polymathrobotics/protective-stop/docs/Hardware.md

# Hardware

## Materials

- Raspberry Pi Zero 2 W ([Raspberry Pi](https://www.raspberrypi.com/products/raspberry-pi-zero-2-w/))
- UPS Expansion Board for Raspberry Pi Zero 2 W ([Geekworm](https://www.amazon.com/Geekworm-Raspberry-18650-Expansion-Include/dp/B0B74NT38D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,electronics,140&sr=1-3))
- Heatsink for Raspberry Pi Zero 2 W ([Geekworm](https://www.amazon.com/Geekworm-Raspberry-Heatsink-Aluminumn-Compatible/dp/B09QMBCXLB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))
- E-ink display ([Waveshare](https://www.amazon.com/2-13inch-Display-HAT-Two-Color-Raspberry/dp/B07Z1WYRQH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,aps,152&sr=8-5))
- Cell modem SIM7600X 4G HAT
- Push button ([uxcell](https://www.amazon.com/dp/B07Z2TY2SZ))
- ESP32
- Electrical wire ([Fermerry 28 AWG](https://www.fermerry.com/products/fermerry-28-awg-stranded-wire-silicone-cables-hook-up-wire-kit-6-colors-5ft-each-28-gauge-electrical-wire))
- E-Stop Button
- Electric tape
- 40-GPIO header ([Vilros](https://www.amazon.com/Vilros-Solderless-Hammer-Header-Raspberry/dp/B09XVPYYTX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,aps,160&sr=8-2))
- Cell modem SIM7600X 4G HAT
- microUSB to microUSB cable
- microUSB to USB cable

## Assembly Instructions
### Preliminary Steps
1. Tape over Raspberry Pi USB connections
<p align="center">
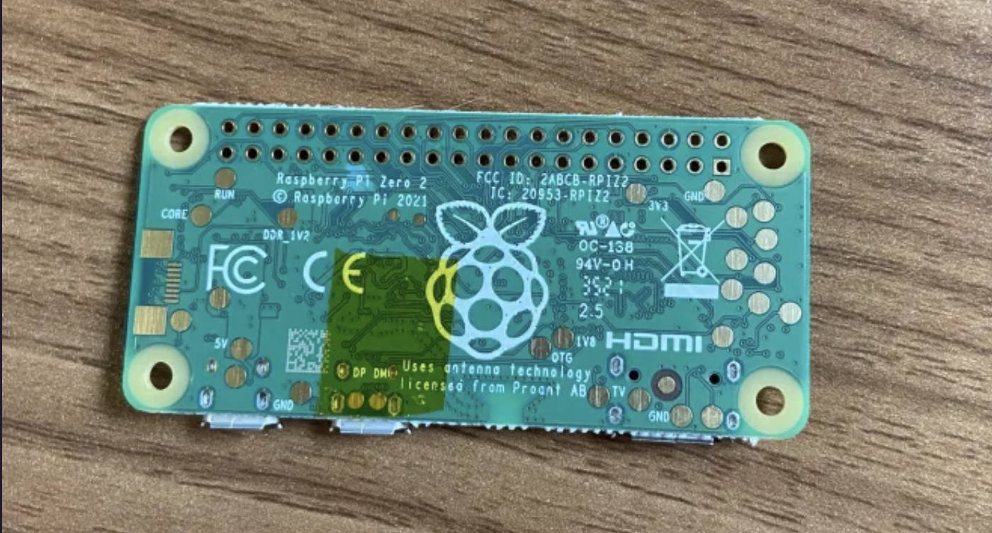
[picture p3: docs/img/rpi-tape.png]
  
</p>

2. Solder Raspberry Pi GPIO pin extender
- Use flux to make soldering easier
- Secure a few pins on each end first for better stability
- May want to clean singe marks from flux after soldering; we used a toothbrush and water for this.
<p align="center">
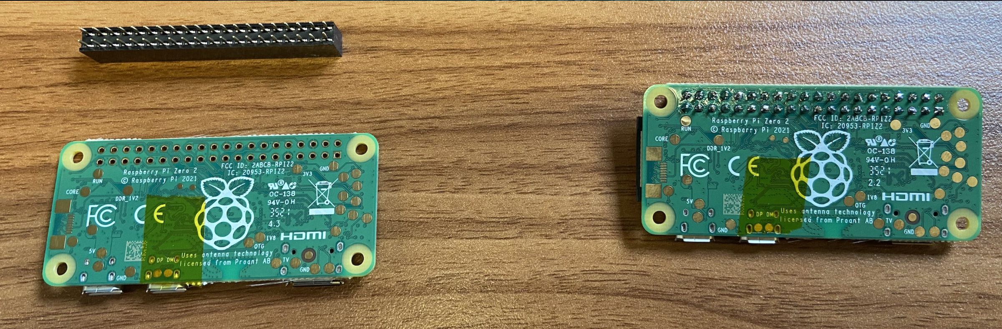
[picture p4: docs/img/soldered-rpi.png]
  <br><i> Left = before, right = after </i>
</p>

3. Apply Raspberry Pi heat sink.
- The Geekworm heatsink we used came with two thermal pads, one is 0.5mm and the other is 1mm. Make sure each pad goes in the right place! It comes with a diagram.
<p align="center">
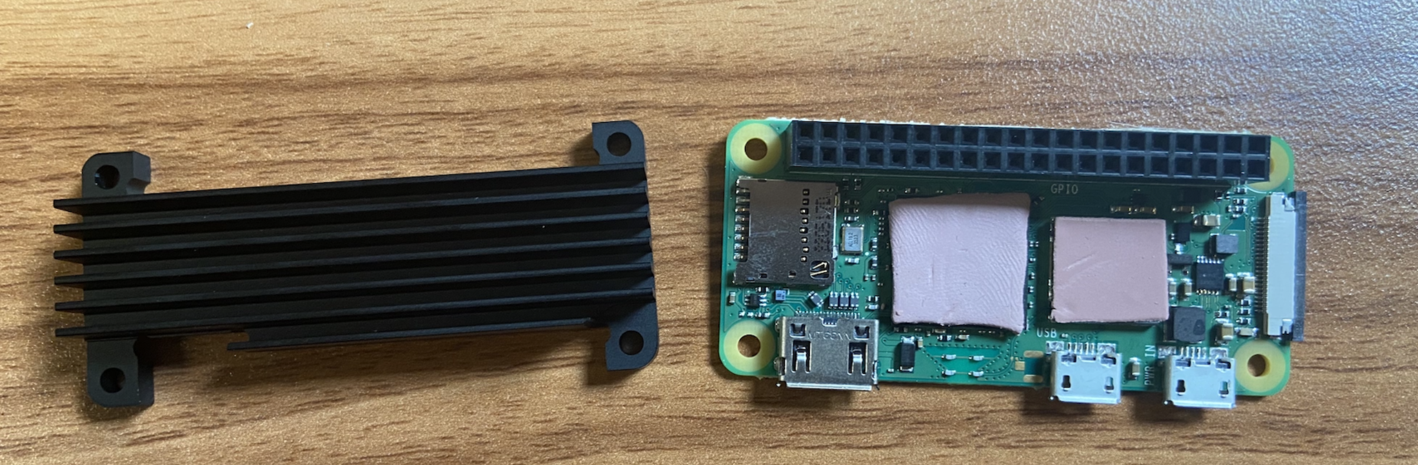
[picture p5: docs/img/heatsink.png]
   <br><i> Before </i>
</p>
<p align="center">
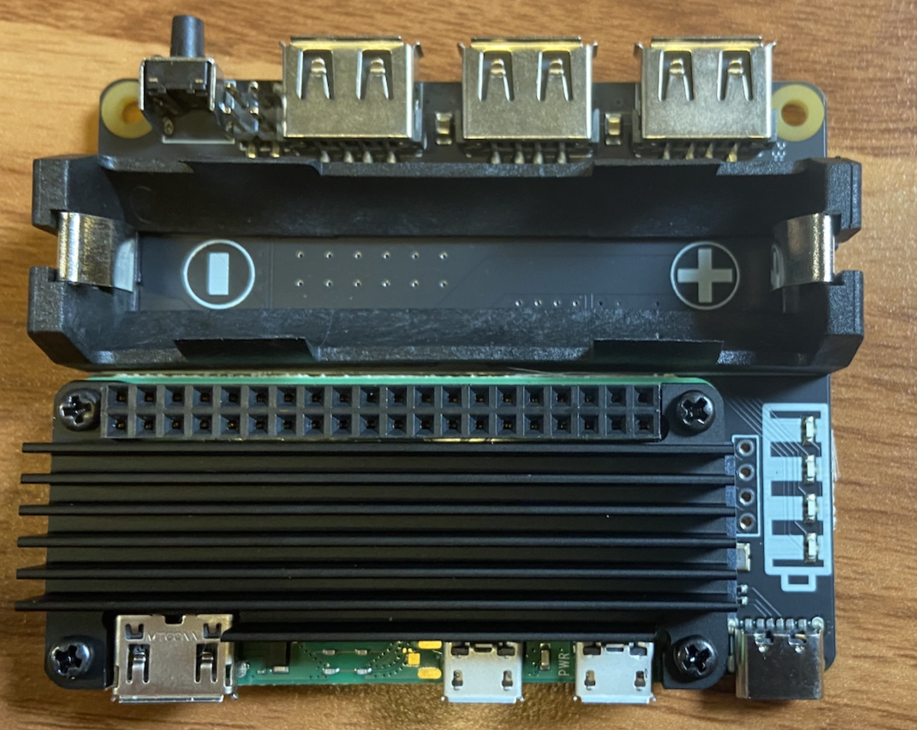
[picture p6: docs/img/applied-heatsink.png]
   <br><i> After </i>
</p>

- Screw on the heatsink to the Raspberry Pi, and through to the UPS.

<p align="center">
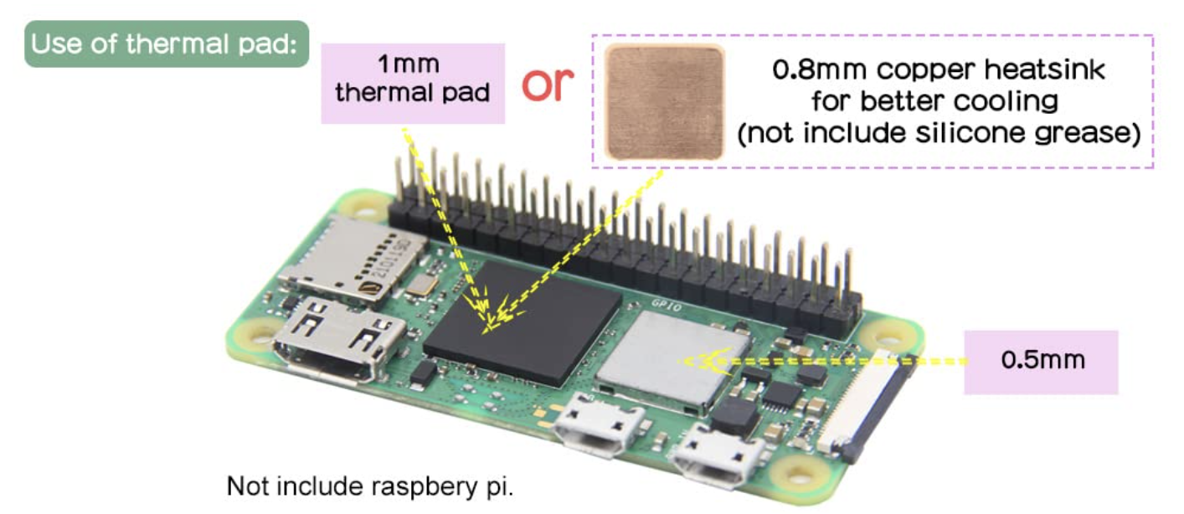
[picture p7: docs/img/thermal-pad-placement.png]
   <br><i> Thermal Pad Placement </i>
</p>

4. Add e-ink display to UPS using GPIO header.
<p align="center">
   <br><i> Top to bottom: UPS, GPIO header, e-ink display </i>
</p>
<p align="center">
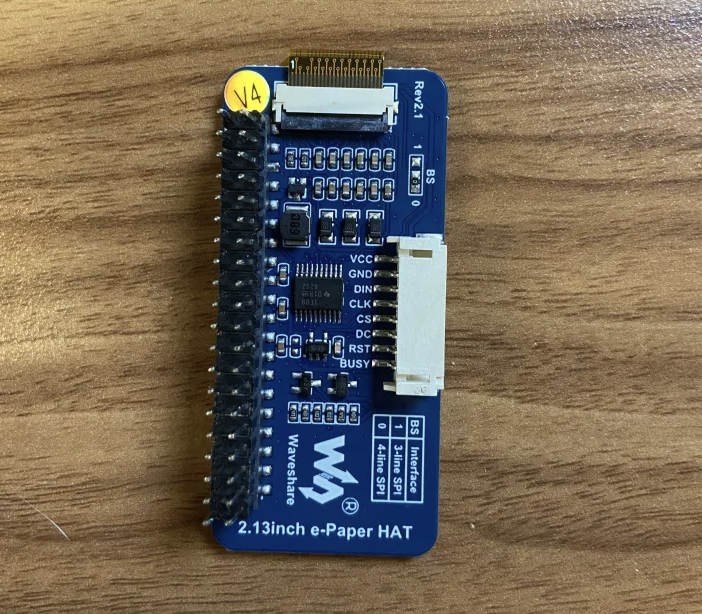
[picture p8: docs/img/gpio-2.png]
   <br><i> Add header to underside of e-ink </i>
</p>
<p align="center">
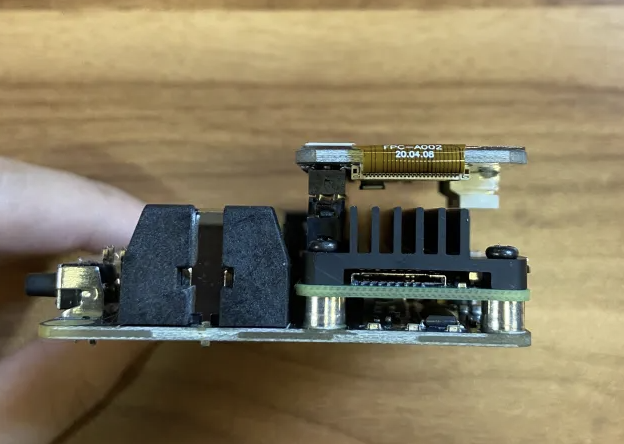
[picture p9: docs/img/gpio-3.png]
   <br><i> Install e-ink to UPS by plugging in GPIO header to pins </i>
</p>

## Wiring
Now it’s time to starting connecting stuff together. The connections at a glance are shown below.
```mermaid
graph TD
    USB-C -->|Power Out| UPS(UPS)
    UPS(UPS) -->|Power Out| R(Raspi)
    R -->|Control| ES(Eink Screen)
    R <-->|USB Power and Data| C(Cell Modem)
		C -->|USB Power and Data| E(ESP32)
    E -->|D2 to DI, + and GND| L(LED Ring)
    E -->|D22 to switch, + and GNDx2| PB(Power Button)
    PB -->|switch to input| UPS
    UPS -->|Lowbat to D34| E
    EB(Estop Button) -->|C to D18| E
    EB -->|NC to D21| E
    EB -->|NO to D19| E

    classDef component fill:#346beb,stroke:#333,stroke-width:2px;
    class USB-C,UPS,R,E,C,ES,L,PB,EB component;
```

### Wire Soldering
We will go through the wire soldering connections in the diagram above one by one. The color of the wires does not actually matter, but they are referred to throughout these instructions to enhance clarity.

1. Stop Button to ESP32
- Stop Button C → ESP32 D18 (Blue wire)
- Stop Button NO → ESP32 D19 (Yellow wire)
- Stop Button NC → ESP32 D21 (White wire)
- Don't forget to put O-ring on E-stop button!

<p align="center">
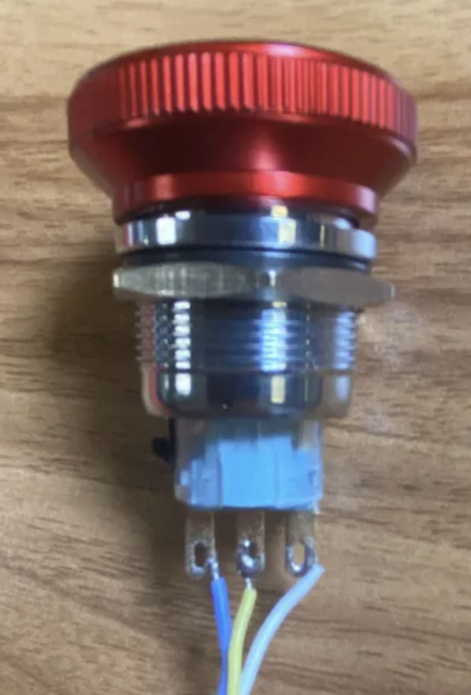
[picture p10: docs/img/stopbutton.png]
   <br><i> Stop button wiring </i>
</p>
<p align="center">
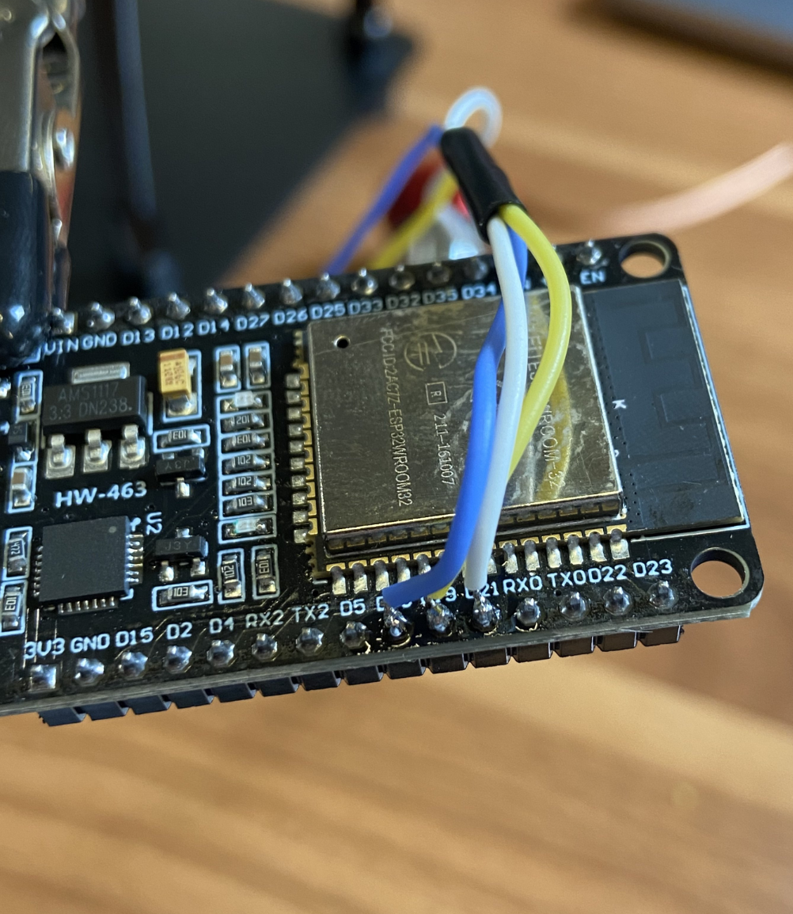
[picture p11: docs/img/stopbutton-esp.png]
   <br><i> Corresponding ESP32 wiring for stop button </i>
</p>

2. LED Ring to ESP32
- LED Ring DI → ESP32 D2 (Green wire)
- LED Ring PWR5V → ESP32 VIN (Red wire)
- LED Ring GND → ESP32 GND (Black wire)

<p align="center">
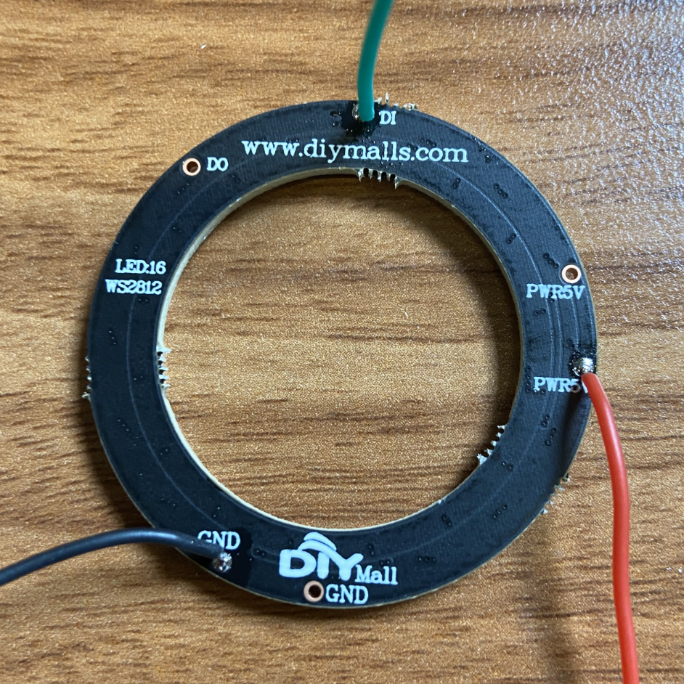
[picture p12: docs/img/ledring.png]
   <br><i> LED ring wiring </i>
</p>
<p align="center">
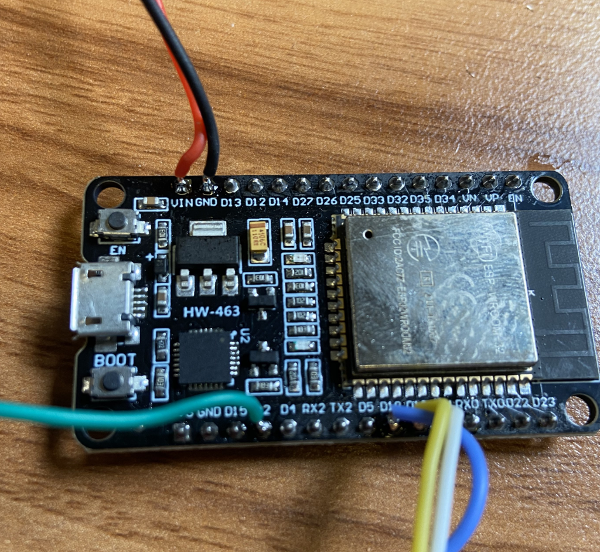
[picture p13: docs/img/ledring-esp32.png]
   <br><i> Corresponding ESP32 wiring for LED ring </i>
</p>

3. Power Button to ESP32 and UPS
- Power Button LED power terminal  → ESP32 D22 and UPS pin 3 (White wires)
- Power Button LED ground and switch contact A → ESP32 GND (Black wire)
- Power Button switch contact B→ ESP32 D23 (Red wire)
- Don’t forget to put O-ring on power button!

<p align="center">
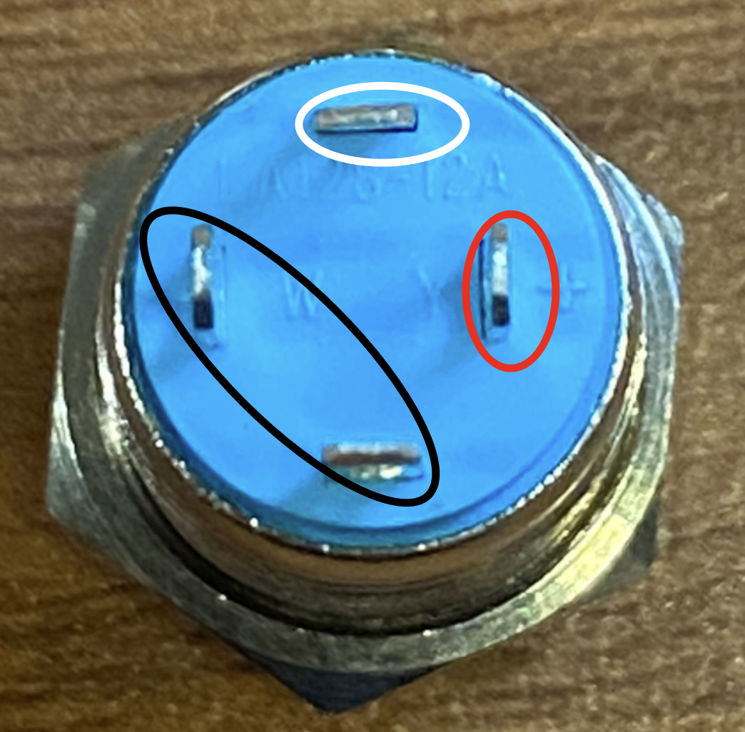
[picture p14: docs/img/powerbutton-colors.png]
   <br><i> Color of oval corresponds color of wire to connect to terminal. </i>
</p>
<p align="center">
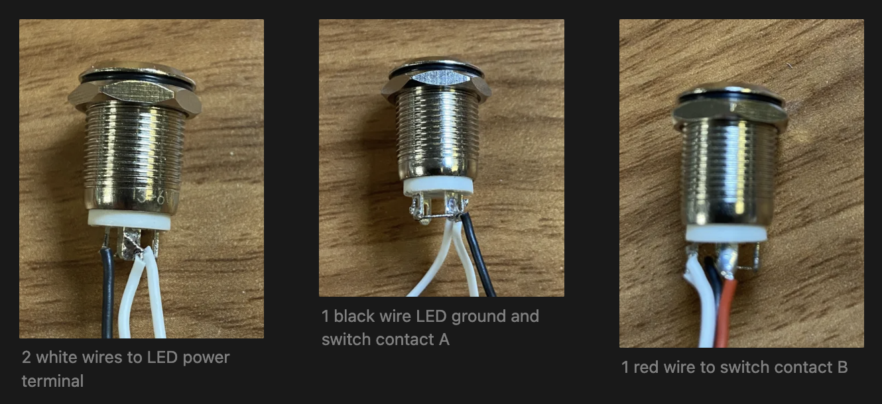
[picture p15: docs/img/powerbutton-wires.png]
   <br><i> Corresponding ESP32 wiring for LED ring </i>
</p>
<p align="center">
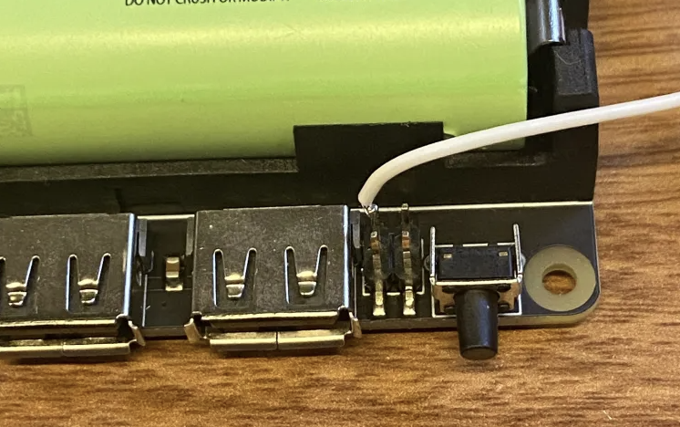
[picture p16: docs/img/powerbutton-white.png]
   <br><i> White wire soldered to UPS </i>
</p>
<p align="center">
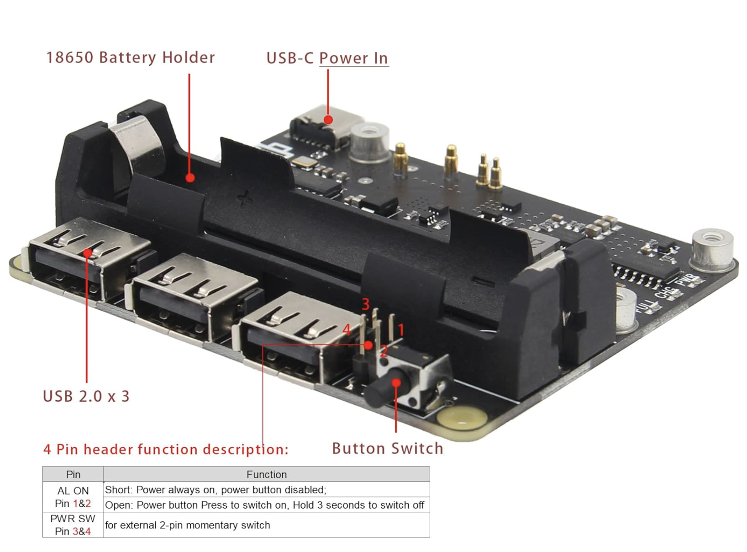
[picture p17: docs/img/ups-diagram.png]
   <br><i> Diagram of UPS </i>
</p>
<p align="center">
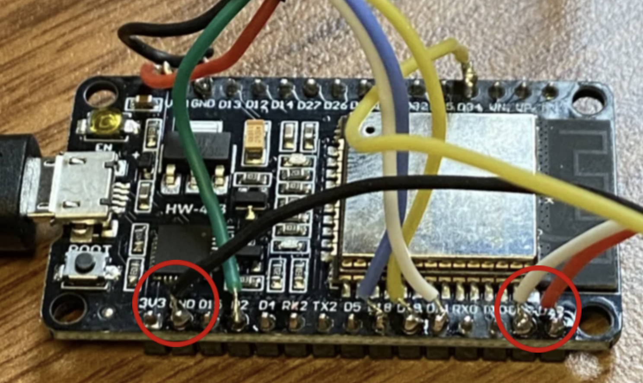
[picture p18: docs/img/powerbutton-esp32.png]
   <br><i> Black, white, and red wires soldered to ESP32 </i>
</p>

- Two white wires should be connected to the same terminal on the button (power button LED power terminal)
    - Tip: Solder these wires together first, and then solder them to the terminal
- The black wire is soldered across two power button terminals (power button LED ground and switch contact A)
    - Tip: Solder the end of the wire to the further terminal first, then the closer one
- Red wire is soldered normally

4. UPS to ESP32 (battery indicator)
- Lowbat to D34 (yellow wire)
<p align="center">
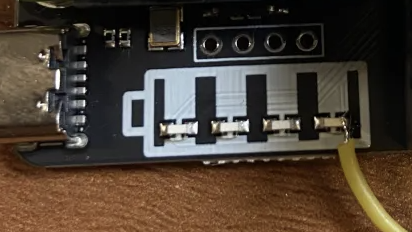
[picture p19: docs/img/ups-lowbat.png]
   <br><i> UPS lowbat soldering </i>
</p>
<p align="center">
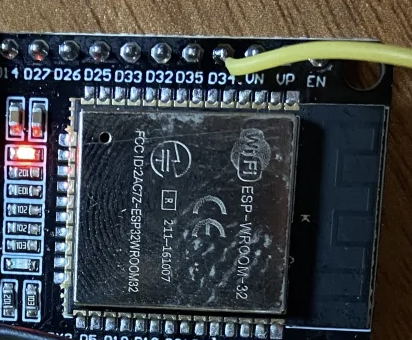
[picture p20: docs/img/esp-d34.png]
   <br><i> ESP32 pin D34 soldering </i>
</p>

5. Connect cell modem to ESP32 and RPi UPS.
- Modem USB → ESP32 microUSB (solid black cable)
- Modem microUSB → UPS microUSB (black/white cable)

6. Add battery to USP.
<p align="center">
   <br><i> Wired and connected system. </i>
</p>

7. Add antennas - if you want to use cellular data instead of WiFi
- Screw on antennas to AUX and MAIN pins on the underside of the modem

Now you're ready to move onto [Software](/docs/Software.md)
