polymathrobotics/protective-stop/docs/NET_ROBUSTNESS_2026-08-03.md

<!-- SPDX-FileCopyrightText: 2026 Polymath Robotics, Inc. -->
<!-- SPDX-License-Identifier: Apache-2.0 -->

# Network-Stack Robustness — USB-NCM + W5500 (2026-08-03)

Build `fa8b442`. Hardens the transport under the safety UDP link, driven by the
6 h soak finding that a USB-NCM remote intermittently dropped a heartbeat frame
(lwip `ERR_IF`, `g_sf_txdrv`) and — after enough consecutive drops — opened a
>1.2 s gap that would trip the machine's heartbeat STOP and force an operator
re-arm. Two research passes (USB-NCM + W5500) produced the proposals; the
low-risk, safety-latency-neutral subset was implemented and tested.

## Root cause (USB-NCM)

`sess_sendto()` did a single `sendto()`; on a transient NCM refusal (all IN NTBs
momentarily in-flight waiting for the USB host to poll bulk-IN) it dropped the
frame and waited a full 200 ms tick. On W5500 Ethernet this never happens (the
SPI driver queues the frame and returns OK). It is USB-NCM-specific, under TX load.

## Changes implemented

**USB-NCM**
- **NTB free-list 2 → 4** (`CONFIG_TINYUSB_NCM_IN_NTB_BUFFS_COUNT`, both projects) —
  widens the pool `tud_network_can_xmit()` draws from. +6.4 KB DRAM (heap verified
  fine, ~7.9 MB free).
- **Bounded yielding retry-on-ERR_IF** in `sess_sendto()` — up to 3 retries,
  `vTaskDelay(1)` between, so the lower-priority (5) TinyUSB task can free an NTB;
  the resend lands in the SAME 200 ms tick, no gap. **Gated on `errno == -1`
  (ERR_IF) only** — a genuinely dead link (route / ENOMEM) still fails on the first
  attempt, so **dead-link detection latency is unchanged** (the machine's 1.2 s
  heartbeat STOP and the 1.5 s local rebond threshold are untouched).
- **`pstop_sf_txdrv_recovered`** counter added to `/state.json` — counts transients
  absorbed by the retry, so the effect is measurable.

**W5500 Ethernet** (flawless in the soak; proactive margin only)
- SPI **`input_delay_ns = 20`** — sampling-edge margin (freq limit 40 MHz vs the
  20 MHz clock, so pure signal-integrity headroom, no behavioural change).
- **`LWIP_DHCP_RESTORE_LAST_IP`** — fast, deterministic IP reacquire after a link
  bounce instead of a full re-DHCP.

## Deferred (documented for a fault-injection-tested follow-up)

> **STATUS 2026-08-05 — the half-open black-hole family is now CLOSED + validated.**
> The three detection layers all shipped and are on main (`7867d4b`):
> - **W5500 health-watchdog + reset-recovery ladder** — `dcs_eth.c`
>   (`eth_blackhole_suspected()`, `DCS_ETHWD_REASON_BLACKHOLE`, RST-pulse ladder);
>   HW-validated on real silicon via a throwaway fault-injector (all 3 rungs,
>   `eth_recoveries` 0→3, restored each time). Closes the "driver wedges, link UP,
>   traffic black-holes, no disconnect event" field failure. **DONE.**
> - **Control-plane half-open** — coord watchdog fed by *received* activity only
>   (`ml_coord.c`; a send no longer masks a dead peer). **DONE.**
> - **Safety-path half-open** — validated 2026-08-05 via a controlled **sustained
>   90 s bidirectional black-hole** on a bonded slot (chaos proxy): the bond
>   detected within ~10 s (state→1, correctly *not* bonded — no false "up"), stayed
>   correctly not-bonded the whole 90 s (no wedge), and **recovered in 2.0 s** the
>   instant the path returned, no manual intervention. **NO WEDGE.**
>
> Remaining below are smaller, lower-value, or lockstep-timing-sensitive:

- **Instant demote-on-link-down** (event-driven failover kick; key failover off
  link state with asymmetric debounce) — partly covered by the `dcs_net_liveness`
  route supervisor (pstop-silence cross-check demote); a pure event-driven kick
  is the residual.
- TinyUSB task-priority bump (interacts with lockstep timing); Ethernet TX mutex
  (priority-inversion risk on the safety send); full static IP (deployment choice).

## Test results

**USB-NCM fix — PSTOP54 (USB-NCM, live safety link to machn), 40 min on `fa8b442`:**

| Metric | Result |
|---|---|
| `txdrv` (UNrecovered drops) | **0** |
| `txdrv_recovered` (absorbed by retry) | **5** |
| `pstop_rebonds` (steady-state) | **0** (2 total, both OTA-reboot settling) |
| reply rate (35 min window) | **100 %** (+10,500 / +10,500) |
| free heap | stable ~7.9 MB |

Before the fix (6 h soak): 17 `txdrv` drops + ~9 steady-state rebonds. After: 0
drops, 0 steady-state rebonds, 5 transients cleanly recovered. The nuisance-stop
precursor is eliminated, and because the retry is ERR_IF-gated the dead-link STOP
latency is unchanged.

**Armed safety-function regression — DUT (`0x01d7f344`) via HIL relays on `fa8b442`:**

| Step | Result |
|---|---|
| loops open (pressed) | both-phase sampling detects open (e_hi → 0) |
| arm (press → release) | machine → **OK (armed)** |
| press while armed | machine → **STOP** |
| re-arm | machine → **OK (armed)** |
| ~105 s armed hold | **no spurious STOP** |

The transport changes did not regress the safety logic: arm / STOP / re-arm all
correct, and every STOP transition mapped to a deliberate press.

## Protocol rebase to v1 (far-Hamming) + fleet migration

While this work was in flight, `6276bf0` ("Changing message values to avoid bit
flipping errors", J. Hinke) landed on `pstop`: `PSTOP_VERSION 0x00→0x01` and
far-Hamming message codewords (`OK 0x00→0x55`, `STOP 0x01→0x92`, `BOND→0xAD`,
`UNBOND→0x6A`) — the button-integrity safety improvement (zeroed/stuck/single-bit
→ invalid → STOP). It touches only `pstop_c`, so the transport fix above rebased
onto it cleanly (no conflict). **v0 and v1 are wire-incompatible** (version +
codewords), so the fleet was migrated in one pass.

The combined **v1 + transport-fix** build is `25c419f`. It was re-validated on the
wire before rollout (the earlier fa8b442 results were v0):

- **Bond on v1:** PSTOP54 ↔ machn re-bonded on the far-Hamming protocol, ~100 %
  reply rate, `sent` climbing steadily; USB retry active (`recovered` incrementing).
- **Armed on v1** (DUT via HIL relays + a v1 host runner): arm→RUN, press→STOP,
  re-arm→RUN, both-phase open-detection — all correct, identical to v0.
- **15-min stability** (all four units on `25c419f`): 0 reboots, 0 fault resets,
  `pstop_mismatch=0` on the continuously-running units, heap stable. (The DUT's
  transient mismatch count is an artifact of the armed test's sequential
  loop-relay switching — the intended single-channel discordance→STOP — not a
  fault.)

**Fleet:** `25c419f` published to the fleet for **both** projects (`pstop_remote`
and `machn_machine` — the first machn build ever on the fleet); all four reachable
units OTA-migrated to v1; offline units adopt v1 on next check-in.
