polymathrobotics/protective-stop/docs/img/pstop-ces.png

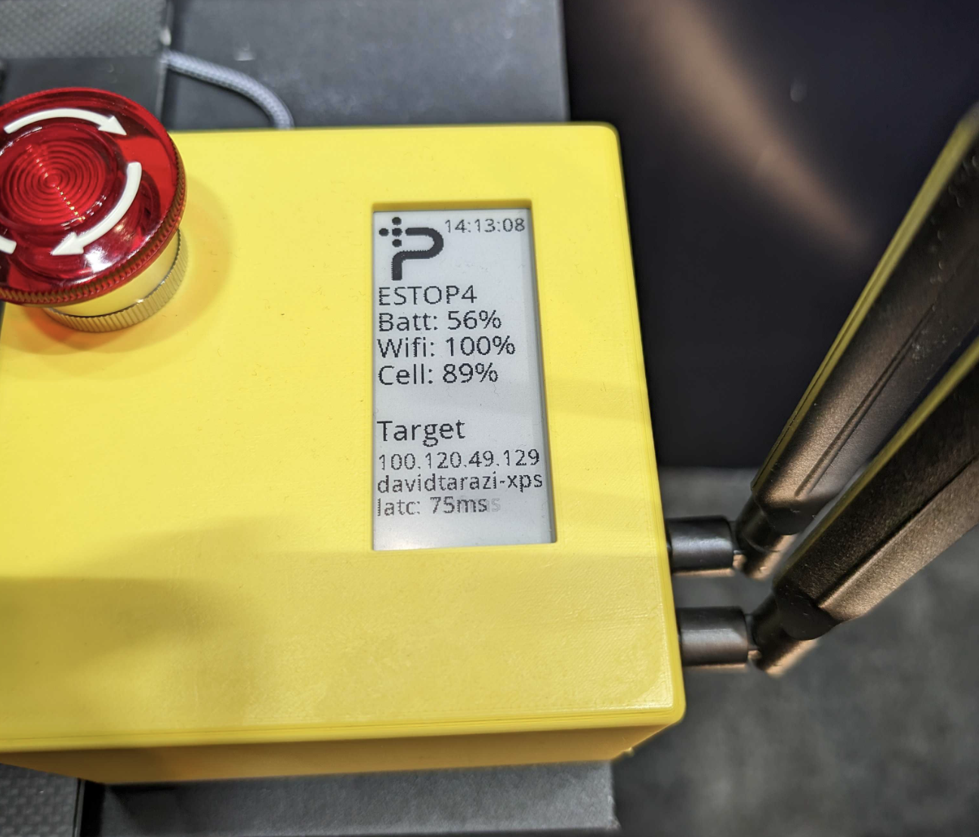
docs/img/pstop-ces.png
