polymathrobotics/protective-stop/firmware/components/dcs_support/src/dcs_support.c

// SPDX-FileCopyrightText: 2026 Polymath Robotics
// SPDX-License-Identifier: Apache-2.0

/**
 * @file dcs_support.c
 * @brief Top-level bring-up orchestrator. Calls into the per-file modules
 * (dcs_nvs, dcs_safety, dcs_boot, dcs_net_liveness, dcs_telemetry,
 * dcs_admin_pages) in the right order.
 */

#include "dcs_support.h"

#include <stdatomic.h>
#include <stdbool.h>
#include <stdlib.h>
#include <string.h>

#include "dcs_identity.h"
#include "dcs_internal.h"
#include "esp_heap_caps.h"
#include "esp_log.h"
#include "esp_secure_boot.h"
#include "esp_system.h"
#include "esp_timer.h" /* primary-machine freshness clock (same domain as main.c) */
#include "freertos/FreeRTOS.h"
#include "freertos/idf_additions.h" /* xTaskCreatePinnedToCoreWithCaps */
#include "freertos/semphr.h" /* operator-allowlist writer mutex */
#include "freertos/task.h"
#include "microlink.h"
#include "ml_app.h"
#include "ml_dev_tether.h"
#include "nvs_flash.h"
#include "panic_log.h"
#include "pstop/pstop_msg.h" /* PSTOP_MESSAGE_OK = machine armed/running (primary rule) */
#include "pstop_aux_channel.h" /* pstop_aux_role_t: remote self-role values */

static const char * TAG = "dcs_support";

/* See the doc comment on the declaration in dcs_internal.h for the contract a
 * PSRAM-stack task must honour (no flash/NVS, no ISR access). */
TaskHandle_t dcs_task_spawn_psram(
  TaskFunction_t fn, const char * name, uint32_t stack, void * arg, UBaseType_t prio, BaseType_t core)
{
  TaskHandle_t h = NULL;
  if (
    (xTaskCreatePinnedToCoreWithCaps(fn, name, stack, arg, prio, &h, core, MALLOC_CAP_SPIRAM | MALLOC_CAP_8BIT) ==
     pdPASS) &&
    (h != NULL))
  {
    ESP_LOGI(TAG, "task '%s' (%u B stack) created in PSRAM", name, (unsigned)stack);
    return h;
  }
  ESP_LOGW(TAG, "PSRAM stack for '%s' unavailable — falling back to internal RAM", name);
  h = NULL;
  if (xTaskCreatePinnedToCore(fn, name, stack, arg, prio, &h, core) == pdPASS) {
    return h;
  }
  ESP_LOGE(TAG, "task '%s' create FAILED", name);
  return NULL;
}

/* v15.27 — graceful Tailscale quiesce on any esp_restart() path.
 *
 * Runs from esp_register_shutdown_handler(), which fires for *any*
 * call to esp_restart() (admin restart, /api/usb_enable, the v15.24
 * auto-recovery, the never-brick fallback, etc) but does NOT fire on
 * panic. So this hook only mitigates *graceful* restarts where some
 * WG packet processing might be mid-flight. Work is limited to what's
 * safe with interrupts about to be disabled: a flag flip + a
 * vTaskSuspend, both effectively instant.
 *
 * Motivation: a single panic seen during a WiFi→USB mode transition,
 * backtrace lost (no serial on the test rig). Suspected race between
 * in-flight WG decrypt on ml_wg_mgr and esp_restart_noos's task-kill
 * sequence. Pausing DERP + suspending wg_mgr means no new packets
 * enter the processing pipeline from this point; anything already
 * mid-flight finishes within microseconds of the hook running. */
static void dcs_tailscale_quiesce_on_restart(void)
{
  microlink_pause_derp(true);
  if (g_dcs_wg_handle != NULL) {
    vTaskSuspend(g_dcs_wg_handle);
  }
}

/* === Process-wide state (declared extern in dcs_internal.h). =============== */
dcs_state_t g_dcs;

atomic_uint_fast32_t g_dcs_core_tick[2];
atomic_uint_fast32_t g_dcs_core_verdict[2];
atomic_uint_fast32_t g_dcs_xcheck_fault;
atomic_uint_fast32_t g_dcs_xcheck_hb[2];
atomic_uint_fast32_t g_dcs_gpio_cfg_fault;
atomic_uint_fast32_t g_dcs_load_pct[2];
atomic_uint_fast32_t g_dcs_estop_high_ok[2];
atomic_uint_fast32_t g_dcs_estop_low_ok[2];

atomic_uint_fast32_t g_dcs_pstop_sent;
atomic_uint_fast32_t g_dcs_pstop_replies;
atomic_uint_fast32_t g_dcs_pstop_last_msg; /* last PSTOP_MESSAGE_* received from the machine */
atomic_uint_fast32_t g_dcs_pstop_mismatch;
atomic_uint_fast32_t g_dcs_pstop_mm[7]; /* mismatch attribution — layout in dcs_internal.h */
atomic_uint_fast32_t g_dcs_pstop_mm_seq; /* seqlock for g_dcs_pstop_mm — see dcs_internal.h */
atomic_uint_fast64_t g_dcs_nvs_write; /* last dcs-side NVS write, start<<32 | duration — dcs_internal.h */
atomic_uint_fast32_t g_dcs_nvs_write_max; /* longest dcs-side NVS write this boot, ms */

void dcs_pstop_mm_snapshot(uint32_t out[7])
{
  /* Seqlock read: retry while the comparator is mid-write (odd) or wrote in
   * between. The writer runs once per 100 ms tick and the 7 stores take ~1 us,
   * so a retry is rare; after 8 tries return the last read (diagnostics only). */
  for (int attempt = 0; attempt < 8; attempt++) {
    uint32_t s1 = (uint32_t)atomic_load(&g_dcs_pstop_mm_seq);
    if ((s1 & 1u) != 0u) {
      taskYIELD();
      continue;
    }
    for (int i = 0; i < 7; i++) {
      out[i] = (uint32_t)atomic_load(&g_dcs_pstop_mm[i]);
    }
    atomic_thread_fence(memory_order_acquire); /* payload loads stay above the seq re-read */
    if ((uint32_t)atomic_load(&g_dcs_pstop_mm_seq) == s1) return;
  }
  /* 8 collisions in a row (writer runs once per 100 ms tick — effectively
   * never): deliver a best-effort copy rather than leave `out` untouched. */
  for (int i = 0; i < 7; i++) {
    out[i] = (uint32_t)atomic_load(&g_dcs_pstop_mm[i]);
  }
}

atomic_uint_fast32_t g_dcs_pstop_send_fail;
atomic_uint_fast32_t g_dcs_pstop_sf_nomem;
atomic_uint_fast32_t g_dcs_pstop_sf_route;
atomic_uint_fast32_t g_dcs_pstop_sf_txdrv;
atomic_uint_fast32_t g_dcs_pstop_sf_txdrv_recovered;
atomic_uint_fast32_t g_dcs_pstop_sf_other;
atomic_uint_fast32_t g_dcs_pstop_sf_enotconn;
atomic_uint_fast32_t g_dcs_pstop_sf_enotconn_kicks;
atomic_int g_dcs_pstop_sf_last_errno;
atomic_uint_fast32_t g_dcs_pstop_rtt_ms;
atomic_uint_fast64_t g_dcs_pstop_last_reply_ms;
atomic_uint_fast32_t g_dcs_pstop_peer_ip;
atomic_uint_fast32_t g_dcs_pstop_peer_port;

atomic_uint_fast64_t g_dcs_pstop_slot_ep[DCS_PSTOP_MAX_MACHINES];
atomic_uint_fast32_t g_dcs_pstop_slot_id[DCS_PSTOP_MAX_MACHINES];
/* Per-slot rebond request generation. /api/pstop_peers?slot=N&rebond=1 bumps
 * it; the comparator restarts that session's bond when it sees a new value.
 * This is how a REJECTED session (machine answered BOND with UNBOND) is
 * retried on command — it never retries on its own. */
static atomic_uint_fast32_t g_dcs_pstop_slot_rebond_gen[DCS_PSTOP_MAX_MACHINES];

void dcs_pstop_request_rebond(int slot)
{
  if ((slot >= 0) && (slot < DCS_PSTOP_MAX_MACHINES)) {
    atomic_fetch_add(&g_dcs_pstop_slot_rebond_gen[slot], 1u);
  }
}

uint32_t dcs_pstop_rebond_generation(int slot)
{
  if ((slot < 0) || (slot >= DCS_PSTOP_MAX_MACHINES)) {
    return 0u;
  }
  return (uint32_t)atomic_load(&g_dcs_pstop_slot_rebond_gen[slot]);
}

atomic_uint_fast32_t g_dcs_pstop_m_sent[DCS_PSTOP_MAX_MACHINES];
atomic_uint_fast32_t g_dcs_pstop_m_replies[DCS_PSTOP_MAX_MACHINES];
atomic_uint_fast32_t g_dcs_pstop_m_send_fail[DCS_PSTOP_MAX_MACHINES];
atomic_uint_fast32_t g_dcs_pstop_m_rebonds[DCS_PSTOP_MAX_MACHINES];
atomic_uint_fast32_t g_dcs_pstop_m_rtt_ms[DCS_PSTOP_MAX_MACHINES];
atomic_uint_fast32_t g_dcs_pstop_m_hb_ms[DCS_PSTOP_MAX_MACHINES];
atomic_uint_fast32_t g_dcs_pstop_m_last_msg[DCS_PSTOP_MAX_MACHINES];
atomic_uint_fast32_t g_dcs_pstop_m_state[DCS_PSTOP_MAX_MACHINES];
atomic_uint_fast64_t g_dcs_pstop_m_last_reply_ms[DCS_PSTOP_MAX_MACHINES];

/* Endpoint packing for g_dcs_pstop_slot_ep (see dcs_internal.h). */
#define PSTOP_EP_CONFIGURED (1ULL << 63)

static uint64_t pstop_ep_pack(bool configured, uint32_t ip, uint16_t port)
{
  return (configured ? PSTOP_EP_CONFIGURED : 0ULL) | ((uint64_t)ip << 16) | (uint64_t)port;
}

TaskHandle_t g_dcs_wg_handle;
atomic_int g_dcs_wg_paused;

atomic_uint_fast32_t g_dcs_heap_min_internal = UINT32_MAX;

atomic_int g_dcs_active_iface;
/* W5500 health-watchdog counters (written by dcs_eth.c's eth_wd task). */
atomic_uint_fast32_t g_dcs_eth_recoveries;
atomic_uint_fast32_t g_dcs_eth_rec_r1;
atomic_uint_fast32_t g_dcs_eth_rec_r2;
atomic_uint_fast32_t g_dcs_eth_rec_r3;
atomic_uint_fast32_t g_dcs_eth_rec_reason;
atomic_uint_fast32_t g_dcs_eth_spi_err;
atomic_uint_fast32_t g_dcs_eth_int_low_ticks;
atomic_uint_fast32_t g_dcs_eth_int_low_max_ms;
atomic_uint_fast32_t g_dcs_rgb_cycles;
atomic_uint_fast32_t g_dcs_pstop_rebonds;
atomic_uint_fast32_t g_dcs_relay_fault_a;
atomic_uint_fast32_t g_dcs_relay_fault_b;
atomic_uint_fast32_t g_dcs_relay_stop;
atomic_uint_fast32_t g_dcs_relay_feedback_monitored;
atomic_uint_fast32_t g_dcs_machn_arm_owner;
atomic_uint_fast32_t g_dcs_machn_restart_state;
atomic_uint_fast32_t g_dcs_machn_r_id[DCS_MACHN_MAX_REMOTES];
atomic_uint_fast32_t g_dcs_machn_r_state[DCS_MACHN_MAX_REMOTES];
atomic_uint_fast32_t g_dcs_machn_r_age_ms[DCS_MACHN_MAX_REMOTES];
atomic_uint_fast32_t g_dcs_machn_r_rtt_ms[DCS_MACHN_MAX_REMOTES];
atomic_uint_fast32_t g_dcs_machn_r_ip[DCS_MACHN_MAX_REMOTES];
atomic_uint_fast32_t g_dcs_machn_r_stop_only[DCS_MACHN_MAX_REMOTES];

/* Admission lists (allowlist + denylist) RAM caches. Lock-free for readers:
 * the safety cores scan these atomics from their remote_details callback,
 * never touching NVS/flash. Each slot holds 0 (empty) or a real remote id, so
 * a torn read can never FABRICATE a match — it can at worst miss a just-added
 * id or briefly still see a just-removed one (a lag, harmless: admission only
 * decides whether a remote may BOND, never whether it may re-arm). Writers
 * (admin API + boot load) serialize on g_dcs_lists_mtx and persist to NVS.
 * Loaded once at boot in dcs_support_init(); both empty on blank NVS =>
 * every remote is admitted. */
static atomic_uint_fast32_t g_dcs_lists[DCS_LIST_COUNT][DCS_MAX_LIST_IDS];
static SemaphoreHandle_t g_dcs_lists_mtx; /* writer serialization only */

static void pstop_slot_pins_sync(void);

static const char * list_name(dcs_list_t which)
{
  if (which == DCS_LIST_DENY) return "denylist";
  if (which == DCS_LIST_PIN) return "pinlist";
  return "allowlist";
}

static void dcs_lists_load_from_nvs(void)
{
  (void)dcs_nvs_migrate_legacy_operators(); /* must precede the PIN list load */
  for (int w = 0; w < DCS_LIST_COUNT; w++) {
    uint32_t ids[DCS_MAX_LIST_IDS];
    int n = dcs_nvs_read_list((dcs_list_t)w, ids);
    for (int i = 0; i < DCS_MAX_LIST_IDS; i++) {
      atomic_store(&g_dcs_lists[w][i], (i < n) ? ids[i] : 0u);
    }
    ESP_LOGI(TAG, "%s: %d id(s) loaded", list_name((dcs_list_t)w), n);
  }
}

bool dcs_list_contains(dcs_list_t which, uint32_t remote_id)
{
  if ((remote_id == 0u) || ((unsigned)which >= DCS_LIST_COUNT)) {
    return false;
  }
  for (int i = 0; i < DCS_MAX_LIST_IDS; i++) {
    if ((uint32_t)atomic_load(&g_dcs_lists[which][i]) == remote_id) {
      return true;
    }
  }
  return false;
}

int dcs_list_get(dcs_list_t which, uint32_t out[DCS_MAX_LIST_IDS])
{
  int n = 0;
  if ((unsigned)which >= DCS_LIST_COUNT) {
    return 0;
  }
  for (int i = 0; i < DCS_MAX_LIST_IDS; i++) {
    uint32_t id = (uint32_t)atomic_load(&g_dcs_lists[which][i]);
    if (id != 0u) {
      out[n++] = id;
    }
  }
  return n;
}

bool dcs_admission_allows(uint32_t remote_id)
{
  /* Deny wins. An empty allowlist admits everyone (the default, "open");
   * a populated one admits only listed ids ("paranoid"). */
  if (dcs_list_contains(DCS_LIST_DENY, remote_id)) {
    return false;
  }
  uint32_t probe[DCS_MAX_LIST_IDS];
  if (dcs_list_get(DCS_LIST_ALLOW, probe) == 0) {
    return true;
  }
  return dcs_list_contains(DCS_LIST_ALLOW, remote_id);
}

bool dcs_peer_pin_wanted(uint32_t remote_id)
{
  if (dcs_list_contains(DCS_LIST_DENY, remote_id)) {
    return false; /* never protect a slot for an id admission will refuse */
  }
  return dcs_list_contains(DCS_LIST_ALLOW, remote_id) || dcs_list_contains(DCS_LIST_PIN, remote_id);
}

/* Serialize a write, snapshot the current ids into a compact array, persist to
 * NVS, and only on NVS success republish the compacted set into the RAM cache.
 * Keeping NVS the source of truth means a failed write leaves RAM unchanged. */
static esp_err_t dcs_list_commit(dcs_list_t which, const uint32_t * ids, int count)
{
  esp_err_t r = dcs_nvs_write_list(which, ids, count);
  if (r != ESP_OK) {
    return r;
  }
  for (int i = 0; i < DCS_MAX_LIST_IDS; i++) {
    atomic_store(&g_dcs_lists[which][i], (i < count) ? ids[i] : 0u);
  }
  return ESP_OK;
}

esp_err_t dcs_list_add(dcs_list_t which, uint32_t remote_id)
{
  if ((remote_id == 0u) || ((unsigned)which >= DCS_LIST_COUNT)) {
    return ESP_ERR_INVALID_ARG;
  }
  if (g_dcs_lists_mtx != NULL) {
    (void)xSemaphoreTake(g_dcs_lists_mtx, portMAX_DELAY);
  }
  uint32_t ids[DCS_MAX_LIST_IDS];
  int n = dcs_list_get(which, ids);
  esp_err_t r = ESP_OK;
  bool present = false;
  for (int i = 0; i < n; i++) {
    if (ids[i] == remote_id) {
      present = true;
      break;
    }
  }
  if (present) {
    r = ESP_OK; /* idempotent */
  } else if (n >= DCS_MAX_LIST_IDS) {
    r = ESP_ERR_NO_MEM;
  } else {
    ids[n++] = remote_id;
    r = dcs_list_commit(which, ids, n);
  }
  if (g_dcs_lists_mtx != NULL) {
    (void)xSemaphoreGive(g_dcs_lists_mtx);
  }
  return r;
}

esp_err_t dcs_list_del(dcs_list_t which, uint32_t remote_id)
{
  if ((unsigned)which >= DCS_LIST_COUNT) {
    return ESP_ERR_INVALID_ARG;
  }
  if (g_dcs_lists_mtx != NULL) {
    (void)xSemaphoreTake(g_dcs_lists_mtx, portMAX_DELAY);
  }
  uint32_t ids[DCS_MAX_LIST_IDS];
  int n = dcs_list_get(which, ids);
  int w = 0;
  for (int i = 0; i < n; i++) {
    if (ids[i] != remote_id) {
      ids[w++] = ids[i];
    }
  }
  esp_err_t r = (w == n) ? ESP_OK /* absent: nothing to persist */ : dcs_list_commit(which, ids, w);
  if (g_dcs_lists_mtx != NULL) {
    (void)xSemaphoreGive(g_dcs_lists_mtx);
  }
  return r;
}

/* Remote self-role RAM mirror. Loaded at boot; dcs_role_set() updates it live
 * (both safety cores read it per frame), so a role change takes effect on the
 * next pstop frame without a reboot. */
static atomic_uint_fast32_t g_dcs_role;

static void dcs_role_load_from_nvs(void)
{
  uint8_t role = dcs_nvs_read_role(); /* fail-safe: stop_only unless explicitly operator */
  atomic_store(&g_dcs_role, role);
  ESP_LOGI(TAG, "remote role: %s", pstop_aux_role_str((pstop_aux_role_t)role));
}

uint8_t dcs_role_get(void)
{
  return (uint8_t)atomic_load(&g_dcs_role);
}

esp_err_t dcs_role_set(uint8_t role)
{
  if ((role != PSTOP_AUX_ROLE_STOP_ONLY) && (role != PSTOP_AUX_ROLE_OPERATOR)) {
    return ESP_ERR_INVALID_ARG;
  }
  esp_err_t r = dcs_nvs_write_role(role);
  if (r == ESP_OK) {
    atomic_store(&g_dcs_role, role);
    ESP_LOGI(TAG, "remote role -> %s (live)", pstop_aux_role_str((pstop_aux_role_t)role));
  }
  return r;
}

/* === DERP region auto-negotiation: §4.2 primary-machine feed ===============
 *
 * microlink derives the chip's DERP home region from the machine-slot table +
 * per-slot session state, both of which live HERE (the lock-free telemetry
 * atomics the comparator publishes every tick). Q1 decision (2026-08-10):
 * primary = the LOWEST-index bonded+ARMED slot — slot order is NVS
 * configuration, identical after power loss, whereas arming ORDER is history
 * that cannot be reconstructed across a reboot.
 *
 * "Armed" proxy per slot: session BONDED (state==2) AND the machine's last
 * reply message is PSTOP_MESSAGE_OK (a machn replies OK only while its safety
 * chain is closed/armed; STOP/BOND replies mean not armed) AND the reply is
 * FRESH (within the machine's own bond-drop window, hb×5, floor 3 s — the
 * same invariant sess_rebond_after_ms mirrors in main.c).
 *
 * Runs on the wg_mgr task at its 3 s self-heal cadence: atomics only, no
 * NVS/flash, no locks. On machn the slot table is empty, so this returns
 * nothing and microlink keeps the machine's legacy (fleet-anchor) behavior —
 * machines are region-authoritative and never follow a remote (design §4). */
static void dcs_primary_machine_info(void * ctx, microlink_primary_machine_info_t * out)
{
  (void)ctx;
  out->armed_primary_ip = 0u;
  out->configured_count = 0;
  const uint64_t now = (uint64_t)(esp_timer_get_time() / 1000);
  for (int i = 0; i < DCS_PSTOP_MAX_MACHINES; i++) {
    uint64_t ep = (uint64_t)atomic_load(&g_dcs_pstop_slot_ep[i]);
    if ((ep & PSTOP_EP_CONFIGURED) == 0ULL) {
      continue;
    }
    uint32_t ip = (uint32_t)((ep >> 16) & 0xFFFFFFFFULL);
    if (ip == 0u) {
      continue;
    }
    if (out->configured_count < MICROLINK_PRIMARY_MAX_MACHINES) {
      out->configured_ips[out->configured_count++] = ip; /* slot order preserved */
    }
    if (out->armed_primary_ip == 0u) { /* first (lowest) armed slot wins — Q1 */
      uint32_t st = (uint32_t)atomic_load(&g_dcs_pstop_m_state[i]);
      uint32_t lm = (uint32_t)atomic_load(&g_dcs_pstop_m_last_msg[i]);
      uint64_t lr = (uint64_t)atomic_load(&g_dcs_pstop_m_last_reply_ms[i]);
      uint32_t hb = (uint32_t)atomic_load(&g_dcs_pstop_m_hb_ms[i]);
      uint64_t fresh_ms = (hb != 0u) ? ((uint64_t)hb * 5u) : 3000u;
      if (fresh_ms < 3000u) {
        fresh_ms = 3000u;
      }
      bool bonded = (st == 2u); /* SESS_BONDED */
      bool armed = (lm == (uint32_t)PSTOP_MESSAGE_OK);
      bool fresh = (lr != 0u) && (now >= lr) && ((now - lr) <= fresh_ms);
      if (bonded && armed && fresh) {
        out->armed_primary_ip = ip;
      }
    }
  }
}

/* === Public API ============================================================ */

/* Must run before NVS init: a secure image on an unsecured chip would burn the
 * NVS HMAC key. Aborting lets OTA rollback restore the previous image. */
static void dcs_check_security_profile(void)
{
#if CONFIG_SECURE_BOOT
  const bool image_secure = true;
#else
  const bool image_secure = false;
#endif
  if (esp_secure_boot_enabled() != image_secure) {
    ESP_LOGE(TAG, "image and chip disagree on Secure Boot: refusing to run");
    abort();
  }
}

dcs_boot_state_t dcs_support_init(void)
{
  /* RTC_NOINIT log capture: must be first so we don't miss early boot logs. */
  panic_log_init();
  dcs_check_security_profile();

  /* Power-on sign of life: whole ring dim purple, before any network or
     * NVS work. Overwritten by the ring task once bring-up completes. */
  dcs_pstop_ring_bootsign();

  /* v15.27: register the Tailscale-quiesce shutdown hook before anything
     * else can call esp_restart(). Idempotent — runs once per process. */
  esp_err_t hook_err = esp_register_shutdown_handler(dcs_tailscale_quiesce_on_restart);
  if (hook_err != ESP_OK) {
    ESP_LOGW(TAG, "shutdown handler register: %s", esp_err_to_name(hook_err));
  }

  /* NVS up first — both our boot-counter and the usb_enabled flag live there. */
  esp_err_t nvs_err = nvs_flash_init();
  if ((nvs_err == ESP_ERR_NVS_NO_FREE_PAGES) || (nvs_err == ESP_ERR_NVS_NEW_VERSION_FOUND)) {
    esp_err_t erase_err = nvs_flash_erase();
    if (erase_err != ESP_OK) {
      ESP_LOGW(TAG, "nvs_flash_erase: %s", esp_err_to_name(erase_err));
    }
    nvs_err = nvs_flash_init();
  }
  if (nvs_err != ESP_OK) {
    ESP_LOGW(TAG, "nvs_flash_init early: %s", esp_err_to_name(nvs_err));
  }

  /* Boot-counter accounting + rollback decision. Does NOT return if it
     * decides to invoke esp_ota_mark_app_invalid_rollback_and_reboot(). */
  dcs_safety_account_boot();

  /* Lifetime health counters: boots/flash/OTA accounting. Must run before
     * ml_app_start (which may mark the OTA image valid on connect) so the
     * PENDING_VERIFY state is still observable. */
  dcs_health_init();

  /* Resolve NVS-backed user toggles. */
  g_dcs.usb_enabled = dcs_nvs_read_usb_enabled();
  g_dcs.ts_boot_en = dcs_nvs_read_ts_boot_en();

  /* Safety ladder: boot_count==1 → drop direct-UDP path only;
     *                 boot_count>=2 → full Tailscale pause. */
  if (g_dcs.ts_boot_en && (g_dcs.boot_count == 1u)) {
    ESP_LOGW(TAG, "SAFETY: bc=1 — forcing DERP-only mode for this boot");
    g_dcs.derp_only_mode = true;
  } else if (g_dcs.ts_boot_en && (g_dcs.boot_count >= 2u)) {
    ESP_LOGW(
      TAG,
      "SAFETY: ts_boot=1 but boot_count=%u — forcing Tailscale "
      "paused for this boot (safe mode)",
      g_dcs.boot_count);
    g_dcs.ts_boot_en = false;
  } else {
    /* boot_count 0: no safety-ladder action */
  }
  ESP_LOGI(
    TAG, "Boot: usb_enabled=%d ts_boot_en=%d boot_count=%u", g_dcs.usb_enabled, g_dcs.ts_boot_en, g_dcs.boot_count);

  /* TWDT keep-alive. */
  dcs_safety_start_heartbeat();

  /* USB "PSTOPxx" unit number: admin-set value from NVS, or 0 = derive from
     * the chip ID. Must be set before ml_app_start (its try_alt_network hook can
     * bring up the USB tether, which fixes the descriptor at TinyUSB install). */
  ml_dev_tether_set_unit_number(dcs_nvs_read_pstop_unit_num());

  /* ml_app config — same defaults as the pre-refactor main.c. */
  ml_app_config_t cfg = ML_APP_CONFIG_DEFAULT();
  cfg.max_peers = 128; /* PSRAM-backed; load paths budgeted */
  /* Register on the tailnet as "pstop-01xxxxxx", matching the black-channel
     * device ID (dcs_identity_*). Stable per unit; static buffer, safe to hold. */
  cfg.device_name = dcs_identity_hostname();
  ESP_LOGI(
    TAG,
    "Identity: tailnet=%s  pstop device_id=0x%08x "
    "(machine must allow_unlisted or list this ID)",
    dcs_identity_hostname(),
    (unsigned)dcs_identity_device_id());
  cfg.enable_disco = !g_dcs.derp_only_mode;
  cfg.enable_stun = !g_dcs.derp_only_mode;
  cfg.try_alt_network = dcs_boot_try_tether_or_skip;
  cfg.alt_network_timeout_ms = 30000;
  /* httpd URI-handler budget. The server holds 16 + this many slots
     * (ml_app.c). microlink registers ~20 of its own (config panel + /admin
     * API + fleet-ota + verbose) and dcs_admin_pages registers 18; at 16 the
     * total overflowed 32 and the LAST-registered app routes silently failed
     * to register (observed: /api/pstop_num and /api/enter_download 404'd on
     * shipped firmware). dcs now registers 29 on the remote (incl.
     * /api/admission + /api/role GET+POST, /api/health GET + reset POST);
     * 36 gives 52 total slots with headroom — re-check this
     * arithmetic whenever a route is added on either side. */
  cfg.max_user_uri_handlers = 36;
  g_dcs.app = ml_app_start(&cfg);
  g_dcs.ml_handle = ml_app_get_microlink(g_dcs.app);

  /* If an alt network took the default route, ml_app skipped wifi_init.
     * Bring the WiFi driver up in idle mode so admin endpoints touching
     * esp_wifi_* behave — EXCEPT on the wired-Ethernet path, where WiFi is
     * never used and esp_wifi_init() would burn ~30-50 KB of internal RAM we
     * can't spare (internal heap runs tight on this build; that pressure was
     * tipping the chip into intermittent allocation-failure panics). The
     * esp_wifi_* admin calls return ESP_ERR_WIFI_NOT_INIT rather than crash
     * when the driver is absent, so skipping it is safe. */
  if (dcs_boot_alt_network_won()) {
    if (dcs_eth_has_ip()) {
      /* Wired Ethernet: do NOT init the WiFi driver. It costs ~20-25 KB
             * internal RAM, and MEASURED (2026-06-23): always-initialising it
             * here on the eth path crushed heap_min to ~1.9 KB once the Tailscale
             * DERP-TLS handshake ran concurrently (vs ~46 KB skipped) and started
             * tripping early-boot reboots — i.e. it re-creates the very OOM
             * pressure the skip exists to avoid. The esp_wifi_* NULL-deref this
             * once caused in the admin status endpoints (an unguarded call on the
             * not-init driver crash-looped the device) is fixed at the call sites
             * instead — see the guards in dcs_admin_pages.c (/state.json) and
             * ml_config_httpd.c (/api/monitor). */
      ESP_LOGI(
        TAG,
        "wired Ethernet active — skipping WiFi driver init "
        "to preserve internal RAM (esp_wifi admin calls guarded)");
    } else {
      dcs_boot_wifi_idle_init(); /* USB-NCM path: keep WiFi driver */
    }
  }

  /* Onboard WS2812 RGB LED: colour = active interface (live), blink = IP
     * last octet. Replaces ml_ip_blink (which drove GPIO21 as a plain pin —
     * can't clock the board's addressable LED). */
  dcs_rgb_start();

  /* 16-LED WS2812 ring on GPIO17 — PSTOP safety state (separate from the
     * onboard single LED's network indicator). */
  dcs_pstop_ring_start();

  /* Initial peer targets (NVS-backed, legacy single peer migrated into
     * slot 0) — main.c reads the slots via dcs_get_pstop_peer_slot() before
     * and during the comparator's run. Slot 0 mirrors to the legacy atomics. */
  {
    dcs_pstop_peer_rec_t peers[DCS_PSTOP_MAX_MACHINES];
    dcs_nvs_read_pstop_peers(peers);
    for (int i = 0; i < DCS_PSTOP_MAX_MACHINES; i++) {
      atomic_store(&g_dcs_pstop_slot_ep[i], pstop_ep_pack(peers[i].configured, peers[i].ip, peers[i].port));
      atomic_store(&g_dcs_pstop_slot_id[i], peers[i].machine_id);
    }
    atomic_store(&g_dcs_pstop_peer_ip, peers[0].configured ? peers[0].ip : 0u);
    atomic_store(&g_dcs_pstop_peer_port, peers[0].port);
  }
  /* Pin every configured machine target in the WG peer table so the cap
     * trim can never orphan a safety link (see pstop_slot_pins_sync). */
  pstop_slot_pins_sync();

  /* DERP region auto-negotiation (§4.2): feed microlink the machine-slot
     * table + arming state so it can home on the PRIMARY machine's region
     * (lowest bonded+armed slot — Q1) and MBB-switch when the primary moves.
     * Registered on both roles: on machn the table is empty, so this is a
     * no-op feed and the machine keeps its legacy region behavior. */
  if (g_dcs.ml_handle != NULL) {
    microlink_set_primary_machine_cb(g_dcs.ml_handle, dcs_primary_machine_info, NULL);
  }

  /* Operator allowlist (machine-role authorization): create the writer mutex
     * and load the persisted ids into the lock-free RAM cache BEFORE main.c
     * spawns the safety cores (their remote_details callback reads the cache)
     * and before the admin API can mutate it. Empty on blank NVS = every remote
     * stop-only = safe. */
  g_dcs_lists_mtx = xSemaphoreCreateMutex();
  if (g_dcs_lists_mtx == NULL) {
    ESP_LOGW(TAG, "operator-allowlist mutex alloc failed — add/del will run unserialized");
  }
  dcs_lists_load_from_nvs();
  dcs_role_load_from_nvs(); /* remote self-role mirror, before the safety cores spawn */

  /* Register the admin pages now that ml_app is up. */
  dcs_admin_pages_register(g_dcs.app);

  /* Verbose ml_* logging — kept from pre-refactor; helps catch wedges. */
  esp_log_level_set("ml_wg_mgr", ESP_LOG_INFO);
  esp_log_level_set("ml_net_io", ESP_LOG_INFO);
  esp_log_level_set("ml_derp", ESP_LOG_INFO);
  esp_log_level_set("wireguard_lwip", ESP_LOG_INFO);
  esp_log_level_set("microlink", ESP_LOG_INFO);

  dcs_telemetry_start_sampler();
  dcs_health_start(); /* 1 Hz: NVS flush of lifetime counters + wear checks */
  dcs_net_supervisor_start(); /* 1 Hz Eth>USB>WiFi default-route enforcer */
  dcs_net_liveness_start();
  dcs_net_inet_start(); /* internet reachability -> red LED when down */

  /* Cache the ml_wg_mgr handle for the legacy /api/wg toggle. */
  g_dcs_wg_handle = xTaskGetHandle("ml_wg_mgr");

  /* Mirror into the public boot-state struct. */
  dcs_boot_state_t bs = {
    .usb_enabled = g_dcs.usb_enabled,
    .ts_boot_en = g_dcs.ts_boot_en,
    .derp_only_mode = g_dcs.derp_only_mode,
    .boot_count = g_dcs.boot_count,
    .reset_reason = g_dcs.reset_reason,
    .ctrl_reset_cause = g_dcs.ctrl_reset_cause,
    .ml_handle = g_dcs.ml_handle,
    .app = g_dcs.app,
  };
  return bs;
}

void dcs_support_finalize(const dcs_boot_state_t * bs)
{
  (void)bs;
  /* Mark current OTA partition valid — does NOT clear boot_count, so the
     * crash-loop signal survives until the Layer-4 age-out fires. */
  dcs_safety_mark_ota_valid();

  /* Layer 4: age-out the crash counter after sustained healthy uptime,
     * and (v15.24) auto-restart out of derp-only mode on success. */
  dcs_safety_start_bc_clear();

  /* If Tailscale was supposed to start paused this boot, suspend
     * ml_wg_mgr now (after our NVS reads completed earlier). The 500 ms
     * delay lets wg_mgr finish its own NVS peer-cache load. */
  if ((!g_dcs.ts_boot_en) && (g_dcs_wg_handle != NULL)) {
    microlink_pause_derp(true);
    vTaskDelay(pdMS_TO_TICKS(500));
    vTaskSuspend(g_dcs_wg_handle);
    atomic_store(&g_dcs_wg_paused, 1);
    ESP_LOGW(TAG, "ml_wg_mgr task suspended + DERP paused at boot");
  } else {
    ESP_LOGI(TAG, "Tailscale tasks active at boot (safety net: 4-crash rollback)");
  }
}

/* === Telemetry sinks ======================================================= */

void dcs_publish_core_tick(int core_id, uint32_t tick, uint8_t verdict)
{
  if ((core_id < 0) || (core_id > 1)) {
    return;
  }
  atomic_store(&g_dcs_core_tick[core_id], tick);
  atomic_store(&g_dcs_core_verdict[core_id], verdict);
  /* Lifetime press / mismatch edge counting (non-safety telemetry). */
  dcs_health_note_core_tick(core_id, tick, verdict);
}

void dcs_publish_xcheck(uint32_t fault, uint32_t hb0, uint32_t hb1)
{
  atomic_store(&g_dcs_xcheck_fault, fault);
  atomic_store(&g_dcs_xcheck_hb[0], hb0);
  atomic_store(&g_dcs_xcheck_hb[1], hb1);
}

void dcs_publish_gpio_cfg(uint32_t fault)
{
  atomic_store(&g_dcs_gpio_cfg_fault, fault);
}

void dcs_publish_estop(int core_id, bool high_ok, bool low_ok)
{
  if ((core_id < 0) || (core_id > 1)) {
    return;
  }
  atomic_store(&g_dcs_estop_high_ok[core_id], high_ok ? 1u : 0u);
  atomic_store(&g_dcs_estop_low_ok[core_id], low_ok ? 1u : 0u);
}

void dcs_publish_comparator(
  uint32_t sent, uint32_t mismatch, uint32_t send_fail, uint64_t last_reply_ms, uint32_t rtt_ms)
{
  atomic_store(&g_dcs_pstop_sent, sent);
  atomic_store(&g_dcs_pstop_mismatch, mismatch);
  atomic_store(&g_dcs_pstop_send_fail, send_fail);
  atomic_store(&g_dcs_pstop_last_reply_ms, last_reply_ms);
  atomic_store(&g_dcs_pstop_rtt_ms, rtt_ms);
}

void dcs_publish_relay_fault(uint32_t fault_a_ticks, uint32_t fault_b_ticks, bool stop_active, bool monitored)
{
  atomic_store(&g_dcs_relay_fault_a, fault_a_ticks);
  atomic_store(&g_dcs_relay_fault_b, fault_b_ticks);
  atomic_store(&g_dcs_relay_stop, stop_active ? 1u : 0u);
  atomic_store(&g_dcs_relay_feedback_monitored, monitored ? 1u : 0u);
}

void dcs_publish_machn_remote(
  int slot, uint32_t remote_id, uint32_t ip, uint32_t state, uint32_t age_ms, uint32_t rtt_ms, bool stop_only)
{
  if ((slot < 0) || (slot >= DCS_MACHN_MAX_REMOTES)) {
    return;
  }
  atomic_store(&g_dcs_machn_r_id[slot], remote_id);
  atomic_store(&g_dcs_machn_r_ip[slot], ip);
  atomic_store(&g_dcs_machn_r_state[slot], state);
  atomic_store(&g_dcs_machn_r_age_ms[slot], age_ms);
  atomic_store(&g_dcs_machn_r_rtt_ms[slot], rtt_ms);
  atomic_store(&g_dcs_machn_r_stop_only[slot], stop_only ? 1u : 0u);
}

void dcs_publish_machn_arm(uint32_t remote_stop_id, uint32_t restart_state)
{
  atomic_store(&g_dcs_machn_arm_owner, remote_stop_id);
  atomic_store(&g_dcs_machn_restart_state, restart_state);
}

void dcs_publish_pstop_sf_causes(
  uint32_t nomem,
  uint32_t route,
  uint32_t txdrv,
  uint32_t txdrv_recovered,
  uint32_t other,
  uint32_t enotconn,
  uint32_t enotconn_kicks,
  int last_errno)
{
  atomic_store(&g_dcs_pstop_sf_nomem, nomem);
  atomic_store(&g_dcs_pstop_sf_route, route);
  atomic_store(&g_dcs_pstop_sf_txdrv, txdrv);
  atomic_store(&g_dcs_pstop_sf_txdrv_recovered, txdrv_recovered);
  atomic_store(&g_dcs_pstop_sf_other, other);
  atomic_store(&g_dcs_pstop_sf_enotconn, enotconn);
  atomic_store(&g_dcs_pstop_sf_enotconn_kicks, enotconn_kicks);
  atomic_store(&g_dcs_pstop_sf_last_errno, last_errno);
}

bool dcs_tailnet_connected(void)
{
  return (g_dcs.ml_handle != NULL) && (microlink_get_state(g_dcs.ml_handle) == ML_STATE_CONNECTED);
}

void dcs_request_announce(void)
{
  if (g_dcs.ml_handle != NULL) {
    (void)microlink_request_announce(g_dcs.ml_handle);
  }
}

void dcs_publish_pstop_peer(uint32_t peer_ip, uint16_t peer_port)
{
  /* Legacy single-peer setter (/api/pstop_peer, provisioning tooling) = slot 0
   * with the default machine id. */
  esp_err_t werr = dcs_pstop_set_peer_slot(0, true, peer_ip, peer_port, DCS_PSTOP_DEFAULT_MACHINE_ID);
  if (werr != ESP_OK) {
    ESP_LOGW(TAG, "persist pstop peer: %s", esp_err_to_name(werr));
  }
}

/* Pin every configured slot target in the WG peer table (and unpin an IP
 * only when NO remaining slot uses it — two slots may target one host on
 * different ports). Without the pin, a machine that joined the tailnet
 * after this chip's last full netmap — or one with no recent traffic —
 * is trimmed by the peer cap and every BOND dies with EHOSTUNREACH. */
static void pstop_slot_pins_sync(void)
{
  if (g_dcs.ml_handle == NULL) {
    return;
  }
  for (int i = 0; i < DCS_PSTOP_MAX_MACHINES; i++) {
    uint64_t ep = (uint64_t)atomic_load(&g_dcs_pstop_slot_ep[i]);
    bool cfg = (ep & PSTOP_EP_CONFIGURED) != 0ULL;
    uint32_t ip = (uint32_t)((ep >> 16) & 0xFFFFFFFFULL);
    if (cfg && (ip != 0u)) {
      microlink_pin_peer_ip(g_dcs.ml_handle, ip, true);
    }
  }
}

esp_err_t dcs_pstop_set_peer_slot(int slot, bool configured, uint32_t ip, uint16_t port, uint32_t machine_id)
{
  if ((slot < 0) || (slot >= DCS_PSTOP_MAX_MACHINES)) {
    return ESP_ERR_INVALID_ARG;
  }
  /* Unpin the OLD target if this slot had one and no other slot shares it. */
  uint64_t old_ep = (uint64_t)atomic_load(&g_dcs_pstop_slot_ep[slot]);
  uint32_t old_ip = (uint32_t)((old_ep >> 16) & 0xFFFFFFFFULL);
  if (((old_ep & PSTOP_EP_CONFIGURED) != 0ULL) && (old_ip != 0u) && (g_dcs.ml_handle != NULL)) {
    bool shared = false;
    for (int i = 0; i < DCS_PSTOP_MAX_MACHINES; i++) {
      if (i == slot) continue;
      uint64_t ep = (uint64_t)atomic_load(&g_dcs_pstop_slot_ep[i]);
      if (((ep & PSTOP_EP_CONFIGURED) != 0ULL) && ((uint32_t)((ep >> 16) & 0xFFFFFFFFULL) == old_ip)) {
        shared = true;
        break;
      }
    }
    if (!shared && !(configured && (ip == old_ip))) {
      microlink_pin_peer_ip(g_dcs.ml_handle, old_ip, false);
    }
  }
  /* Live update first (comparator picks it up next tick)... */
  atomic_store(&g_dcs_pstop_slot_id[slot], machine_id);
  atomic_store(&g_dcs_pstop_slot_ep[slot], pstop_ep_pack(configured, ip, port));
  pstop_slot_pins_sync();
  if (slot == 0) {
    atomic_store(&g_dcs_pstop_peer_ip, configured ? ip : 0u);
    atomic_store(&g_dcs_pstop_peer_port, port);
  }
  /* ...then persist the whole table (read-modify-write of the blob). */
  dcs_pstop_peer_rec_t peers[DCS_PSTOP_MAX_MACHINES];
  dcs_nvs_read_pstop_peers(peers);
  /* run-47 shakeout: writing slot N>0 on a device whose machine target came
   * from the legacy key / compiled default (blob slot 0 unconfigured) must
   * not strand that ACTIVE target — once a blob exists it is authoritative,
   * so an unseeded slot 0 silently drops the live machine bond on the next
   * reload. Seed slot 0 from the live atomics before persisting. */
  if ((slot != 0) && !peers[0].configured) {
    uint64_t ep0 = (uint64_t)atomic_load(&g_dcs_pstop_slot_ep[0]);
    if ((ep0 & PSTOP_EP_CONFIGURED) != 0ULL) {
      peers[0].configured = true;
      peers[0].ip = (uint32_t)((ep0 >> 16) & 0xFFFFFFFFULL);
      peers[0].port = (uint16_t)(ep0 & 0xFFFFULL);
      peers[0].machine_id = (uint32_t)atomic_load(&g_dcs_pstop_slot_id[0]);
    }
  }
  peers[slot].configured = configured;
  peers[slot].ip = ip;
  peers[slot].port = port;
  peers[slot].machine_id = machine_id;
  return dcs_nvs_write_pstop_peers(peers);
}

void dcs_get_pstop_peer_slot(
  int slot, bool * configured, uint32_t * peer_ip, uint16_t * peer_port, uint32_t * machine_id)
{
  uint64_t ep = 0;
  uint32_t id = 0;
  if ((slot >= 0) && (slot < DCS_PSTOP_MAX_MACHINES)) {
    ep = atomic_load(&g_dcs_pstop_slot_ep[slot]);
    id = (uint32_t)atomic_load(&g_dcs_pstop_slot_id[slot]);
  }
  if (configured != NULL) {
    *configured = (ep & PSTOP_EP_CONFIGURED) != 0ULL;
  }
  if (peer_ip != NULL) {
    *peer_ip = (uint32_t)((ep >> 16) & 0xFFFFFFFFu);
  }
  if (peer_port != NULL) {
    *peer_port = (uint16_t)(ep & 0xFFFFu);
  }
  if (machine_id != NULL) {
    *machine_id = id;
  }
}

void dcs_publish_pstop_machine(
  int slot,
  uint32_t sent,
  uint32_t replies,
  uint32_t send_fail,
  uint32_t rebonds,
  uint32_t hb_ms,
  uint64_t last_reply_ms,
  uint32_t rtt_ms,
  uint8_t last_msg,
  uint8_t sess_state)
{
  if ((slot < 0) || (slot >= DCS_PSTOP_MAX_MACHINES)) {
    return;
  }
  atomic_store(&g_dcs_pstop_m_sent[slot], sent);
  atomic_store(&g_dcs_pstop_m_replies[slot], replies);
  atomic_store(&g_dcs_pstop_m_send_fail[slot], send_fail);
  atomic_store(&g_dcs_pstop_m_rebonds[slot], rebonds);
  atomic_store(&g_dcs_pstop_m_last_reply_ms[slot], last_reply_ms);
  atomic_store(&g_dcs_pstop_m_rtt_ms[slot], rtt_ms);
  atomic_store(&g_dcs_pstop_m_hb_ms[slot], hb_ms);
  atomic_store(&g_dcs_pstop_m_last_msg[slot], last_msg);
  atomic_store(&g_dcs_pstop_m_state[slot], sess_state);
}

void dcs_get_initial_pstop_peer(uint32_t * peer_ip, uint16_t * peer_port)
{
  if (peer_ip != NULL) {
    *peer_ip = atomic_load(&g_dcs_pstop_peer_ip);
  }
  if (peer_port != NULL) {
    *peer_port = (uint16_t)atomic_load(&g_dcs_pstop_peer_port);
  }
}

uint32_t dcs_get_vpn_ip(void)
{
  return (g_dcs.ml_handle != NULL) ? microlink_get_vpn_ip(g_dcs.ml_handle) : 0u;
}

void dcs_notify_priority_health(bool healthy)
{
  if (g_dcs.ml_handle != NULL) {
    microlink_notify_priority_health(g_dcs.ml_handle, healthy);
  }
}

void dcs_notify_peer_health(uint32_t vpn_ip, bool healthy)
{
  if (g_dcs.ml_handle != NULL) {
    microlink_notify_peer_health(g_dcs.ml_handle, vpn_ip, healthy);
  }
}

void dcs_untrack_peer_health(uint32_t vpn_ip)
{
  if (g_dcs.ml_handle != NULL) {
    microlink_untrack_peer_health(g_dcs.ml_handle, vpn_ip);
  }
}
