polymathrobotics/protective-stop/components/microlink/src/microlink.c

// SPDX-FileCopyrightText: 2026 Polymath Robotics
// SPDX-License-Identifier: Apache-2.0

/**
 * @file microlink.c
 * @brief MicroLink v2 - Public API and Task Orchestration
 *
 * Creates all FreeRTOS tasks, queues, and event groups.
 * Provides the public API that the application calls.
 */

#include <fcntl.h>
#include <stdio.h>
#include <string.h>

#include "cJSON.h"
#include "esp_heap_caps.h"
#include "esp_log.h"
#include "esp_mac.h"
#include "esp_random.h"
#include "esp_timer.h"
#include "esp_wifi.h"
#include "lwip/sockets.h"
#include "lwip/sys.h"
#include "microlink_internal.h"
#include "nvs.h"
#include "nvs_flash.h"
#include "wireguardif.h" /* peer path-recovery diagnostics in microlink_get_peer_info */

static const char * TAG = "microlink";

/* NVS keys */
#define NVS_NAMESPACE "microlink"
#define NVS_KEY_MACHINE_PRI "machine_pri"
#define NVS_KEY_MACHINE_PUB "machine_pub"
#define NVS_KEY_WG_PRI "wg_private"
#define NVS_KEY_WG_PUB "wg_public"
#define NVS_KEY_DISCO_PRI "disco_pri"
#define NVS_KEY_DISCO_PUB "disco_pub"
#define NVS_KEY_VPN_IP "vpn_ip"

/* X25519 from x25519.h */
#include "x25519.h"

/* ============================================================================
 * Key Management (loaded once at init, read-only after)
 * ========================================================================== */

static void generate_keypair(uint8_t * private_key, uint8_t * public_key)
{
  esp_fill_random(private_key, 32);
  private_key[0] &= 248;
  private_key[31] &= 127;
  private_key[31] |= 64;
  x25519_base(public_key, private_key, 1);
}

static esp_err_t load_or_generate_keys(microlink_t * ml)
{
  nvs_handle_t nvs;
  esp_err_t err = nvs_open(NVS_NAMESPACE, NVS_READWRITE, &nvs);
  if (err != ESP_OK) {
    ESP_LOGW(TAG, "NVS open failed (%d), generating ephemeral keys", err);
    generate_keypair(ml->machine_private_key, ml->machine_public_key);
    generate_keypair(ml->wg_private_key, ml->wg_public_key);
    generate_keypair(ml->disco_private_key, ml->disco_public_key);
    return ESP_OK;
  }

  size_t key_len = 32;
  bool need_save = false;

  /* Machine key */
  if (nvs_get_blob(nvs, NVS_KEY_MACHINE_PRI, ml->machine_private_key, &key_len) != ESP_OK) {
    generate_keypair(ml->machine_private_key, ml->machine_public_key);
    need_save = true;
    ESP_LOGI(TAG, "Generated new machine key");
  } else {
    key_len = 32;
    nvs_get_blob(nvs, NVS_KEY_MACHINE_PUB, ml->machine_public_key, &key_len);
  }

  /* WireGuard key */
  key_len = 32;
  if (nvs_get_blob(nvs, NVS_KEY_WG_PRI, ml->wg_private_key, &key_len) != ESP_OK) {
    generate_keypair(ml->wg_private_key, ml->wg_public_key);
    need_save = true;
    ESP_LOGI(TAG, "Generated new WireGuard key");
  } else {
    key_len = 32;
    nvs_get_blob(nvs, NVS_KEY_WG_PUB, ml->wg_public_key, &key_len);
  }

  /* DISCO key */
  key_len = 32;
  if (nvs_get_blob(nvs, NVS_KEY_DISCO_PRI, ml->disco_private_key, &key_len) != ESP_OK) {
    generate_keypair(ml->disco_private_key, ml->disco_public_key);
    need_save = true;
    ESP_LOGI(TAG, "Generated new DISCO key");
  } else {
    key_len = 32;
    nvs_get_blob(nvs, NVS_KEY_DISCO_PUB, ml->disco_public_key, &key_len);
  }

  /* Last-known VPN IP (best effort). Persisted on every registration so a
     * reboot can bring the WG interface up + preseed cached peers BEFORE (or
     * without) coordination connectivity — the cold-bond far-side recovery
     * (2026-08-08 bench: rebooted machine ignored operator handshakes for
     * 27 min while its netmap never re-arrived). A stale value is harmless:
     * registration overwrites it and ml_wg_mgr re-syncs the netif address. */
  {
    uint32_t stored_ip = 0;
    if (nvs_get_u32(nvs, NVS_KEY_VPN_IP, &stored_ip) == ESP_OK && stored_ip != 0) {
      ml->vpn_ip = stored_ip;
      char ip_str[16];
      microlink_ip_to_str(stored_ip, ip_str);
      ESP_LOGI(TAG, "VPN IP restored from NVS: %s (pre-registration)", ip_str);
    }
  }

  if (need_save) {
    nvs_set_blob(nvs, NVS_KEY_MACHINE_PRI, ml->machine_private_key, 32);
    nvs_set_blob(nvs, NVS_KEY_MACHINE_PUB, ml->machine_public_key, 32);
    nvs_set_blob(nvs, NVS_KEY_WG_PRI, ml->wg_private_key, 32);
    nvs_set_blob(nvs, NVS_KEY_WG_PUB, ml->wg_public_key, 32);
    nvs_set_blob(nvs, NVS_KEY_DISCO_PRI, ml->disco_private_key, 32);
    nvs_set_blob(nvs, NVS_KEY_DISCO_PUB, ml->disco_public_key, 32);
    nvs_commit(nvs);
    ESP_LOGI(TAG, "Keys saved to NVS");
  } else {
    ESP_LOGI(TAG, "Keys loaded from NVS");
  }

  nvs_close(nvs);
  return ESP_OK;
}

/* Persist the current VPN IP (see the load note in load_or_generate_keys).
 * Called from the coord task whenever registration/map assigns the IP —
 * never from the safety tick. Write-on-change only: re-registrations with
 * the same address (the common case) cost zero flash wear. */
static bool s_vpn_ip_forgotten; /* until reboot: re-registers must not re-persist the old IP */

void ml_ident_persist_vpn_ip(microlink_t * ml)
{
  if (!ml || ml->vpn_ip == 0 || s_vpn_ip_forgotten) {
    return;
  }
  nvs_handle_t nvs;
  if (nvs_open(NVS_NAMESPACE, NVS_READWRITE, &nvs) != ESP_OK) {
    return;
  }
  uint32_t stored_ip = 0;
  (void)nvs_get_u32(nvs, NVS_KEY_VPN_IP, &stored_ip);
  if (stored_ip != ml->vpn_ip) {
    if (nvs_set_u32(nvs, NVS_KEY_VPN_IP, ml->vpn_ip) == ESP_OK) {
      nvs_commit(nvs);
      ESP_LOGI(TAG, "VPN IP persisted to NVS");
    }
  }
  nvs_close(nvs);
}

bool ml_ident_forget_vpn_ip(void)
{
  s_vpn_ip_forgotten = true;
  nvs_handle_t nvs;
  if (nvs_open(NVS_NAMESPACE, NVS_READWRITE, &nvs) != ESP_OK) {
    return false;
  }
  esp_err_t err = nvs_erase_key(nvs, NVS_KEY_VPN_IP);
  if (err == ESP_OK) {
    err = nvs_commit(nvs);
  } else if (err == ESP_ERR_NVS_NOT_FOUND) {
    err = ESP_OK;
  }
  nvs_close(nvs);
  if (err == ESP_OK) {
    ESP_LOGI(TAG, "VPN IP forgotten: next boot enrolls with the saved auth key");
  }
  return err == ESP_OK;
}

/* ============================================================================
 * cJSON PSRAM Hooks
 * ========================================================================== */

static void * cjson_psram_malloc(size_t size)
{
  return ml_psram_malloc(size);
}

/* ============================================================================
 * Factory Reset
 * ========================================================================== */

esp_err_t microlink_factory_reset(void)
{
  esp_err_t err;

  /* Erase key namespace */
  nvs_handle_t nvs;
  err = nvs_open(NVS_NAMESPACE, NVS_READWRITE, &nvs);
  if (err == ESP_OK) {
    nvs_erase_all(nvs);
    nvs_commit(nvs);
    nvs_close(nvs);
    ESP_LOGI(TAG, "Factory reset: keys erased");
  }

  /* Erase cached peers */
  ml_peer_nvs_init();
  ml_peer_nvs_clear();
  ml_peer_nvs_deinit();

  ESP_LOGI(TAG, "Factory reset complete");
  return ESP_OK;
}

/* ============================================================================
 * Public API
 * ========================================================================== */

microlink_t * microlink_init(const microlink_config_t * config)
{
  if (!config || !config->auth_key) {
    ESP_LOGE(TAG, "Invalid config: auth_key required");
    return NULL;
  }

  /* Route cJSON to PSRAM */
  cJSON_Hooks hooks = {.malloc_fn = cjson_psram_malloc, .free_fn = free};
  cJSON_InitHooks(&hooks);

  /* Allocate context from PSRAM */
  microlink_t * ml = ml_psram_calloc(1, sizeof(microlink_t));
  if (!ml) {
    ESP_LOGE(TAG, "Failed to allocate context");
    return NULL;
  }

  /* Copy config */
  ml->config = *config;
  if (ml->config.max_peers == 0) ml->config.max_peers = ML_MAX_PEERS;
  if (ml->config.max_peers > ML_MAX_PEERS) ml->config.max_peers = ML_MAX_PEERS;
  ml->config.enable_derp = true; /* Always need DERP for relay */

  ml->state = ML_STATE_IDLE;
  ml->priority_link_healthy = true; /* until the app says otherwise */
  ml->fleet_link_healthy = true; /* until a check-in fails */
  ml->coord_sock = -1;
  ml->disco_sock4 = -1;
  ml->disco_sock6 = -1;
  ml->stun_sock = -1;
  ml->stun_sock6 = -1;
  /* Init every DERP pool slot: sockfd=-1, region_id=0 (free), tls_inited=false
   * (ml is calloc'd so the rest is already zero). Slot 0 is the home conn. */
  for (int i = 0; i < ML_DERP_MAX_CONNS; i++) {
    ml->derp[i].sockfd = -1;
  }

  /* Resolve timing (0 = use defaults from #defines) */
  ml->t_disco_heartbeat_ms = ml->config.disco_heartbeat_ms ? ml->config.disco_heartbeat_ms : ML_DISCO_HEARTBEAT_MS;
  ml->t_stun_interval_ms = ml->config.stun_interval_ms ? ml->config.stun_interval_ms : ML_STUN_RESTUN_INTERVAL_MS;
  ml->t_ctrl_watchdog_ms = ml->config.ctrl_watchdog_ms ? ml->config.ctrl_watchdog_ms : ML_CTRL_WATCHDOG_MS;

  /* Apply Kconfig priority peer if set and app didn't provide one */
  if (ml->config.priority_peer_ip == 0 && strlen(CONFIG_ML_PRIORITY_PEER_IP) > 0) {
    ml->config.priority_peer_ip = microlink_parse_ip(CONFIG_ML_PRIORITY_PEER_IP);
    if (ml->config.priority_peer_ip) {
      ml_peer_nvs_set_protected(ml->config.priority_peer_ip);
      ESP_LOGI(TAG, "Priority peer from Kconfig: %s", CONFIG_ML_PRIORITY_PEER_IP);
    }
  }

  /* Load or generate persistent keys */
  if (load_or_generate_keys(ml) != ESP_OK) {
    free(ml);
    return NULL;
  }

  /* Initialize peer NVS cache */
  ml_peer_nvs_init();

  /* Initialize HTTP config server (loads NVS peer allowlist + settings) */
  ml->config_httpd = ml_config_httpd_init();

  /* Override config with NVS-saved settings (web UI save → restart flow).
     * NVS settings take priority over Kconfig defaults.  Strings are copied
     * into ml->nvs_* buffers so the const char* pointers remain valid. */
  if (ml->config_httpd) {
    const char * nvs_auth = ml_config_get_auth_key(ml->config_httpd);
    if (nvs_auth) {
      strlcpy(ml->nvs_auth_key, nvs_auth, sizeof(ml->nvs_auth_key));
      ml->config.auth_key = ml->nvs_auth_key;
      ESP_LOGI(TAG, "Auth key overridden from NVS (len=%d)", (int)strlen(nvs_auth));
    }
    /* Device name: full name takes priority, then prefix+MAC, then Kconfig */
    const char * nvs_full_name = ml_config_get_device_name_full(ml->config_httpd);
    if (nvs_full_name) {
      /* Full custom hostname (e.g. "pstop-tailscale") */
      strlcpy(ml->nvs_device_name, nvs_full_name, sizeof(ml->nvs_device_name));
      ml->config.device_name = ml->nvs_device_name;
      ESP_LOGI(TAG, "Device name from NVS (full): %s", ml->nvs_device_name);
    } else {
      const char * nvs_prefix = ml_config_get_device_prefix(ml->config_httpd);
      if (nvs_prefix) {
        /* Device name = prefix + MAC suffix (e.g. "pstop-a1b2c3") */
        uint8_t mac[6];
        esp_read_mac(mac, ESP_MAC_WIFI_STA);
        snprintf(
          ml->nvs_device_name,
          sizeof(ml->nvs_device_name),
          "%s-%02x%02x%02x%02x%02x%02x",
          nvs_prefix,
          mac[0],
          mac[1],
          mac[2],
          mac[3],
          mac[4],
          mac[5]);
        ml->config.device_name = ml->nvs_device_name;
        ESP_LOGI(TAG, "Device name from NVS (prefix): %s", ml->nvs_device_name);
      }
    }

    /* v2 overrides */
    uint8_t nvs_max = ml_config_get_max_peers(ml->config_httpd);
    if (nvs_max > 0 && nvs_max <= ML_MAX_PEERS) {
      ml->config.max_peers = nvs_max;
      ESP_LOGI(TAG, "Max peers overridden from NVS: %d", nvs_max);
    }
    uint16_t nvs_hb = ml_config_get_disco_heartbeat_ms(ml->config_httpd);
    if (nvs_hb > 0 && nvs_hb <= 60000) {
      ml->config.disco_heartbeat_ms = nvs_hb;
      ml->t_disco_heartbeat_ms = nvs_hb;
      ESP_LOGI(TAG, "DISCO heartbeat overridden from NVS: %dms", nvs_hb);
    }
    uint32_t nvs_pip = ml_config_get_priority_peer_ip(ml->config_httpd);
    if (nvs_pip > 0) {
      ml->config.priority_peer_ip = nvs_pip;
      ml_peer_nvs_set_protected(nvs_pip);
      char pip_str[16];
      microlink_ip_to_str(nvs_pip, pip_str);
      ESP_LOGI(TAG, "Priority peer overridden from NVS: %s", pip_str);
    }
    const char * nvs_ctrl = ml_config_get_ctrl_host(ml->config_httpd);
    if (nvs_ctrl) {
      strlcpy(ml->ctrl_host, nvs_ctrl, sizeof(ml->ctrl_host));
      ESP_LOGI(TAG, "Control plane overridden from NVS: %s", ml->ctrl_host);
    }
    ml->debug_flags = ml_config_get_debug_flags(ml->config_httpd);
    if (ml->debug_flags) {
      ESP_LOGI(TAG, "Debug flags from NVS: 0x%02x", ml->debug_flags);
    }
    uint16_t nvs_region = ml_config_get_derp_region(ml->config_httpd);
    if (nvs_region > 0 && nvs_region <= 4095) {
      ml->derp_region_override = nvs_region;
      ESP_LOGI(TAG, "DERP home region pinned from NVS: %u", (unsigned)nvs_region);
    }
  }

  /* Create event group */
  ml->events = xEventGroupCreate();
  if (!ml->events) {
    ESP_LOGE(TAG, "Failed to create event group");
    free(ml);
    return NULL;
  }

  /* Create queues */
  ml->derp_tx_queue = xQueueCreate(ML_DERP_TX_QUEUE_DEPTH, sizeof(ml_derp_tx_item_t));
  ml->derp_tx_prio_queue = xQueueCreate(ML_DERP_TX_PRIO_DEPTH, sizeof(ml_derp_tx_item_t));
  ml->disco_rx_queue = xQueueCreate(ML_DISCO_RX_QUEUE_DEPTH, sizeof(ml_rx_packet_t));
  ml->wg_rx_queue = xQueueCreate(ML_WG_RX_QUEUE_DEPTH, sizeof(ml_rx_packet_t));
  ml->stun_rx_queue = xQueueCreate(ML_STUN_RX_QUEUE_DEPTH, sizeof(ml_rx_packet_t));
  ml->coord_cmd_queue = xQueueCreate(ML_COORD_CMD_QUEUE_DEPTH, sizeof(ml_coord_cmd_t));
  ml->peer_update_queue = xQueueCreate(ML_PEER_UPDATE_QUEUE_DEPTH, sizeof(ml_peer_update_t *));

  if (
    !ml->derp_tx_queue || !ml->derp_tx_prio_queue || !ml->disco_rx_queue || !ml->wg_rx_queue || !ml->stun_rx_queue ||
    !ml->coord_cmd_queue || !ml->peer_update_queue)
  {
    ESP_LOGE(TAG, "Failed to create queues");
    microlink_destroy(ml);
    return NULL;
  }

  ESP_LOGI(TAG, "MicroLink v2 initialized (max_peers=%d)", ml->config.max_peers);
  return ml;
}

esp_err_t microlink_start(microlink_t * ml)
{
  if (!ml) return ESP_ERR_INVALID_ARG;
  if (ml->state != ML_STATE_IDLE) {
    ESP_LOGW(TAG, "Already started (state=%d)", ml->state);
    return ESP_ERR_INVALID_STATE;
  }

  ml->state = ML_STATE_WIFI_WAIT;

  /* Set WiFi TX power if configured */
  if (ml->config.wifi_tx_power_dbm > 0) {
    int8_t power_quarter_dbm = ml->config.wifi_tx_power_dbm * 4;
    esp_wifi_set_max_tx_power(power_quarter_dbm);
    ESP_LOGI(TAG, "WiFi TX power set to %d dBm", ml->config.wifi_tx_power_dbm);
  }

#ifdef CONFIG_ML_ZERO_COPY_WG
  /* Zero-copy mode: raw lwIP PCB replaces BSD socket for DISCO/WG UDP.
     * WG packets go directly to wireguardif_network_rx() from tcpip_thread.
     * DISCO packets go to SPSC ring buffer, STUN to existing queue. */
  if (ml_zerocopy_init(ml) != ESP_OK) {
    ESP_LOGE(TAG, "Zero-copy init failed, falling back to BSD socket");
    goto bsd_socket_fallback;
  }
  ESP_LOGI(TAG, "Zero-copy WG mode active (high-throughput)");
  goto skip_bsd_socket;

bsd_socket_fallback:
#endif
  /* Create DISCO/magicsock UDP socket (port 51820 = WireGuard standard)
     * This is the single socket for ALL direct UDP traffic: DISCO pings/pongs,
     * CallMeMaybe probes, and WireGuard encrypted data.
     * Matches v1 microlink_disco_init() and tailscale's pconn4. */
  ml->disco_sock4 = ml_socket(AF_INET, SOCK_DGRAM, IPPROTO_UDP);
  if (ml->disco_sock4 >= 0) {
    struct sockaddr_in bind_addr = {
      .sin_family = AF_INET,
      .sin_port = htons(51820),
      .sin_addr.s_addr = INADDR_ANY,
    };
    if (ml_bind(ml->disco_sock4, (struct sockaddr *)&bind_addr, sizeof(bind_addr)) < 0) {
      ESP_LOGW(TAG, "Failed to bind port 51820 (errno=%d), trying ephemeral", errno);
      bind_addr.sin_port = 0;
      ml_bind(ml->disco_sock4, (struct sockaddr *)&bind_addr, sizeof(bind_addr));
    }

    /* Mark packets as DSCP 46 (Expedited Forwarding) → WMM AC_VO.
         * WiFi APs with WMM use shorter contention windows for voice-priority
         * traffic, reducing jitter on WireGuard/DISCO UDP packets. */
    int tos = 0xB8; /* DSCP 46 = EF, TOS byte = 46 << 2 = 184 */
    setsockopt(ml->disco_sock4, IPPROTO_IP, IP_TOS, &tos, sizeof(tos));

    /* Set non-blocking for select() in net_io */
    int flags = ml_fcntl(ml->disco_sock4, F_GETFL, 0);
    ml_fcntl(ml->disco_sock4, F_SETFL, flags | O_NONBLOCK);

    /* Record the actual bound port (getsockname not wrapped — AT sockets use stored port) */
    struct sockaddr_in local_addr;
    socklen_t addr_len = sizeof(local_addr);
    getsockname(ml->disco_sock4, (struct sockaddr *)&local_addr, &addr_len);
    ml->disco_local_port = ntohs(local_addr.sin_port);
    ESP_LOGI(TAG, "DISCO/magicsock UDP socket bound to port %d", ml->disco_local_port);
  } else {
    ESP_LOGE(TAG, "Failed to create DISCO socket: errno=%d", errno);
  }
#ifdef CONFIG_ML_ZERO_COPY_WG
skip_bsd_socket:;
#endif

  /* Create tasks */
  BaseType_t ret;

  ret = xTaskCreatePinnedToCore(
    ml_net_io_task, "ml_net_io", ML_TASK_NET_IO_STACK, ml, ML_TASK_NET_IO_PRIO, &ml->net_io_task, ML_TASK_NET_IO_CORE);
  if (ret != pdPASS) {
    ESP_LOGE(TAG, "Failed to create net_io task");
    return ESP_FAIL;
  }

  ret = xTaskCreatePinnedToCore(
    ml_derp_tx_task,
    "ml_derp_tx",
    ML_TASK_DERP_TX_STACK,
    ml,
    ML_TASK_DERP_TX_PRIO,
    &ml->derp_tx_task,
    ML_TASK_DERP_TX_CORE);
  if (ret != pdPASS) {
    ESP_LOGE(TAG, "Failed to create derp_tx task");
    return ESP_FAIL;
  }

  ret = xTaskCreatePinnedToCore(
    ml_coord_task, "ml_coord", ML_TASK_COORD_STACK, ml, ML_TASK_COORD_PRIO, &ml->coord_task, ML_TASK_COORD_CORE);
  if (ret != pdPASS) {
    ESP_LOGE(TAG, "Failed to create coord task");
    return ESP_FAIL;
  }

  ret = xTaskCreatePinnedToCore(
    ml_wg_mgr_task, "ml_wg_mgr", ML_TASK_WG_MGR_STACK, ml, ML_TASK_WG_MGR_PRIO, &ml->wg_mgr_task, ML_TASK_WG_MGR_CORE);
  if (ret != pdPASS) {
    ESP_LOGE(TAG, "Failed to create wg_mgr task");
    return ESP_FAIL;
  }

  /* WiFi is expected to be connected before microlink_start() is called.
     * Signal the event so coord/wg_mgr tasks proceed immediately. */
  xEventGroupSetBits(ml->events, ML_EVT_WIFI_CONNECTED);

  /* Signal coord task to start connecting */
  ml_coord_cmd_t cmd = ML_CMD_CONNECT;
  xQueueSend(ml->coord_cmd_queue, &cmd, 0);

  /* Start HTTP config server (binds port 80, serves config page + REST API).
     * Skip if ml_app already registered routes on an external httpd. */
  if (ml->config_httpd) {
    if (ml_config_httpd_is_started(ml->config_httpd)) {
      /* External httpd (ml_app) — just set the backpointer */
      ml_config_httpd_set_ml(ml->config_httpd, ml);
    } else {
      ml_config_httpd_start(ml->config_httpd, ml);
    }
  }

  ESP_LOGI(TAG, "All tasks started");
  return ESP_OK;
}

esp_err_t microlink_request_announce(microlink_t * ml)
{
  if (!ml || !ml->coord_cmd_queue) {
    return ESP_ERR_INVALID_STATE;
  }
  /* Non-blocking (callable from the app's safety loop): the coord task sends
     * the Stream=false endpoint-update MapRequest on its own H2 connection.
     * Queue full = an announce is already pending; that one suffices. */
  ml_coord_cmd_t cmd = ML_CMD_UPDATE_ENDPOINTS;
  return (xQueueSend(ml->coord_cmd_queue, &cmd, 0) == pdTRUE) ? ESP_OK : ESP_ERR_NO_MEM;
}

esp_err_t microlink_rebind(microlink_t * ml)
{
  if (!ml) return ESP_ERR_INVALID_ARG;
  if (ml->state == ML_STATE_IDLE) return ESP_ERR_INVALID_STATE;

  ESP_LOGI(TAG, "=== Rebinding to new network interface ===");

  /* Step 1: Invalidate socket FDs FIRST, then delay to let net_io_task's
     * select() cycle complete (50ms timeout). Only THEN close the old FDs.
     * Closing a socket while another thread has it in select() deadlocks
     * on lwIP's global socket lock. */
  int old_disco = ml->disco_sock4;
  int old_stun = ml->stun_sock;
  int old_stun6 = ml->stun_sock6;

  /* Invalidate — net_io_task will skip these on next iteration */
  ml->disco_sock4 = -1;
  ml->stun_sock = -1;
  ml->stun_sock6 = -1;

  /* Wait for net_io_task select() to cycle out (50ms timeout + margin) */
  vTaskDelay(pdMS_TO_TICKS(100));

  /* Now safe to close the old FDs */
  if (old_disco >= 0) ml_close_sock(old_disco);
  if (old_stun >= 0) ml_close_sock(old_stun);
  if (old_stun6 >= 0) ml_close_sock(old_stun6);
  ESP_LOGI(TAG, "Rebind: closed DISCO + STUN sockets");

  /* Step 2: Signal coord to reconnect. ML_CMD_FORCE_RECONNECT closes
     * the coord socket, resets Noise state, and re-enters the
     * STUN → DNS → TCP → Noise → Register → MapRequest flow.
     * Peers and WG state are preserved. */
  xEventGroupClearBits(ml->events, ML_EVT_COORD_REGISTERED);
  ml_coord_cmd_t cmd = ML_CMD_FORCE_RECONNECT;
  xQueueSend(ml->coord_cmd_queue, &cmd, pdMS_TO_TICKS(100));

  /* Step 3: Signal DERP to reconnect. ML_EVT_DERP_RECONNECT triggers
     * derp_tx_task to close TLS, then reconnect with full handshake.
     * Pending TX packets are drained but WG state is preserved. */
  xEventGroupClearBits(ml->events, ML_EVT_DERP_CONNECTED);
  ml_derp_note_reconnect_cause(3); /* cause 3 = interface rebind */
  xEventGroupSetBits(ml->events, ML_EVT_DERP_RECONNECT);
  ESP_LOGI(TAG, "Rebind: signaled coord + DERP to reconnect");

  /* Step 4: Brief delay for coord/DERP to process reconnect signals */
  vTaskDelay(pdMS_TO_TICKS(200));

  /* Step 5: Recreate DISCO UDP socket on the new interface */
#ifdef CONFIG_ML_ZERO_COPY_WG
  ml_zerocopy_deinit(ml);
  if (ml_zerocopy_init(ml) == ESP_OK) {
    ESP_LOGI(TAG, "Rebind: zero-copy DISCO PCB recreated");
    goto rebind_wg_update;
  }
  ESP_LOGW(TAG, "Rebind: zero-copy init failed, using BSD socket fallback");
#endif
  ml->disco_sock4 = ml_socket(AF_INET, SOCK_DGRAM, IPPROTO_UDP);
  if (ml->disco_sock4 >= 0) {
    struct sockaddr_in bind_addr = {
      .sin_family = AF_INET,
      .sin_port = htons(51820),
      .sin_addr.s_addr = INADDR_ANY,
    };
    if (ml_bind(ml->disco_sock4, (struct sockaddr *)&bind_addr, sizeof(bind_addr)) < 0) {
      bind_addr.sin_port = 0;
      ml_bind(ml->disco_sock4, (struct sockaddr *)&bind_addr, sizeof(bind_addr));
    }
    int tos = 0xB8;
    setsockopt(ml->disco_sock4, IPPROTO_IP, IP_TOS, &tos, sizeof(tos));
    int flags = ml_fcntl(ml->disco_sock4, F_GETFL, 0);
    ml_fcntl(ml->disco_sock4, F_SETFL, flags | O_NONBLOCK);

    struct sockaddr_in local_addr;
    socklen_t addr_len = sizeof(local_addr);
    getsockname(ml->disco_sock4, (struct sockaddr *)&local_addr, &addr_len);
    ml->disco_local_port = ntohs(local_addr.sin_port);
    ESP_LOGI(TAG, "Rebind: DISCO socket rebound to port %d", ml->disco_local_port);
  } else {
    ESP_LOGE(TAG, "Rebind: failed to create DISCO socket: errno=%d", errno);
  }

#ifdef CONFIG_ML_ZERO_COPY_WG
rebind_wg_update:
#endif
  /* Step 6: Update WG output mode for new transport */
  ml_wg_mgr_update_transport(ml);

  ESP_LOGI(TAG, "=== Rebind complete — waiting for coord+DERP reconnect ===");
  return ESP_OK;
}

esp_err_t microlink_stop(microlink_t * ml)
{
  if (!ml) return ESP_ERR_INVALID_ARG;

  ESP_LOGI(TAG, "Stopping...");
  xEventGroupSetBits(ml->events, ML_EVT_SHUTDOWN_REQUEST);

  /* Wait for tasks to exit (they check ML_EVT_SHUTDOWN_REQUEST).
     * Tasks call vTaskDelete(NULL) to self-delete, so we must NOT call
     * vTaskDelete() on them again — that causes a crash in uxListRemove
     * because the task's list node is already invalid. Just wait and
     * NULL the handles. */
  vTaskDelay(pdMS_TO_TICKS(3000));

  ml->net_io_task = NULL;
  ml->derp_tx_task = NULL;
  ml->coord_task = NULL;
  ml->wg_mgr_task = NULL;

  /* Stop HTTP config server */
  if (ml->config_httpd) {
    ml_config_httpd_stop(ml->config_httpd);
  }

  /* Clean up zero-copy PCB if active */
#ifdef CONFIG_ML_ZERO_COPY_WG
  ml_zerocopy_deinit(ml);
#endif

  /* Close sockets */
  if (ml->disco_sock4 >= 0) {
    ml_close_sock(ml->disco_sock4);
    ml->disco_sock4 = -1;
  }
  if (ml->stun_sock >= 0) {
    ml_close_sock(ml->stun_sock);
    ml->stun_sock = -1;
  }
  if (ml->stun_sock6 >= 0) {
    ml_close_sock(ml->stun_sock6);
    ml->stun_sock6 = -1;
  }

  ml->state = ML_STATE_IDLE;
  ESP_LOGI(TAG, "Stopped");
  return ESP_OK;
}

void microlink_destroy(microlink_t * ml)
{
  if (!ml) return;

  microlink_stop(ml);

  /* Deinitialize peer NVS */
  ml_peer_nvs_deinit();

  /* Deinitialize HTTP config server */
  if (ml->config_httpd) {
    ml_config_httpd_deinit(ml->config_httpd);
    ml->config_httpd = NULL;
  }

  /* Delete queues */
  if (ml->derp_tx_queue) vQueueDelete(ml->derp_tx_queue);
  if (ml->derp_tx_prio_queue) vQueueDelete(ml->derp_tx_prio_queue);
  if (ml->disco_rx_queue) vQueueDelete(ml->disco_rx_queue);
  if (ml->wg_rx_queue) vQueueDelete(ml->wg_rx_queue);
  if (ml->stun_rx_queue) vQueueDelete(ml->stun_rx_queue);
  if (ml->coord_cmd_queue) vQueueDelete(ml->coord_cmd_queue);
  if (ml->peer_update_queue) vQueueDelete(ml->peer_update_queue);

  /* Delete event group */
  if (ml->events) vEventGroupDelete(ml->events);

  /* Clear keys from memory */
  memset(ml->machine_private_key, 0, 32);
  memset(ml->wg_private_key, 0, 32);
  memset(ml->disco_private_key, 0, 32);

  free(ml);
  ESP_LOGI(TAG, "Destroyed");
}

/* ============================================================================
 * State Queries
 * ========================================================================== */

microlink_state_t microlink_get_state(const microlink_t * ml)
{
  return ml ? ml->state : ML_STATE_IDLE;
}

uint32_t microlink_get_connect_count(const microlink_t * ml)
{
  return ml ? ml->connect_count : 0U;
}

bool microlink_is_connected(const microlink_t * ml)
{
  return ml && ml->state == ML_STATE_CONNECTED;
}

uint32_t microlink_get_vpn_ip(const microlink_t * ml)
{
  return ml ? ml->vpn_ip : 0;
}

/* Our public egress IP as seen from the internet (learned via STUN). 0 until
 * STUN completes. Behind NAT this is the site's egress point, useful for rough
 * (city-level) geolocation on the management side. */
uint32_t microlink_get_public_ip(const microlink_t * ml)
{
  return ml ? ml->stun_public_ip : 0;
}

/* The DERP region our single relay connection is homed on (0 = not yet set).
 * Returns the EFFECTIVE home: the runtime lock (derp_region_override) wins,
 * else the learned/rehomed region — i.e. the region slot-0 connect and the
 * PreferredDERP advert actually use. A coarse locality hint (nearest Tailscale
 * datacenter metro). */
uint16_t microlink_get_derp_region(const microlink_t * ml)
{
  return ml ? ml_effective_home_region(ml) : 0;
}

/* The configured DERP-region LOCK (0 = auto, else the pinned region). This is
 * the persisted override, NOT necessarily the region in use — the two differ
 * only transiently while a fresh lock re-homes. Exposed so /state.json can show
 * AUTO vs LOCKED-to-N. Locking is the guard against a repeat of the region-9
 * (dfw) misroute, where the chip silently drifted region and only a pin
 * restored the priority path. */
uint16_t microlink_get_derp_region_locked(const microlink_t * ml)
{
  return ml ? ml->derp_region_override : 0;
}

/* ============================================================================
 * DERP region auto-negotiation public surface (design §4.2/§6, Q2 surfacing).
 * The negotiation itself lives in ml_wg_mgr.c (decision, damping) and
 * ml_derp.c (MBB execution) — these are just the app-facing hooks.
 * ========================================================================== */

void microlink_set_primary_machine_cb(microlink_t * ml, microlink_primary_machine_cb_t cb, void * ctx)
{
  if (!ml) return;
  /* ctx before cb: a cross-task reader that observes the new cb pointer must
   * also observe its ctx (word-sized volatile-ish writes on Xtensa). */
  ml->primary_cb_ctx = ctx;
  ml->primary_cb = cb;
}

void microlink_offer_region_advice(microlink_t * ml, uint16_t region, uint32_t epoch, uint32_t ttl_s)
{
  if (!ml || region == 0 || region > 4095 || ttl_s == 0) {
    return;
  }
  /* I3: a stale/replayed advice (fleet DB reload, buggy backend re-serving an
   * old decision) must be inert — only a strictly increasing epoch is stored. */
  if (ml->advice_epoch != 0 && epoch <= ml->advice_epoch) {
    return;
  }
  if (ttl_s > 86400u) {
    ttl_s = 86400u; /* cap: advice must re-earn its place at least daily */
  }
  uint32_t now_s = (uint32_t)(ml_get_time_ms() / 1000u);
  /* Order: region + expiry land before the epoch, so a consumer keying on the
   * new epoch never reads the old region/expiry pair. */
  ml->advice_region = region;
  ml->advice_expires_s = now_s + ttl_s;
  ml->advice_epoch = epoch;
  ESP_LOGI(
    TAG,
    "Fleet region advice stored: region=%u epoch=%lu ttl=%lus (advisory; gated by lock/machines/damping/proving)",
    (unsigned)region,
    (unsigned long)epoch,
    (unsigned long)ttl_s);
}

void microlink_get_region_autoneg(microlink_t * ml, microlink_region_autoneg_t * out)
{
  if (!out) return;
  memset(out, 0, sizeof(*out));
  if (!ml) return;
  out->source = (ml->derp_region_override != 0) ? (uint8_t)MICROLINK_REGION_SRC_LOCKED : (uint8_t)ml->derp_region_src;
  out->auto_applied_region = ml->derp_region_auto_applied;
  out->auto_apply_count = ml->derp_region_auto_applies;
  out->last_auto_apply_s = ml->derp_region_auto_apply_s;
  out->mbb_state = ml->mbb_state;
  out->mbb_pending_region = ml->mbb_target_region;
  uint32_t md[4] = {0};
  ml_derp_get_mbb_diag(md);
  out->mbb_commits = md[0];
  out->mbb_rollbacks = md[1];
  out->mbb_proofs_ok = md[2];
  out->mbb_proofs_failed = md[3];
  uint32_t nd[3] = {0};
  ml_wg_get_neg_diag(nd);
  out->damping_suppressed = nd[0];
  out->cooldown_trips = nd[1];
  out->switches_1h = nd[2];
}

const char * microlink_region_source_str(uint8_t source)
{
  switch (source) {
    case MICROLINK_REGION_SRC_LOCKED:
      return "locked";
    case MICROLINK_REGION_SRC_AUTO_PRIMARY:
      return "auto-primary";
    case MICROLINK_REGION_SRC_AUTO_FLEET:
      return "auto-fleet";
    default:
      return "auto";
  }
}

void microlink_notify_priority_health(microlink_t * ml, bool healthy)
{
  if (ml) {
    ml->priority_link_healthy = healthy;
  }
}

void microlink_notify_fleet_health(microlink_t * ml, bool healthy)
{
  if (ml) {
    ml->fleet_link_healthy = healthy;
  }
}

int microlink_get_peer_count(const microlink_t * ml)
{
  return ml ? ml->peer_count : 0;
}

esp_err_t microlink_get_peer_info(const microlink_t * ml, int index, microlink_peer_info_t * info)
{
  if (!ml || !info || index < 0 || index >= ml->peer_count) {
    return ESP_ERR_INVALID_ARG;
  }
  const ml_peer_t * p = &ml->peers[index];
  info->vpn_ip = p->vpn_ip;
  strlcpy(info->hostname, p->hostname, sizeof(info->hostname));
  memcpy(info->public_key, p->public_key, 32);
  info->online = p->active;
  info->direct_path = p->has_direct_path;
  info->derp_region = p->derp_region;
  info->endpoint_count = p->endpoint_count;
  info->best_ip = p->best_ip;
  info->best_port = (uint16_t)p->best_port;
  info->hs_cand_ip = 0;
  info->hs_cand_port = 0;
  info->wg_up = false;
  info->wg_active = false;
  info->wg_send_hs = false;
  info->wg_hs_pending = false;
  info->wg_init_age_ms = 0xFFFFFFFFu; /* "never" until a WG peer says otherwise */
  uint64_t now = ml_get_time_ms();
  info->ping_age_ms = (p->last_ping_sent_ms != 0) ? (uint32_t)(now - p->last_ping_sent_ms) : 0xFFFFFFFFu;
  info->backoff_ms = (p->direct_backoff_until > now) ? (uint32_t)(p->direct_backoff_until - now) : 0u;
  if (ml->wg_netif != NULL && p->wg_peer_index >= 0) {
    struct netif * netif = (struct netif *)ml->wg_netif;
    ip_addr_t cur_ip;
    u16_t cur_port;
    info->wg_up = (wireguardif_peer_is_up(netif, (u8_t)p->wg_peer_index, &cur_ip, &cur_port) == ERR_OK);
    /* Diagnostic snapshot of plain scalars owned by the TCPIP thread, read
     * without the core lock on purpose: a torn read can only yield a stale
     * bool or age for one JSON sample, never a fault, and taking the lock from
     * the HTTP task for telemetry is what stalled the safety loop before. */
    struct wireguard_device * dev = (struct wireguard_device *)netif->state;
    if (dev != NULL && p->wg_peer_index < WIREGUARD_MAX_PEERS) {
      const struct wireguard_peer * wp = &dev->peers[p->wg_peer_index];
      info->wg_active = wp->active;
      info->wg_send_hs = wp->send_handshake;
      info->wg_hs_pending = wp->handshake.valid;
      /* Handshake second-leg candidate: same lock-free telemetry snapshot (the
       * locked wireguardif_get_hs_candidate() is for the disco task's decisions,
       * not for the HTTP task — see the comment above). */
      if (
        !ip_addr_isany(&wp->hs_cand_ip) && wp->hs_cand_port != 0 &&
        !wireguard_expired(wp->hs_cand_ms, HS_CAND_FRESH_MS / 1000))
      {
        info->hs_cand_ip = lwip_ntohl(ip4_addr_get_u32(ip_2_ip4(&wp->hs_cand_ip)));
        info->hs_cand_port = wp->hs_cand_port;
      }
      uint32_t wg_now = sys_now(); /* wireguardif stamps with lwIP sys_now(), not esp_timer */
      info->wg_init_age_ms = (wp->last_initiation_tx != 0) ? (wg_now - wp->last_initiation_tx) : 0xFFFFFFFFu;
    }
  }
  return ESP_OK;
}

/* ============================================================================
 * Send API
 * ========================================================================== */

esp_err_t microlink_send(microlink_t * ml, uint32_t dest_vpn_ip, const uint8_t * data, size_t len)
{
  if (!ml || !data || len == 0 || len > 1400) return ESP_ERR_INVALID_ARG;
  if (ml->state != ML_STATE_CONNECTED) return ESP_ERR_INVALID_STATE;

  /* Find peer by VPN IP */
  for (int i = 0; i < ml->peer_count; i++) {
    if (ml->peers[i].vpn_ip == dest_vpn_ip && ml->peers[i].active) {
      /* TODO: Route through WireGuard tunnel */
      /* For now, queue via DERP as fallback */
      return ml_derp_queue_send(ml, ml->peers[i].public_key, data, len);
    }
  }
  return ESP_ERR_NOT_FOUND;
}

/* ============================================================================
 * Callbacks
 * ========================================================================== */

void microlink_set_state_callback(microlink_t * ml, microlink_state_cb_t cb, void * user_data)
{
  if (ml) {
    ml->state_cb = cb;
    ml->state_cb_data = user_data;
  }
}

void microlink_set_peer_callback(microlink_t * ml, microlink_peer_cb_t cb, void * user_data)
{
  if (ml) {
    ml->peer_cb = cb;
    ml->peer_cb_data = user_data;
  }
}

void microlink_set_data_callback(microlink_t * ml, microlink_data_cb_t cb, void * user_data)
{
  if (ml) {
    ml->data_cb = cb;
    ml->data_cb_data = user_data;
  }
}

void microlink_set_peer_wanted_cb(microlink_t * ml, microlink_peer_wanted_cb_t cb, void * ctx)
{
  if (ml) {
    ml->peer_wanted_cb = cb;
    ml->peer_wanted_ctx = ctx;
  }
}

/* ============================================================================
 * Utilities
 * ========================================================================== */

void microlink_ip_to_str(uint32_t ip, char * buf)
{
  snprintf(
    buf,
    16,
    "%lu.%lu.%lu.%lu",
    (unsigned long)((ip >> 24) & 0xFF),
    (unsigned long)((ip >> 16) & 0xFF),
    (unsigned long)((ip >> 8) & 0xFF),
    (unsigned long)(ip & 0xFF));
}

int microlink_get_rssi_dbm(void)
{
  wifi_ap_record_t ap;
  if (esp_wifi_sta_get_ap_info(&ap) != ESP_OK) return 0;
  return ap.rssi;
}

esp_err_t microlink_get_heap_info(uint32_t * free_total, uint32_t * largest_block)
{
  if (free_total) *free_total = (uint32_t)esp_get_free_heap_size();
  if (largest_block) *largest_block = (uint32_t)heap_caps_get_largest_free_block(MALLOC_CAP_8BIT);
  return ESP_OK;
}

uint32_t microlink_parse_ip(const char * ip_str)
{
  if (!ip_str) return 0;
  unsigned int a, b, c, d;
  if (sscanf(ip_str, "%u.%u.%u.%u", &a, &b, &c, &d) != 4) return 0;
  if (a > 255 || b > 255 || c > 255 || d > 255) return 0;
  return (a << 24) | (b << 16) | (c << 8) | d;
}

const char * microlink_default_device_name(void)
{
  static char name[48] = {0};
  if (name[0] == 0) {
    uint8_t mac[6];
    esp_read_mac(mac, ESP_MAC_WIFI_STA);

    /* Use ML_DEVICE_NAME as prefix if configured, otherwise "esp32" */
    const char * prefix = CONFIG_ML_DEVICE_NAME;
    if (!prefix || !prefix[0]) prefix = "esp32";
    snprintf(name, sizeof(name), "%s-%02x%02x%02x%02x%02x%02x", prefix, mac[0], mac[1], mac[2], mac[3], mac[4], mac[5]);
  }
  return name;
}

uint64_t ml_get_time_ms(void)
{
  return (uint64_t)(esp_timer_get_time() / 1000ULL);
}

/* ============================================================================
 * MagicDNS — Resolve tailnet hostnames against peer list
 * ========================================================================== */

/* Case-insensitive string compare (limited to len bytes) */
static int strncasecmp_local(const char * a, const char * b, size_t len)
{
  for (size_t i = 0; i < len; i++) {
    char ca = a[i], cb = b[i];
    if (ca >= 'A' && ca <= 'Z') ca += 32;
    if (cb >= 'A' && cb <= 'Z') cb += 32;
    if (ca != cb) return ca - cb;
    if (ca == '\0') return 0;
  }
  return 0;
}

uint32_t microlink_resolve(const microlink_t * ml, const char * hostname)
{
  if (!ml || !hostname || hostname[0] == '\0') return 0;

  size_t query_len = strlen(hostname);

  for (int i = 0; i < ml->peer_count; i++) {
    const ml_peer_t * p = &ml->peers[i];
    if (!p->active || p->hostname[0] == '\0') continue;

    /* 1. Exact match (case-insensitive) */
    if (strncasecmp_local(p->hostname, hostname, sizeof(p->hostname)) == 0) {
      return p->vpn_ip;
    }

    /* 2. Prefix match: query "npc1" matches peer "npc1.tail12345.ts.net"
         * The query must match up to the first '.' in the peer hostname. */
    const char * dot = strchr(p->hostname, '.');
    if (dot) {
      size_t short_len = (size_t)(dot - p->hostname);
      if (query_len == short_len && strncasecmp_local(p->hostname, hostname, short_len) == 0) {
        return p->vpn_ip;
      }
    }
  }

  return 0; /* Not found */
}
