polymathrobotics/protective-stop/components/microlink/src/ml_wg_mgr.c

// SPDX-FileCopyrightText: 2026 Polymath Robotics
// SPDX-License-Identifier: Apache-2.0

/**
 * @file ml_wg_mgr.c
 * @brief WireGuard Manager Task - Peer Management + DISCO
 *
 * Owns ALL peer state exclusively. Handles:
 * - Peer add/remove/update from coord task (via peer_update_queue)
 * - DISCO ping/pong with rate limiting (matching tailscaled timing)
 * - WireGuard peer provisioning via wireguard-lwip
 * - Direct path discovery and endpoint switching
 *
 * Reference: tailscale/wgengine/magicsock/magicsock.go
 *            tailscale/disco/disco.go
 */

#include <errno.h>
#include <stdio.h>
#include <string.h>

#include "arch/sys_arch.h"
#include "esp_log.h"
#include "esp_netif.h"
#include "esp_random.h"
#include "lwip/ip.h"
#include "lwip/ip4_addr.h"
#include "lwip/ip_addr.h"
#include "lwip/netif.h"
#include "lwip/pbuf.h"
#include "lwip/sockets.h"
#include "lwip/tcpip.h"
#include "mbedtls/base64.h"
#include "microlink_internal.h"
#include "ml_config_httpd.h"
#include "ml_demote_verdict.h"
#include "ml_wg_regain_policy.h"
#include "nacl_box.h"
#include "wireguard.h"
#include "wireguardif.h"

/* Forward declaration for zero-copy path */
extern void wireguardif_network_rx(
  void * arg, struct udp_pcb * pcb, struct pbuf * p, const ip_addr_t * addr, u16_t port);

static const char * TAG = "ml_wg_mgr";

/* v15.20 (upstream PR#14): take lwIP TCPIP core lock around any direct
 * lwIP API call (udp_sendto, wireguardif_network_rx, etc.) made from a
 * non-TCPIP thread. Required by CONFIG_LWIP_TCPIP_CORE_LOCKING=y in
 * sdkconfig.defaults. Without this the chip silently panics after
 * ~100-180 s of sustained direct-UDP traffic — corrupted pbuf/netif
 * state from concurrent access. See upstream microlink issues #14, #15. */
static inline bool ml_lwip_core_lock_needed(void)
{
  return !sys_thread_tcpip(LWIP_CORE_LOCK_QUERY_HOLDER);
}

/* Forward declarations */
static void disco_send_call_me_maybe(microlink_t * ml, int peer_idx);
static void wg_mgr_drain_wg_rx(microlink_t * ml);
static int add_peer(microlink_t * ml, const ml_peer_update_t * update, bool * skipped);

static int s_wg_hs_budget; /* reset each wg_mgr pass */
static uint32_t s_diag_wg_hs_deferred;
static uint32_t s_diag_wg_hs_dropped;
/* Per-pass work counters — inputs to the stall-event ring. */
static uint16_t s_pass_wg_pkts;
static uint16_t s_pass_wg_handshakes;
static uint16_t s_pass_peer_adds;
static uint16_t s_pass_disco_opens;
static uint16_t s_pass_periodic_ms;
static uint16_t s_pass_probe_ms;
static uint16_t s_pass_cmm_sends; /* counted in disco_send_call_me_maybe (6 call sites) */
static uint16_t s_pass_nvs_flush_ms; /* flash-flush wall-clock this pass */
static uint16_t s_pass_ingest_ms; /* process_peer_updates wall-clock this pass */
static uint16_t s_pass_drain_ms; /* cumulative wg-rx drain wall-clock this pass */

/* Stall-event ring: wg_mgr-owned writer; entries published via a
 * release-stored index so httpd never reads a torn published entry. */
static ml_wg_stall_event_t s_wg_stall_ring[ML_STALL_RING_LEN];
static volatile uint32_t s_wg_stall_widx; /* total events; entry i at i%LEN */

/* v15.22 — WG data-packet dedup ring.
 *
 * Tailscale's host-side tailscaled sends every transport-data packet via
 * BOTH the direct UDP path AND the DERP relay path simultaneously (its
 * normal redundancy posture until it's certain only the direct path is
 * needed). On the chip that doubled the WG processing rate: each packet
 * was decrypted + replay-checked + ip_input'd twice. wireguard_lwip's
 * replay window does eventually reject the second copy, but only AFTER
 * the full ChaCha20-Poly1305 decrypt — wasted work that accumulated
 * pressure on lwIP state and was the residual ~40-80 min wedge trigger
 * we still saw after the v15.20 core-locking fix.
 *
 * Fix: peek at the WG header (receiver_index + counter) before the pbuf
 * copy. If we've seen this (peer, nonce) pair within the last few
 * packets, drop the duplicate.
 *
 * Layout of MESSAGE_TRANSPORT_DATA (RFC §5.4.6):
 *   u8  type        = 4
 *   u8  reserved[3] = 0
 *   u32 receiver    (little-endian, our local peer index)
 *   u64 counter     (little-endian, sender's nonce)
 *   u8  encrypted_data[...]
 *
 * Ring is global (not per-peer): (receiver, counter) is already unique
 * across peers because receiver is *our* per-peer index. 16 slots is
 * way more than the network ever stretches the direct-vs-DERP gap. */
#define WG_DEDUP_RING_SIZE 64

typedef struct
{
  uint32_t receiver;
  uint64_t counter;
} wg_dedup_entry_t;

static wg_dedup_entry_t s_wg_dedup_ring[WG_DEDUP_RING_SIZE];
static int s_wg_dedup_head = 0;
static uint32_t s_wg_dedup_drops = 0;

static inline bool wg_dedup_is_duplicate(uint32_t receiver, uint64_t counter)
{
  for (int i = 0; i < WG_DEDUP_RING_SIZE; i++) {
    if (s_wg_dedup_ring[i].receiver == receiver && s_wg_dedup_ring[i].counter == counter) {
      return true;
    }
  }
  /* Not seen — record it. Ring write is single-threaded (all calls
     * come from ml_wg_mgr task), so no locking needed. */
  s_wg_dedup_ring[s_wg_dedup_head].receiver = receiver;
  s_wg_dedup_ring[s_wg_dedup_head].counter = counter;
  s_wg_dedup_head = (s_wg_dedup_head + 1) % WG_DEDUP_RING_SIZE;
  return false;
}

uint32_t ml_wg_mgr_get_dedup_drops(void)
{
  return s_wg_dedup_drops;
}

static void disco_send_ping_to_peer(microlink_t * ml, int peer_idx, bool force);

/* DISCO message types */
#define DISCO_MSG_PING 0x01
#define DISCO_MSG_PONG 0x02
#define DISCO_MSG_CALL_ME_MAYBE 0x03

/* DISCO magic bytes: "TS" + sparkles emoji UTF-8 */
static const uint8_t DISCO_MAGIC[6] = {'T', 'S', 0xf0, 0x9f, 0x92, 0xac};

#define DISCO_TXID_LEN 12
#define DISCO_NONCE_LEN 24

/* Check if an IP (host byte order) is a LAN address */
static inline bool is_lan_ip(uint32_t ip)
{
  return ((ip >> 24) == 10) || /* 10.x.x.x */
         ((ip >> 16) == 0xC0A8) || /* 192.168.x.x */
         (((ip >> 16) & 0xFFF0) == 0xAC10); /* 172.16-31.x.x */
}

/* Pending DISCO probe tracking */
typedef struct
{
  uint8_t txid[DISCO_TXID_LEN];
  uint32_t dest_ip;
  uint16_t dest_port;
  uint64_t sent_ms;
  /* ms of the FIRST via-DERP pong match (0 = none yet). A via-DERP match no
   * longer consumes the slot (pong-race fix: the direct pong to the same
   * dual-sent ping must still be able to promote), but the slot may then live
   * only ML_DISCO_DERP_MATCH_GRACE_MS more — an unbounded (full 5 s) lifetime
   * is what exhausted this table on the 2026-08-09 bench and demoted healthy
   * paths (see ML_DISCO_DERP_MATCH_GRACE_MS). */
  uint64_t derp_match_ms;
  int peer_index;
  bool active;
  bool safety; /* probe to a safety peer: may use the reserved slot tail and
                * stays matchable ML_DISCO_SAFETY_PROBE_TTL_MS (late pongs
                * behind a far-end DERP reconnect must still learn endpoints) */
} disco_probe_t;

#define MAX_PENDING_PROBES 64
static disco_probe_t pending_probes[MAX_PENDING_PROBES];

/* Small ring of the last few CONSUMED probe txids. The machine answers each ping
 * on BOTH direct and DERP with the same txid; the direct pong consumes the
 * probe, so the DERP duplicate arrives "unmatched". Recognising it here lets us
 * log it at DEBUG ("duplicate via-DERP pong") instead of a misleading WARN.
 * Cosmetic only — never affects probe matching or heartbeat accounting. */
#define CONSUMED_TXID_RING 8
static uint8_t s_consumed_txids[CONSUMED_TXID_RING][DISCO_TXID_LEN];
static int s_consumed_txid_head = 0;

static void remember_consumed_txid(const uint8_t * txid)
{
  memcpy(s_consumed_txids[s_consumed_txid_head], txid, DISCO_TXID_LEN);
  s_consumed_txid_head = (s_consumed_txid_head + 1) % CONSUMED_TXID_RING;
}

static bool txid_recently_consumed(const uint8_t * txid)
{
  for (int i = 0; i < CONSUMED_TXID_RING; i++) {
    if (memcmp(s_consumed_txids[i], txid, DISCO_TXID_LEN) == 0) return true;
  }
  return false;
}

/* ============================================================================
 * Base64 Key Encoding (wireguard-lwip API requires base64 keys)
 * ========================================================================== */

static void key_to_base64(const uint8_t * key, char * b64, size_t b64_size)
{
  size_t olen = 0;
  mbedtls_base64_encode((unsigned char *)b64, b64_size, &olen, key, 32);
  b64[olen] = '\0';
}

/* ============================================================================
 * UDP Send Helper — routes via BSD socket or zero-copy PCB
 *
 * All direct DISCO/WG UDP sends go through this function.
 * dest_ip is HOST byte order, dest_port is HOST byte order.
 * ========================================================================== */

static inline bool disco_has_udp_path(const microlink_t * ml)
{
#ifdef CONFIG_ML_ZERO_COPY_WG
  if (ml->zc.pcb) return true;
#endif
  return (ml->disco_sock4 >= 0);
}

static int disco_udp_sendto(
  microlink_t * ml, const uint8_t * data, size_t len, uint32_t dest_ip_hbo, uint16_t dest_port)
{
#ifdef CONFIG_ML_ZERO_COPY_WG
  if (ml->zc.pcb) {
    return (ml_zerocopy_send(ml, data, len, dest_ip_hbo, dest_port) == ESP_OK) ? len : -1;
  }
#endif
  if (ml->disco_sock4 < 0) return -1;

  struct sockaddr_in dest;
  memset(&dest, 0, sizeof(dest));
  dest.sin_family = AF_INET;
  dest.sin_port = htons(dest_port);
  dest.sin_addr.s_addr = htonl(dest_ip_hbo);

  return ml_sendto(ml->disco_sock4, data, len, MSG_DONTWAIT, (struct sockaddr *)&dest, sizeof(dest));
}

/* ============================================================================
 * WireGuard Output Callbacks (for magicsock mode)
 * ========================================================================== */

/* Called by wireguard-lwip when a peer has no direct endpoint (DERP relay) */
static err_t wg_derp_output_cb(const uint8_t * peer_public_key, const uint8_t * data, size_t len, void * ctx)
{
  microlink_t * ml = (microlink_t *)ctx;
  /* Any pool connection up is enough to accept the relay: ml_derp_queue_send
   * tags the frame with the destination's region and the DERP task routes it to
   * the home OR the matching aux conn (cross-region peers ride an aux slot). */
  bool derp_up = false;
  if (ml) {
    for (int i = 0; i < ML_DERP_MAX_CONNS; i++) {
      if (ml->derp[i].connected) {
        derp_up = true;
        break;
      }
    }
  }
  if (!ml || !derp_up) {
    ESP_LOGW(TAG, "DERP output cb: not connected, dropping %d bytes", (int)len);
    return ERR_CONN;
  }

  /* Log WG handshake initiations with key and one-time hex dump */
  if (len >= 4 && data[0] == 0x01) {
    static int init_dump_count = 0;
    const char * hostname = "?";
    for (int i = 0; i < ml->peer_count; i++) {
      if (memcmp(ml->peers[i].public_key, peer_public_key, 32) == 0) {
        hostname = ml->peers[i].hostname;
        break;
      }
    }
    ESP_LOGI(
      TAG,
      "WG INIT -> %s len=%d key=%02x%02x%02x%02x%02x%02x%02x%02x",
      hostname,
      (int)len,
      peer_public_key[0],
      peer_public_key[1],
      peer_public_key[2],
      peer_public_key[3],
      peer_public_key[4],
      peer_public_key[5],
      peer_public_key[6],
      peer_public_key[7]);

    /* Dump first handshake fully for byte-level verification */
    if (init_dump_count < 1 && len == 148) {
      init_dump_count++;
      /* WG handshake init: type(1) reserved(3) sender(4) ephemeral(32)
             * enc_static(48) enc_timestamp(28) mac1(16) mac2(16) = 148 */
      ESP_LOGI(
        TAG,
        "  type=%02x res=%02x%02x%02x sender=%02x%02x%02x%02x",
        data[0],
        data[1],
        data[2],
        data[3],
        data[4],
        data[5],
        data[6],
        data[7]);
      ESP_LOGI(
        TAG,
        "  ephemeral=%02x%02x%02x%02x...%02x%02x%02x%02x",
        data[8],
        data[9],
        data[10],
        data[11],
        data[36],
        data[37],
        data[38],
        data[39]);
      ESP_LOGI(
        TAG,
        "  mac1=%02x%02x%02x%02x%02x%02x%02x%02x%02x%02x%02x%02x%02x%02x%02x%02x",
        data[116],
        data[117],
        data[118],
        data[119],
        data[120],
        data[121],
        data[122],
        data[123],
        data[124],
        data[125],
        data[126],
        data[127],
        data[128],
        data[129],
        data[130],
        data[131]);
      ESP_LOGI(
        TAG,
        "  mac2=%02x%02x%02x%02x%02x%02x%02x%02x%02x%02x%02x%02x%02x%02x%02x%02x",
        data[132],
        data[133],
        data[134],
        data[135],
        data[136],
        data[137],
        data[138],
        data[139],
        data[140],
        data[141],
        data[142],
        data[143],
        data[144],
        data[145],
        data[146],
        data[147]);
    }
  }

  esp_err_t err = ml_derp_queue_send(ml, peer_public_key, data, len);
  return (err == ESP_OK) ? ERR_OK : ERR_MEM;
}

/* Called by wireguard-lwip when sending via external UDP socket (magicsock).
 * Uses raw lwIP udp_sendto() instead of BSD sendto() to avoid deadlock
 * when called from the TCPIP thread context (via tcpip_input → ip_input →
 * icmp/tcp reply → wireguardif_output → this callback). BSD sendto() posts
 * a message to the TCPIP thread and waits, which deadlocks if we're already
 * on that thread. */
static struct udp_pcb * s_wg_output_pcb = NULL;

static err_t wg_udp_output_cb(uint32_t dest_ip, uint16_t dest_port, const uint8_t * data, size_t len, void * ctx)
{
  microlink_t * ml = (microlink_t *)ctx;
  if (!ml) return ERR_CONN;

  /* Log WG packets sent via direct UDP */
  uint32_t ip_host = ntohl(dest_ip);
  ESP_LOGI(
    TAG,
    "WG UDP TX: %d bytes -> %d.%d.%d.%d:%d type=%d",
    (int)len,
    (int)((ip_host >> 24) & 0xFF),
    (int)((ip_host >> 16) & 0xFF),
    (int)((ip_host >> 8) & 0xFF),
    (int)(ip_host & 0xFF),
    (int)dest_port,
    len >= 1 ? data[0] : -1);

  /* Use raw PCB to send — safe from any thread context */
  if (!s_wg_output_pcb) return ERR_CONN;

  struct pbuf * p = pbuf_alloc(PBUF_TRANSPORT, len, PBUF_RAM);
  if (!p) return ERR_MEM;
  memcpy(p->payload, data, len);

  ip_addr_t dst;
  IP_SET_TYPE_VAL(dst, IPADDR_TYPE_V4);
  ip4_addr_set_u32(ip_2_ip4(&dst), dest_ip); /* already network byte order */

  bool need_lock = ml_lwip_core_lock_needed();
  if (need_lock) {
    LOCK_TCPIP_CORE();
  }
  err_t err = udp_sendto(s_wg_output_pcb, p, &dst, dest_port);
  if (need_lock) {
    UNLOCK_TCPIP_CORE();
  }
  pbuf_free(p);
  return err;
}

/* ============================================================================
 * WireGuard Interface Initialization
 * ========================================================================== */

static esp_err_t wg_init_interface(microlink_t * ml)
{
  /* Convert our WG private key to base64 */
  char privkey_b64[64];
  key_to_base64(ml->wg_private_key, privkey_b64, sizeof(privkey_b64));

  /* Allocate lwIP netif */
  struct netif * netif = (struct netif *)calloc(1, sizeof(struct netif));
  if (!netif) {
    ESP_LOGE(TAG, "Failed to allocate WG netif");
    return ESP_FAIL;
  }

  /* Prepare init data */
  struct wireguardif_init_data wg_init = {0};
  wg_init.private_key = privkey_b64;
  wg_init.listen_port = 51820;
  wg_init.bind_netif = NULL;

  /* Disable internal socket binding (we use magicsock mode) */
  wireguardif_disable_socket_bind();

  /* v15.23: take TCPIP core lock around wireguardif_init + netif setup
     * + udp_new. These run at boot — low risk in practice (TCPIP thread
     * isn't processing real traffic yet) but unsafe without the lock per
     * upstream PR#14 audit. */
  /* #157: monotonic handshake timestamps across reboots — one NVS commit, done
   * BEFORE taking the TCPIP core lock so the flash write stalls no lwIP caller. */
  (void)wireguard_tai64n_epoch_init();

  bool init_need_lock = ml_lwip_core_lock_needed();
  if (init_need_lock) {
    LOCK_TCPIP_CORE();
  }

  /* Initialize WireGuard netif */
  netif->state = &wg_init;
  err_t err = wireguardif_init(netif);
  if (err != ERR_OK) {
    if (init_need_lock) {
      UNLOCK_TCPIP_CORE();
    }
    ESP_LOGE(TAG, "wireguardif_init failed: %d", err);
    free(netif);
    return ESP_FAIL;
  }

  /* Set IP addresses: our VPN IP (or temporary until we get one) */
  if (ml->vpn_ip != 0) {
    uint8_t a = (ml->vpn_ip >> 24) & 0xFF;
    uint8_t b = (ml->vpn_ip >> 16) & 0xFF;
    uint8_t c = (ml->vpn_ip >> 8) & 0xFF;
    uint8_t d = ml->vpn_ip & 0xFF;
    IP4_ADDR(&netif->ip_addr.u_addr.ip4, a, b, c, d);
  } else {
    IP4_ADDR(&netif->ip_addr.u_addr.ip4, 100, 64, 0, 1); /* temp */
  }
  IP4_ADDR(&netif->netmask.u_addr.ip4, 255, 192, 0, 0); /* /10 */
  IP4_ADDR(&netif->gw.u_addr.ip4, 0, 0, 0, 0);

  /* Use tcpip_input so decrypted packets are posted to the TCPIP thread.
     * Required for TCP (esp_http_server sockets) — ip_input from the wg_mgr
     * thread accesses TCP PCB state without synchronization.  The WG output
     * callback uses raw udp_sendto (not BSD sendto) to avoid deadlock. */
  netif->input = tcpip_input;

  /* Add to lwIP netif list (bypass netif_add which wants init callback) */
  netif->next = netif_list;
  netif_list = netif;

  /* Bring interface up */
  netif_set_up(netif);
  netif_set_link_up(netif);

  /* Create raw UDP PCB for WG output (avoids BSD sendto deadlock on TCPIP
     * thread).  Bind to port 51820 to match the DISCO socket source port.
     * The existing BSD disco_sock4 is only used from the wg_mgr task for
     * DISCO/STUN; this raw PCB is used from the TCPIP thread for WG output. */
  if (!s_wg_output_pcb) {
    s_wg_output_pcb = udp_new();
    if (s_wg_output_pcb) {
      /* Set source port to 51820 — MUST match disco_sock4 so WG handshake
             * responses share the same NAT mapping as DISCO/STUN.  We set
             * local_port directly instead of calling udp_bind() to avoid
             * registering this PCB as a listener (which would steal incoming
             * packets from disco_sock4's BSD socket). */
      s_wg_output_pcb->local_port = 51820;
      /* DSCP 46 (EF) → WMM AC_VO for low-latency WiFi scheduling */
      s_wg_output_pcb->tos = 0xB8;
    }
  }

  if (init_need_lock) {
    UNLOCK_TCPIP_CORE();
  }

  /* Register output callbacks for magicsock mode (these just store fn
     * pointers on the netif state, no lwIP core access) */
  wireguardif_set_derp_output(netif, wg_derp_output_cb, ml);
  wireguardif_set_udp_output(netif, wg_udp_output_cb, ml);

  ml->wg_netif = netif;

  /* Verify WG device public key matches our expected key */
  {
    struct wireguard_device * dev = (struct wireguard_device *)netif->state;
    if (dev) {
      bool match = (memcmp(dev->public_key, ml->wg_public_key, 32) == 0);
      ESP_LOGI(
        TAG,
        "WG device pubkey: %02x%02x%02x%02x... %s ml->wg_public_key",
        dev->public_key[0],
        dev->public_key[1],
        dev->public_key[2],
        dev->public_key[3],
        match ? "MATCHES" : "MISMATCH!");
      if (!match) {
        ESP_LOGE(
          TAG,
          "  Expected: %02x%02x%02x%02x...",
          ml->wg_public_key[0],
          ml->wg_public_key[1],
          ml->wg_public_key[2],
          ml->wg_public_key[3]);
      }
    }
  }

  ESP_LOGI(TAG, "WireGuard interface initialized (magicsock mode)");
  return ESP_OK;
}

static void wg_update_vpn_ip(microlink_t * ml)
{
  if (ml->wg_netif && ml->vpn_ip != 0) {
    struct netif * netif = (struct netif *)ml->wg_netif;
    uint8_t a = (ml->vpn_ip >> 24) & 0xFF;
    uint8_t b = (ml->vpn_ip >> 16) & 0xFF;
    uint8_t c = (ml->vpn_ip >> 8) & 0xFF;
    uint8_t d = ml->vpn_ip & 0xFF;
    IP4_ADDR(&netif->ip_addr.u_addr.ip4, a, b, c, d);
  }
}

/* ============================================================================
 * Peer Management (owned exclusively by this task)
 * ========================================================================== */

static int find_peer_by_key(microlink_t * ml, const uint8_t * pubkey)
{
  for (int i = 0; i < ml->peer_count; i++) {
    if (ml->peers[i].active && memcmp(ml->peers[i].public_key, pubkey, 32) == 0) {
      return i;
    }
  }
  return -1;
}

static int find_peer_by_ip(microlink_t * ml, uint32_t vpn_ip)
{
  for (int i = 0; i < ml->peer_count; i++) {
    if (ml->peers[i].active && ml->peers[i].vpn_ip == vpn_ip) {
      return i;
    }
  }
  return -1;
}

/* Fleet coordination/OTA server VPN IP (CONFIG_ML_FLEET_SERVER_IP), parsed
 * once. 0 if unset. */
static uint32_t fleet_server_ip_cached(void)
{
  static uint32_t ip;
  static bool done;
  if (!done) {
    ip = microlink_parse_ip(CONFIG_ML_FLEET_SERVER_IP);
    done = true;
  }
  return ip;
}

/* Peers that must always keep a WG slot and are never evicted: the priority
 * (safety) peer — the machine — and the management/OTA server. On a
 * large tailnet (100s of peers, trimmed to ML_MAX_PEERS) either could
 * otherwise fall out of the table, leaving the chip unable to reach the
 * machine (unsafe) or the management server (no OTA/coordination). */
/* Additional always-pinned VPN IPs registered by the application — e.g.
 * every configured pstop machine slot. Without this, a machine that joins
 * the tailnet after the chip's last full netmap (or that has no recent
 * activity) gets trimmed by the ML_MAX_PEERS cap and the remote can never
 * bond to it (observed: EHOSTUNREACH on every BOND, bench 2026-07-31). */
#define ML_EXTRA_PINS 16
static uint32_t s_extra_pins[ML_EXTRA_PINS];

/* True path RTT to a peer from the disco layer (txid-matched ping->pong,
 * identical semantics from either end of a link — unlike the pstop loop
 * timings, which are quantized by protocol hold times). Returns 0 if the
 * peer is unknown or never ponged; age_ms_out (optional) = how stale the
 * measurement is; direct_out (optional) = measured over the direct path. */
uint32_t microlink_get_peer_rtt(microlink_t * ml, uint32_t vpn_ip, uint32_t * age_ms_out, bool * direct_out)
{
  if (ml == NULL) return 0;
  int idx = find_peer_by_ip(ml, vpn_ip);
  if (idx < 0) return 0;
  ml_peer_t * p = &ml->peers[idx];
  if (p->last_pong_recv_ms == 0) return 0;
  if (age_ms_out != NULL) {
    uint64_t now = ml_get_time_ms();
    *age_ms_out = (now > p->last_pong_recv_ms) ? (uint32_t)(now - p->last_pong_recv_ms) : 0u;
  }
  if (direct_out != NULL) *direct_out = p->disco_rtt_direct;
  return p->disco_rtt_ms;
}

/* Per-peer application-level health, the multi-machine generalization of
 * microlink_notify_priority_health(): the pstop layer reports, per machine
 * TARGET, whether heartbeat replies are flowing. Each unhealthy entry gets
 * the same zombie-keypair treatment as the priority peer — a disco-first
 * wake forcing a fresh 1-RTT handshake — so a power-cycled machine
 * re-bonds in seconds instead of waiting out WG rekey timers. Without
 * this, only an ALL-machines-silent device recovered fast (the aggregate
 * kick deliberately refused to churn a partially-healthy transport). */
typedef struct
{
  uint32_t ip;
  volatile bool healthy;
} ml_health_ent_t;

static ml_health_ent_t s_health_peers[ML_EXTRA_PINS];

static bool is_health_tracked(uint32_t vpn_ip)
{
  for (int i = 0; i < ML_EXTRA_PINS; i++) {
    if ((s_health_peers[i].ip != 0) && (s_health_peers[i].ip == vpn_ip)) return true;
  }
  return false;
}

void microlink_untrack_peer_health(microlink_t * ml, uint32_t vpn_ip)
{
  (void)ml;
  for (int i = 0; i < ML_EXTRA_PINS; i++) {
    if (s_health_peers[i].ip == vpn_ip) {
      s_health_peers[i].ip = 0;
      return;
    }
  }
}

void microlink_notify_peer_health(microlink_t * ml, uint32_t vpn_ip, bool healthy)
{
  (void)ml;
  if (vpn_ip == 0) return;
  int free_slot = -1;
  for (int i = 0; i < ML_EXTRA_PINS; i++) {
    if (s_health_peers[i].ip == vpn_ip) {
      s_health_peers[i].healthy = healthy;
      return;
    }
    if ((free_slot < 0) && (s_health_peers[i].ip == 0)) free_slot = i;
  }
  if (free_slot >= 0) {
    s_health_peers[free_slot].ip = vpn_ip;
    s_health_peers[free_slot].healthy = healthy;
  }
}

void microlink_pin_peer_ip(microlink_t * ml, uint32_t vpn_ip, bool pin)
{
  (void)ml;
  if (vpn_ip == 0) return;
  for (int i = 0; i < ML_EXTRA_PINS; i++) {
    if (pin && s_extra_pins[i] == vpn_ip) return; /* already pinned */
    if (!pin && s_extra_pins[i] == vpn_ip) {
      s_extra_pins[i] = 0;
      return;
    }
  }
  if (pin) {
    for (int i = 0; i < ML_EXTRA_PINS; i++) {
      if (s_extra_pins[i] == 0) {
        s_extra_pins[i] = vpn_ip;
        return;
      }
    }
  }
}

/* Cached copy of ml->config.priority_peer_ip so ml_config_peer_is_allowed()
 * (other module, no ml handle) can exempt every pin — set at wg task start. */
static uint32_t s_priority_pin_ip;

/* One extra-pins membership scan shared by both pin checks below. */
static bool extra_pin_contains(uint32_t vpn_ip)
{
  for (int i = 0; i < ML_EXTRA_PINS; i++) {
    if (s_extra_pins[i] != 0 && vpn_ip == s_extra_pins[i]) return true;
  }
  return false;
}

bool ml_wg_ip_is_pinned(uint32_t vpn_ip)
{
  if (vpn_ip == 0) return false;
  if (s_priority_pin_ip != 0 && vpn_ip == s_priority_pin_ip) return true;
  return extra_pin_contains(vpn_ip);
}

static bool is_pinned_peer(microlink_t * ml, uint32_t vpn_ip)
{
  if (vpn_ip == 0) return false;
  /* Live ml->config read (not the s_priority_pin_ip cache): valid before the
   * wg task start that populates the cache for the cross-module variant. */
  if (ml->config.priority_peer_ip != 0 && vpn_ip == ml->config.priority_peer_ip) {
    return true;
  }
  if (extra_pin_contains(vpn_ip)) {
    return true;
  }
  uint32_t fip = fleet_server_ip_cached();
  return (fip != 0 && vpn_ip == fip);
}

/* Public wrapper so ml_coord can prioritise pinned-peer updates on the
 * coord->wg_mgr queue (their DERP region drives the re-home; dropping it leaves
 * a NAT'd unit relay-unreachable). */
bool ml_wg_is_pinned_peer(microlink_t * ml, uint32_t vpn_ip)
{
  return is_pinned_peer(ml, vpn_ip);
}

/* Public wrapper: is this peer in the health-tracked safety set? Diagnostic use
 * (e.g. /api/peers) to see which peers feed ml_wg_collect_safety_regions. */
bool ml_wg_is_health_tracked(uint32_t vpn_ip)
{
  return is_health_tracked(vpn_ip);
}

/* THE safety-peer membership test — the single definition of "this peer's
 * link carries the safety heartbeat": the configured priority peer OR any
 * health-tracked peer. Used by teardown vetoes, session diagnostics, the
 * rekey-in-flight freeze, LRU-evict protection and the reingest sweep — one
 * predicate, so a future criterion change cannot drift across call sites
 * (6 hand-inlined copies had accumulated before it existed).
 * NOTE: distinct from ml_wg_tx_class_pubkey()'s pinned||health prio rule —
 * pinned covers reachability armor (fleet anchor etc.), not heartbeat carriage. */
static bool is_safety_peer(microlink_t * ml, uint32_t vpn_ip)
{
  return (ml->config.priority_peer_ip != 0 && vpn_ip == ml->config.priority_peer_ip) || is_health_tracked(vpn_ip);
}

/* True when ANY safety link exists: the priority peer or at least one
 * registered health peer (machn's bonded remotes / a remote's machine slots).
 * The DERP home-retry ladder keys on this, not on priority_peer_ip alone: a
 * multi-machine remote and every machn have no priority IP set, so their
 * DERP failover path was retried at the calm 60 s cadence while a safety
 * heartbeat depended on it.
 * Called from the DERP task; lock-free like every other reader of
 * s_health_peers (httpd via ml_wg_is_health_tracked, the aggregate-health
 * check below). .ip is an aligned 32-bit word, so a read is never torn; a
 * stale read only picks the other retry cadence for one round. */
bool ml_wg_has_safety_peers(const microlink_t * ml)
{
  if (ml->config.priority_peer_ip != 0) return true;
  for (int i = 0; i < ML_EXTRA_PINS; i++) {
    if (s_health_peers[i].ip != 0) return true;
  }
  return false;
}

/* DERP home region of a peer identified by its 32-byte WG public key.
 * 0 = unknown peer or region not learned. Called from ml_derp_queue_send on the
 * wg_mgr task (the peer-table owner), so this is a same-task read — no lock. */
uint16_t ml_wg_region_for_pubkey(microlink_t * ml, const uint8_t * wg_pubkey)
{
  if (ml == NULL || wg_pubkey == NULL) return 0;
  int idx = find_peer_by_key(ml, wg_pubkey);
  if (idx < 0) return 0;
  return ml->peers[idx].derp_region;
}

/* DERP-egress classification for a destination pubkey, in ONE peer-table walk.
 * Returns the PRIORITY-queue bit: pinned OR health-tracked (their frames never
 * sit behind a disco burst). *mirror_out = heartbeat carriers only (priority OR
 * health-tracked): the fleet pin is reachability armor, not heartbeat carriage,
 * so its frames are not path-diversity mirrored. Safe from the TCPIP thread
 * (wg_derp_output_cb): word-sized reads, worst case a transiently wrong
 * classification, same tolerance as ml_wg_region_for_pubkey. */
bool ml_wg_tx_class_pubkey(microlink_t * ml, const uint8_t * wg_pubkey, bool * mirror_out)
{
  *mirror_out = false;
  if (ml == NULL || wg_pubkey == NULL) return false;
  int idx = find_peer_by_key(ml, wg_pubkey);
  if (idx < 0) return false;
  uint32_t vpn_ip = ml->peers[idx].vpn_ip;
  *mirror_out = is_safety_peer(ml, vpn_ip);
  return *mirror_out || is_pinned_peer(ml, vpn_ip);
}

/* Collect the DISTINCT DERP regions of the safety peers that are exempt from the
 * peer-scaling armor: pinned (incl. priority + fleet + app pins) OR
 * health-tracked. These few peers are the ones the DERP pool must keep an
 * auxiliary connection open for when they home on a non-home region. Writes up
 * to `max` distinct region ids into `out`; returns the count.
 *
 * Concurrency: read from the DERP I/O task while wg_mgr owns/writes the peer
 * table. Reads are word-sized (region ids, active flag) and the worst case of a
 * torn/stale read is a transiently wrong aux region, self-corrected next pass —
 * identical to the existing cross-task diag readers (ml_wg_get_derp_diag). */
int ml_wg_collect_safety_regions(microlink_t * ml, uint16_t * out, int max)
{
  if (ml == NULL || out == NULL || max <= 0) return 0;
  int n = 0;
  for (int i = 0; i < ml->peer_count && n < max; i++) {
    ml_peer_t * p = &ml->peers[i];
    if (!p->active || p->derp_region == 0) continue;
    if (!(is_pinned_peer(ml, p->vpn_ip) || is_health_tracked(p->vpn_ip))) continue;
    bool dup = false;
    for (int k = 0; k < n; k++) {
      if (out[k] == p->derp_region) {
        dup = true;
        break;
      }
    }
    if (!dup) out[n++] = p->derp_region;
  }
  return n;
}

/* Diagnostic: report the DERP region the chip has LEARNED for the management and
 * priority peers (0 = not learned yet). Distinguishes "never learned the server's
 * region -> re-home can't fire" from "learned but re-home/DERP-connect stuck".
 * Exposed via /admin/api/monitor. */
void ml_wg_get_derp_diag(microlink_t * ml, uint16_t * fleet_region, uint16_t * priority_region)
{
  if (fleet_region) {
    *fleet_region = 0;
    uint32_t fip = fleet_server_ip_cached();
    int i = (fip != 0) ? find_peer_by_ip(ml, fip) : -1;
    if (i >= 0) *fleet_region = ml->peers[i].derp_region;
  }
  if (priority_region) {
    *priority_region = 0;
    int i = (ml->config.priority_peer_ip != 0) ? find_peer_by_ip(ml, ml->config.priority_peer_ip) : -1;
    if (i >= 0) *priority_region = ml->peers[i].derp_region;
  }
}

void ml_wg_get_direct_diag(microlink_t * ml, ml_direct_diag_t * out)
{
  if (out == NULL) return;
  memset(out, 0, sizeof(*out));
  out->active_lan_ip = ml_active_lan_ip();
  if (ml == NULL) return;
  out->pp_vpn_ip = ml->config.priority_peer_ip;
  int i = (ml->config.priority_peer_ip != 0) ? find_peer_by_ip(ml, ml->config.priority_peer_ip) : -1;
  if (i < 0) return;
  ml_peer_t * p = &ml->peers[i];
  out->pp_best_ip = p->best_ip;
  out->pp_best_port = p->best_port;
  out->pp_has_direct = p->has_direct_path;
  out->pp_endpoint_count = p->endpoint_count;
  for (int k = 0; k < p->endpoint_count && k < ML_MAX_ENDPOINTS; k++) {
    out->pp_ep_ip[k] = p->endpoints[k].ip;
    out->pp_ep_port[k] = p->endpoints[k].port;
  }
}

/* DERP re-home diagnostics — counters (not logs) so the re-home path is visible
 * on units with no live-log access. Read via /admin/api/monitor. */
static uint32_t s_diag_selfheal_calls; /* self_heal_rehome invocations      */
static uint32_t s_diag_rehome_calls; /* maybe_rehome invocations          */
static uint32_t s_diag_rehome_ret_region0; /* bailed: peer region unknown (0)   */
static uint32_t s_diag_rehome_ret_notpinned; /* bailed: peer not pinned           */
static uint32_t s_diag_rehome_body; /* passed the guards                 */
static uint32_t s_diag_rehome_applied; /* actually changed the home region  */

void ml_wg_get_rehome_diag(uint32_t out[6])
{
  out[0] = s_diag_selfheal_calls;
  out[1] = s_diag_rehome_calls;
  out[2] = s_diag_rehome_ret_region0;
  out[3] = s_diag_rehome_ret_notpinned;
  out[4] = s_diag_rehome_body;
  out[5] = s_diag_rehome_applied;
}

/* Relay-bound direct-path retry counters — counters (not logs) so the retry
 * loop is verifiable on units with no live-log access, mirroring the re-home
 * diag pattern above. Read via /admin/api/monitor. */
static uint32_t s_diag_relay_retries; /* CMM + forced-sweep rounds fired      */
static uint32_t s_diag_direct_regains; /* has_direct_path false -> true edges */
static uint64_t s_last_relay_refetch_ms; /* fleet-wide floor: last coord re-fetch issued for ANY safety peer */
static uint32_t s_diag_relay_refetch_reqs; /* coord re-fetch (reconnect) requests issued for endpoint refresh */
static uint32_t s_diag_relay_refetch_interval_s; /* backoff now gating the most recently re-fetched peer */

uint32_t ml_wg_get_relay_refetch_reqs(void)
{
  return s_diag_relay_refetch_reqs;
}

uint32_t ml_wg_get_relay_refetch_interval_s(void)
{
  return s_diag_relay_refetch_interval_s;
}

static uint32_t s_diag_relay_disco_resets; /* per-peer from-scratch disco resets on a relay-stuck safety peer
                                            * (v2: rate-limited per-peer via p->disco_reset_next_ms) */
static uint32_t s_diag_hs_cand_pings; /* disco pings fanned out to the WG handshake candidate */
static uint32_t s_diag_safety_reconnects; /* wireguardif_connect() on a keyless safety peer regaining direct */
static uint32_t s_diag_ep_learn_evictions; /* learn-from-ping ring-evictions on a full endpoint table —
                                            * nonzero = the B-1 wedge trigger occurred and was absorbed */
static uint32_t s_diag_peer_table_full; /* over-cap add refusals; the LOG is rate-limited (task #60: the
                                         * un-limited warn ran at 147 lines/s at a core-stall, and every
                                         * ESP_LOG line pays the RTC-ring + console-chain tax) */
static uint64_t s_peer_table_full_log_ms; /* last time the warn was actually emitted */

/* Flush-recovery silence-ping state (see disco_silence_ping): PER-PEER pairing
 * slots (review 3793497415 — the single slot lost pairings whenever a flush
 * silenced several safety peers at once: run-46 measured a bogus 72 s "resume"
 * from exactly that overwrite). One slot per safety peer, keyed by peer idx. */
#define SILENCE_PAIR_SLOTS 8

typedef struct
{
  int peer_idx;
  uint64_t ping_ms; /* 0 = slot free (zero-init); nonzero = pairing armed */
} silence_pair_t;

static silence_pair_t s_silence_pairs[SILENCE_PAIR_SLOTS];
static uint32_t s_diag_silence_pings;
static uint32_t s_diag_silence_resume_last_ms;
static uint32_t s_diag_silence_resume_worst_ms;
static uint32_t s_diag_silence_resume_at_s; /* uptime s of the last resume record —
                                             * dates the gauge (boot-window vs live) */

/* DISCO observability counters — the 2026-08-09 regains-oscillation root cause
 * rested on CALCULATED probe-table/CMM dynamics; these measure them instead.
 * Same counters-not-logs pattern as the diag blocks above; read via
 * /admin/api/monitor. */
static uint32_t s_diag_probe_tbl_hw; /* pending_probes active-slot high water since boot */
static uint32_t s_diag_cmm_rx; /* CallMeMaybe messages received since boot        */
static uint32_t s_diag_regains_safety; /* direct regains on SAFETY peers only (priority
                                        * or health-tracked) — s_diag_direct_regains
                                        * also counts bulk tailnet peers, which masked
                                        * whether the SAFETY path was the one flapping */
static uint32_t s_diag_demote_vetoes; /* direct demotes vetoed by fresh direct WG data
                                       * rx (ml_demote_verdict.h) — counts veto-ticks,
                                       * so it climbs ~1/s for the duration of a
                                       * disco-silent-but-data-alive episode */
static uint64_t s_last_demote_veto_log_ms; /* rate-limit the veto log line */

/* Hitless re-ingest counters (run-20 green drop, 2026-08-11): the three WG
 * session-teardown paths (re-key retire, coord REMOVE, cap-evict) were
 * log-only, so the ENOTCONN green-drop forensics could not tell WHICH fired.
 * Counters-not-logs, read via /admin/api/monitor. The *_vetoes counters mark
 * teardowns of an ACTIVELY-USED safety session that were deferred instead
 * (ml_teardown_veto): nonzero = the guard saved a live safety bond. */
static uint32_t s_diag_rekey_retires; /* stale-entry retires on a key change    */
static uint32_t s_diag_rekey_retire_vetoes; /* ... vetoed: session still live   */
static uint32_t s_diag_peer_removes; /* coord ML_PEER_REMOVE teardowns applied  */
static uint32_t s_diag_remove_vetoes; /* ... vetoed: session still live         */
static uint32_t s_diag_evict_safety_skips; /* LRU evict skipped a safety peer   */

void ml_wg_get_reingest_diag(uint32_t out[6])
{
  out[0] = s_diag_rekey_retires;
  out[1] = s_diag_rekey_retire_vetoes;
  out[2] = s_diag_peer_removes;
  out[3] = s_diag_remove_vetoes;
  out[4] = s_diag_evict_safety_skips;
  out[5] = s_diag_relay_disco_resets; /* from-scratch disco resets on a relay-stuck safety peer (@claude review) */
}

/* WG session-health diag (run-20/21 ENOTCONN forensics): learn-evictions +
 * the WORST safety-peer keypair/init ages. wg_kp_age_max steadily ~<120000
 * (rekey cadence) = healthy; climbing past 120000 = a rekey is starving; a
 * green drop then follows ~60 s later when REJECT_AFTER_TIME kills the key. */
uint32_t ml_wg_get_hs_cand_pings(void)
{
  return s_diag_hs_cand_pings;
}

uint32_t ml_wg_get_safety_reconnects(void)
{
  return s_diag_safety_reconnects;
}

void ml_wg_get_session_diag(microlink_t * ml, uint32_t out[7])
{
  out[0] = s_diag_ep_learn_evictions;
  out[1] = 0; /* max safety keypair age ms (0xFFFFFFFF = a peer has NO valid key) */
  out[2] = 0; /* max safety handshake-init TX age ms */
  out[3] = 0; /* max safety worst any-path rx gap ms (edge-flush receive-stall metric) */
  out[4] = 0; /* WHEN out[3]'s max was recorded (sys_now ms) — dates the gauge */
  out[5] = 0; /* max safety worst tx gap ms (replier-silence half of a flush) */
  out[6] = 0; /* WHEN out[5]'s max was recorded */
  if (ml == NULL || ml->wg_netif == NULL) return;
  for (int i = 0; i < ml->peer_count; i++) {
    ml_peer_t * p = &ml->peers[i];
    if (!p->active || p->wg_peer_index < 0) continue;
    bool safety = is_safety_peer(ml, p->vpn_ip);
    if (!safety) continue;
    u32_t kp_age = 0, init_age = 0;
    if (
      wireguardif_peer_handshake_age((struct netif *)ml->wg_netif, (u8_t)p->wg_peer_index, &kp_age, &init_age) ==
      ERR_OK)
    {
      if (kp_age > out[1]) out[1] = kp_age;
      if (init_age != 0xFFFFFFFFu && init_age > out[2]) out[2] = init_age;
    }
    u32_t rx_worst = 0;
    u32_t rx_worst_at = 0;
    if (
      wireguardif_peer_worst_rx_gap((struct netif *)ml->wg_netif, (u8_t)p->wg_peer_index, &rx_worst, &rx_worst_at) ==
        ERR_OK &&
      rx_worst > out[3])
    {
      out[3] = rx_worst;
      out[4] = rx_worst_at;
    }
    u32_t tx_worst = 0;
    u32_t tx_worst_at = 0;
    if (
      wireguardif_peer_worst_tx_gap((struct netif *)ml->wg_netif, (u8_t)p->wg_peer_index, &tx_worst, &tx_worst_at) ==
        ERR_OK &&
      tx_worst > out[5])
    {
      out[5] = tx_worst;
      out[6] = tx_worst_at;
    }
  }
}

/* True when tearing down this peer's WG session must be deferred: it is a
 * SAFETY peer (priority/health-tracked) and its session shows authenticated
 * data rx within ML_TEARDOWN_RX_FRESH_MS — i.e. the 5 Hz safety heartbeat is
 * flowing RIGHT NOW and a wireguardif_remove_peer would fail those sends
 * ENOTCONN until a fresh handshake (>2 s = machine STOP). See
 * ml_demote_verdict.h for the invariant argument. */
static bool teardown_vetoed(microlink_t * ml, uint32_t vpn_ip, int wg_peer_index)
{
  bool is_safety = is_safety_peer(ml, vpn_ip);
  u32_t age_ms = 0;
  bool valid = ml->wg_netif && wg_peer_index >= 0 &&
               wireguardif_peer_rx_age((struct netif *)ml->wg_netif, (u8_t)wg_peer_index, &age_ms) == ERR_OK;
  return ml_teardown_veto(is_safety, valid, age_ms, ML_TEARDOWN_RX_FRESH_MS);
}

void ml_wg_get_disco_obs_diag(uint32_t out[4])
{
  out[0] = s_diag_probe_tbl_hw;
  out[1] = s_diag_cmm_rx;
  out[2] = s_diag_regains_safety;
  out[3] = s_diag_demote_vetoes;
}

void ml_wg_get_direct_retry_diag(microlink_t * ml, uint32_t out[4])
{
  out[0] = s_diag_relay_retries;
  out[1] = s_diag_direct_regains;
  out[2] = 0;
  out[3] = 0;
  if (ml == NULL) return;
  /* Report the relay-bound safety peers and the earliest armed retry due
   * time, so a bench run can verify the retry ARMED without waiting out the
   * backoff (2026-08-09 falsification: rounds==0 alone cannot distinguish
   * "retry never armed" from "first round simply not due yet"). */
  uint64_t now = ml_get_time_ms();
  uint64_t soonest = 0;
  for (int i = 0; i < ml->peer_count; i++) {
    ml_peer_t * p = &ml->peers[i];
    if (!p->active || p->has_direct_path) continue;
    bool safety = is_safety_peer(ml, p->vpn_ip);
    if (!safety) continue;
    out[2]++;
    if (p->relay_retry_next_ms != 0 && (soonest == 0 || p->relay_retry_next_ms < soonest)) {
      soonest = p->relay_retry_next_ms;
    }
  }
  if (soonest > now) {
    out[3] = (uint32_t)(soonest - now);
  }
}

/* ============================================================================
 * DERP region auto-negotiation — decision side (design §4.2/§6/§8).
 *
 * WHAT CHANGED vs the pre-autoneg code: maybe_rehome_to_priority() used to key
 * the target on the single static config.priority_peer_ip and apply EVERY
 * change break-before-make (derp_home_region write + ML_EVT_DERP_RECONNECT,
 * gapping the relay path for a full TLS handshake). It now (a) derives the
 * target from the app's machine-slot table via the §4.2 primary rule when a
 * callback is registered (Q1: lowest bonded+ARMED slot — deterministic across
 * reboots, unlike arming history), (b) consults TTL/epoch-gated fleet advice
 * ONLY when no machine is configured (§6 — machines and idle remotes), and
 * (c) routes a change through the §7 make-before-break machine whenever a live
 * safety bond exists, under mandatory §8 damping.
 *
 * WHAT STAYED: the pinned-peer guard + diag counters; the management-server
 * anchor fallback ("manageable when no machine online", §4.2); the LOCK path
 * (derp_region_override != 0 preserves today's behavior verbatim — I2); and
 * the no-bond legacy immediate rehome (§6 legacy_rehome — cold-bond must stay
 * fast). All state below is RAM-only: the lock remains the only NVS-persisted
 * region control.
 * ========================================================================== */

/* §8 damping + Phase-3 advice bookkeeping. Owned by the wg_mgr task (the only
 * negotiator writer); exposed cross-task via ml_wg_get_neg_diag (word reads). */
static uint32_t s_neg_damping_suppressed; /* §16: passes suppressed by any §8 guard */
static uint32_t s_neg_cooldown_trips; /* §16: hourly circuit-breaker trips */
static uint64_t s_neg_commit_ring[ML_NEG_MAX_SWITCHES_PER_HOUR]; /* commit timestamps */
static uint16_t s_neg_candidate; /* §8 stability window: current target candidate */
static uint64_t s_neg_candidate_since_ms;
static uint64_t s_neg_last_commit_ms;
static bool s_neg_cooldown_logged;

static struct
{
  uint16_t region;
  uint64_t until_ms;
} s_neg_ban[ML_NEG_REGION_BANS]; /* §8 bad-region cooldown after ROLLBACK */

static uint8_t s_neg_pending_source; /* MICROLINK_REGION_SRC_* of the pending MBB request */
static uint32_t s_neg_advice_applied_epoch; /* last fleet-advice epoch actually applied */
static uint64_t s_neg_last_advice_apply_ms;

static bool neg_region_banned(uint16_t region, uint64_t now)
{
  for (int i = 0; i < ML_NEG_REGION_BANS; i++) {
    if (s_neg_ban[i].region == region && now < s_neg_ban[i].until_ms) return true;
  }
  return false;
}

static void neg_ban_region(uint16_t region, uint64_t now)
{
  int slot = 0;
  for (int i = 0; i < ML_NEG_REGION_BANS; i++) {
    if (s_neg_ban[i].region == region || now >= s_neg_ban[i].until_ms) {
      slot = i;
      break;
    }
  }
  s_neg_ban[slot].region = region;
  s_neg_ban[slot].until_ms = now + ML_NEG_REGION_BAN_MS;
}

static uint32_t neg_switches_last_hour(uint64_t now)
{
  uint32_t n = 0;
  for (int i = 0; i < ML_NEG_MAX_SWITCHES_PER_HOUR; i++) {
    if (s_neg_commit_ring[i] != 0 && (now - s_neg_commit_ring[i]) < 3600000ull) n++;
  }
  return n;
}

static void neg_note_commit(uint64_t now)
{
  /* Overwrite the OLDEST entry — with a ring sized == the hourly cap, the cap
   * check above guarantees a free (aged-out) slot exists whenever we commit. */
  int oldest = 0;
  for (int i = 1; i < ML_NEG_MAX_SWITCHES_PER_HOUR; i++) {
    if (s_neg_commit_ring[i] < s_neg_commit_ring[oldest]) oldest = i;
  }
  s_neg_commit_ring[oldest] = now;
  s_neg_last_commit_ms = now;
}

void ml_wg_get_neg_diag(uint32_t out[3])
{
  out[0] = s_neg_damping_suppressed;
  out[1] = s_neg_cooldown_trips;
  out[2] = neg_switches_last_hour(ml_get_time_ms());
}

/* §6 live_bond_active(): any health-tracked safety peer currently healthy.
 * The remote comparator feeds per-machine-slot health every tick and machn
 * feeds per-remote health, so this is a faithful bond signal on both roles.
 * Builds that never health-track (no pstop app) read false => they keep the
 * legacy immediate-rehome path exactly as today. */
bool ml_wg_live_bond_active(void)
{
  for (int i = 0; i < ML_EXTRA_PINS; i++) {
    if (s_health_peers[i].ip != 0 && s_health_peers[i].healthy) return true;
  }
  return false;
}

/* §4.2 primary-machine selection. Returns the VPN IP whose region the chip
 * should home on, 0 = none known. Rules (Q1 decided 2026-08-10):
 *   1/2. the lowest-index bonded+ARMED machine slot (the callback reports it —
 *        dcs owns slots + arming; slot order is NVS config, identical after
 *        power loss, unlike first-armed order);
 *   3.   none armed -> lowest CONFIGURED slot whose region we already learned
 *        (checked here — the app can't know regions);
 *   4.   legacy static priority_peer_ip config (unchanged when no callback is
 *        registered, i.e. machines and non-dcs builds behave as today). */
static uint32_t neg_primary_ip(microlink_t * ml)
{
  microlink_primary_machine_cb_t cb = ml->primary_cb;
  if (cb != NULL) {
    microlink_primary_machine_info_t info;
    memset(&info, 0, sizeof(info));
    cb(ml->primary_cb_ctx, &info);
    if (info.armed_primary_ip != 0) {
      return info.armed_primary_ip;
    }
    for (int i = 0; i < info.configured_count && i < MICROLINK_PRIMARY_MAX_MACHINES; i++) {
      uint32_t ip = info.configured_ips[i];
      int idx = (ip != 0) ? find_peer_by_ip(ml, ip) : -1;
      if (idx >= 0 && ml->peers[idx].derp_region != 0) {
        return ip;
      }
    }
    if (info.configured_count > 0) {
      /* Machines are configured but none armed and no region learned yet:
       * HOLD (self-heal retries in 3 s once the netmap delivers a region)
       * rather than hopping onto some other peer's region meanwhile. */
      return 0;
    }
  }
  return ml->config.priority_peer_ip;
}

/* True when the chip has ANY machine configured — such a chip must ignore
 * fleet advice entirely (§6: the netmap is fresher and machine-authoritative). */
static bool neg_machine_configured(microlink_t * ml)
{
  microlink_primary_machine_cb_t cb = ml->primary_cb;
  if (cb != NULL) {
    microlink_primary_machine_info_t info;
    memset(&info, 0, sizeof(info));
    cb(ml->primary_cb_ctx, &info);
    return info.configured_count > 0 || info.armed_primary_ip != 0;
  }
  return ml->config.priority_peer_ip != 0;
}

/* Fleet advice region if it may drive the target right now, else 0. An
 * ALREADY-APPLIED epoch keeps supplying its region until TTL expiry (so the
 * management-anchor fallback can't fight a committed advice); a NEW epoch is
 * additionally rate-limited to one apply per ML_NEG_ADVICE_MIN_INTERVAL_MS —
 * chip-side, so even a flapping fleet cannot exceed it (I3/§8). */
static uint16_t neg_advice_target(microlink_t * ml, uint64_t now)
{
  uint16_t region = ml->advice_region;
  uint32_t expires_s = ml->advice_expires_s;
  if (region == 0 || expires_s == 0) return 0;
  if ((uint32_t)(now / 1000u) >= expires_s) return 0; /* TTL expired (I3) */
  if (
    ml->advice_epoch != s_neg_advice_applied_epoch && s_neg_last_advice_apply_ms != 0 &&
    (now - s_neg_last_advice_apply_ms) < ML_NEG_ADVICE_MIN_INTERVAL_MS)
  {
    return 0; /* new advice, honored at most every 30 min */
  }
  return region;
}

/* §6 target selection (normative pseudocode in the design):
 *   target = region(primary_machine())            — §4.2
 *   if 0:  fleet advice, ONLY with no machine configured (machines/idle chips)
 *   if 0:  management-server anchor when the invoking peer IS the fleet server
 *          (kept verbatim from the pre-autoneg fallback chain, §4.2)
 *   if 0:  no local choice — today's server-HomeDERP default path stays. */
static uint16_t neg_target_region(microlink_t * ml, const ml_peer_t * p, uint8_t * src_out)
{
  uint64_t now = ml_get_time_ms();
  uint32_t prim = neg_primary_ip(ml);
  if (prim != 0) {
    int idx = find_peer_by_ip(ml, prim);
    if (idx >= 0 && ml->peers[idx].derp_region != 0) {
      *src_out = MICROLINK_REGION_SRC_AUTO_PRIMARY;
      return ml->peers[idx].derp_region;
    }
    /* Primary known but its region not learned yet: fall through to the
     * anchor/advice chain (matches the old fallback shape) — the self-heal
     * cadence re-evaluates once the region arrives. */
  }
  if (!neg_machine_configured(ml)) {
    uint16_t a = neg_advice_target(ml, now);
    if (a != 0) {
      *src_out = MICROLINK_REGION_SRC_AUTO_FLEET;
      return a;
    }
  }
  if (p != NULL) {
    uint32_t fip = fleet_server_ip_cached();
    if (fip != 0 && p->vpn_ip == fip && p->derp_region != 0) {
      /* Management anchor: keeps the chip manageable when no machine is
       * online. Reported as plain "auto" — no machine/advice selection. */
      *src_out = MICROLINK_REGION_SRC_AUTO;
      return p->derp_region;
    }
  }
  return 0;
}

/* Cancel any pending MBB request (lock landed, bond died, target changed).
 * The executor observes the generation bump and aborts to IDLE (§7). */
static void neg_cancel_mbb(microlink_t * ml)
{
  if (ml->mbb_target_region != 0) {
    ml->mbb_target_region = 0;
    ml->mbb_generation++;
  }
}

/* Q2 surfacing: record an auto-applied region change (legacy rehome or MBB
 * commit) for /state.json, the UI badge and the fleet check-in. */
static void neg_note_auto_apply(microlink_t * ml, uint16_t region, uint8_t src, uint64_t now)
{
  ml->derp_region_src = src;
  ml->derp_region_auto_applied = region;
  ml->derp_region_auto_applies++;
  ml->derp_region_auto_apply_s = (uint32_t)(now / 1000u);
}

/* Apply a computed target region (§6 tail). Three paths:
 *   LOCK      — preserve today's behavior verbatim (I2): assert the advert
 *               owner + reconnect; connect/advert use the override anyway.
 *   no bond   — legacy immediate rehome (§6 legacy_rehome): correct and FASTER
 *               than MBB for boot/cold recovery; behavior identical to today.
 *   live bond — §7 MBB only (I1: the bond is never dropped by a switch),
 *               gated by every §8 damping guard. */
/* True while any safety peer's WG session is missing its keypair or a rekey
 * is overdue with initiations actively firing. A region switch in that window
 * re-routes the DERP leg the handshake needs (silent home-conn fallback +
 * old-home reap, audit §1c) — the second-transition trigger behind both
 * run-20/21 green drops (dwell expiry at T+10min, keypair death at T+~14min).
 * Freezing the negotiator here costs only switch latency, never safety. */
static bool safety_rekey_inflight(microlink_t * ml)
{
  if (!ml->wg_netif) return false;
  for (int i = 0; i < ml->peer_count; i++) {
    ml_peer_t * p = &ml->peers[i];
    if (!p->active || p->wg_peer_index < 0) continue;
    bool safety = is_safety_peer(ml, p->vpn_ip);
    if (!safety) continue;
    u32_t kp_age = 0, init_age = 0;
    if (
      wireguardif_peer_handshake_age((struct netif *)ml->wg_netif, (u8_t)p->wg_peer_index, &kp_age, &init_age) !=
      ERR_OK)
    {
      continue;
    }
    if (kp_age == 0xFFFFFFFFu) {
      /* No valid keypair: freeze only if we're actively trying to handshake
       * (a never-connected passive peer must not pin the negotiator). */
      if (init_age != 0xFFFFFFFFu && init_age < 30000u) return true;
      continue;
    }
    /* Keypair older than REKEY_AFTER_TIME (120 s, wireguard.h) with a recent
     * initiation = a rekey is in flight and not completing. */
    if (kp_age > 120000u && init_age < 30000u) return true;
  }
  return false;
}

static void neg_apply_target(microlink_t * ml, uint16_t target, uint8_t src)
{
  uint64_t now = ml_get_time_ms();

  if (ml->derp_region_override != 0) {
    ml->priority_peer_region = target; /* advertised as PreferredDERP (override still wins) */
    /* Pin->MBB: pin convergence is owned by neg_pin_tick — gapless MBB while
     * the home conn is alive, the DERP task's own home-reconnect (straight to
     * the override) when it is not; a teardown here would starve heartbeat rx
     * (docs/STAGE1_PIN_MBB_DESIGN.md). Cancel only a FOREIGN in-flight MBB
     * (autoneg toward some other region — the I2 "lock wins instantly"
     * intent); NEVER the pin's own, or the pin could never complete (this
     * runs every 3 s). */
    if (ml->mbb_target_region != 0 && ml->mbb_target_region != ml->derp_region_override) {
      neg_cancel_mbb(ml);
    }
    return;
  }

  if (ml->derp_home_region == target) {
    /* Fixed point: keep asserting the advert owner (as the old code did) and
     * make sure no stale MBB request lingers. The Q2 surfacing fields track
     * the CURRENT auto-selected region/owner (no counter bump — nothing was
     * applied), so /state.json + the badge stay truthful in steady state. */
    ml->priority_peer_region = target;
    if (src != MICROLINK_REGION_SRC_AUTO) {
      ml->derp_region_src = src; /* ownership label follows the current driver */
      ml->derp_region_auto_applied = target;
    }
    s_neg_candidate = 0;
    neg_cancel_mbb(ml);
    return;
  }

  if (!ml_wg_live_bond_active()) {
    neg_cancel_mbb(ml); /* the immediate rehome supersedes any in-flight MBB */
    ml->priority_peer_region = target;
    s_diag_rehome_applied++;
    ESP_LOGW(
      TAG,
      "Re-homing DERP region %u -> %u (%s; no live bond: legacy immediate reconnect)",
      (unsigned)ml->derp_home_region,
      (unsigned)target,
      microlink_region_source_str(src));
    ml->derp_home_region = target;
    ml_derp_note_reconnect_cause(4); /* cause 4 = region rehome (legacy immediate path) */
    xEventGroupSetBits(ml->events, ML_EVT_DERP_RECONNECT);
    neg_note_auto_apply(ml, target, src, now);
    if (src == MICROLINK_REGION_SRC_AUTO_FLEET) {
      s_neg_advice_applied_epoch = ml->advice_epoch;
      s_neg_last_advice_apply_ms = now;
      /* Q2: an advice apply must be visible to peers + operator immediately —
       * push the new PreferredDERP now instead of waiting for the next
       * periodic MapRequest. */
      (void)microlink_request_announce(ml);
    }
    return;
  }

  /* ---- live bond: §8 damping gates, then request the §7 MBB switch ---- */
  if (neg_region_banned(target, now)) {
    s_neg_damping_suppressed++;
    return;
  }
  if (safety_rekey_inflight(ml)) {
    /* Never start a region transition while a safety session's handshake is
     * struggling — the switch would re-route the very DERP leg the rekey
     * needs (run-20/21 trigger). Re-evaluated next tick; costs latency only. */
    s_neg_damping_suppressed++;
    return;
  }
  if (s_neg_last_commit_ms != 0 && (now - s_neg_last_commit_ms) < ML_NEG_MIN_DWELL_MS) {
    s_neg_damping_suppressed++;
    return;
  }
  if (s_neg_candidate != target) {
    /* New candidate: (re)start the stability window and preempt any MBB
     * toward a stale target (§7: newer target restarts from IDLE via ABORT). */
    s_neg_candidate = target;
    s_neg_candidate_since_ms = now;
    if (ml->mbb_target_region != 0 && ml->mbb_target_region != target) {
      neg_cancel_mbb(ml);
    }
    return;
  }
  if ((now - s_neg_candidate_since_ms) < ML_NEG_STABILITY_MS) {
    return; /* §8: absorbs netmap patch bursts / region flap without churn */
  }
  if (neg_switches_last_hour(now) >= ML_NEG_MAX_SWITCHES_PER_HOUR) {
    if (!s_neg_cooldown_logged) {
      s_neg_cooldown_trips++;
      s_neg_cooldown_logged = true;
      ESP_LOGE(
        TAG,
        "DERP region switch circuit-breaker TRIPPED (%d switches/h): holding home region %u, wanted %u",
        ML_NEG_MAX_SWITCHES_PER_HOUR,
        (unsigned)ml->derp_home_region,
        (unsigned)target);
    }
    s_neg_damping_suppressed++;
    return;
  }
  s_neg_cooldown_logged = false;
  if (ml->mbb_target_region == target) {
    return; /* already requested; the executor is working on it */
  }
  s_neg_pending_source = src;
  ml->mbb_target_region = target;
  ml->mbb_generation++;
  ESP_LOGW(
    TAG,
    "MBB home switch requested: region %u -> %u (%s; bond live, make-before-break)",
    (unsigned)ml->derp_home_region,
    (unsigned)target,
    microlink_region_source_str(src));
}

/* ============================================================================
 * Stage-1 pin->MBB (docs/STAGE1_PIN_MBB_DESIGN.md): drive the operator region
 * pin (derp_region_override) GAPLESSLY. While the home conn is alive, the pin
 * is applied via the §7 make-before-break executor (open target as aux, prove,
 * swap the home index — no teardown, no rx gap). With no live home there is
 * nothing to protect: the DERP task's own home-reconnect path already connects
 * straight to ml_effective_home_region() == the override.
 *
 * Fallback semantics (operator decision 2026-08-13): RETRY FOREVER, NEVER GAP.
 * A pin toward an unprovable region keeps the old (working) home serving and
 * retries with 5 s -> 15 s -> 60 s backoff (60 s cap, RAM-only) — a pin is a
 * command, not advice, so rollbacks neither ban the region nor give up. The
 * unfulfilled pin is visible as pin_pending in /api/status.
 * State + counters owned by the wg_mgr task (single writer); counters read
 * cross-task via ml_wg_get_pin_diag (word reads). */
static struct
{
  uint32_t mbb_requests; /* MBB commands issued for the pin (cumulative) */
  uint32_t mbb_commits; /* pin MBBs that committed (cumulative) */
  uint32_t mbb_retries; /* re-issues after a failed prove (cumulative) */
  uint64_t retry_at_ms; /* 0 = no backoff pending */
  uint32_t backoff_ms; /* current backoff step */
  uint16_t last_target; /* region of the pin MBB we issued (edge 4: cancel-on-clear) */
  uint32_t absent_resyncs; /* coord full-resyncs forced by an absent pinned peer (cumulative) */
  uint32_t absent_nvs_restores; /* absent pins re-synthesized from the NVS peer cache */
  uint64_t absent_next_ms; /* pin-presence heal backoff gate */
  uint32_t absent_backoff_ms;
} s_pin; /* never bulk-reset: counters are cumulative, reset sites clear differing subsets */

/* Stage-0b gauge (run-29 disarm class #4/#10): worst single wg_mgr loop
 * iteration — heartbeats ride THIS task (WG rx -> decrypt -> pstop), so a
 * multi-second stall here gaps every remote simultaneously with the DERP
 * task innocent. Owned by wg_mgr; word-sized cross-task read. */
static uint32_t s_diag_wg_max_iter_ms;

uint32_t ml_wg_get_max_iter_ms(void)
{
  return s_diag_wg_max_iter_ms;
}

void ml_wg_get_pin_diag(uint32_t out[6])
{
  out[0] = s_pin.mbb_requests;
  out[1] = s_pin.mbb_commits;
  out[2] = s_pin.mbb_retries;
  out[3] = (s_pin.retry_at_ms != 0) ? 1u : 0u; /* backoff currently pending */
  out[4] = s_pin.absent_resyncs; /* forced coord resyncs for a pinned-but-absent peer */
  out[5] = s_pin.absent_nvs_restores; /* absent pins restored from the NVS cache */
}

/* Pin-presence self-heal: an extra-pinned IP
 * (a configured pstop machine / fleet anchor) that is ABSENT from the peer
 * table can never be reached — and with OmitPeers the control plane will not
 * re-send it unprompted, so the outage is PERMANENT until a lucky reboot.
 * How it happens: the initial full-netmap ingest can race ahead of the app's
 * boot-time pstop_slot_pins_sync(); on an over-cap tailnet the machine is
 * then dropped UN-pinned ("Peer table full, cannot add") and no later patch
 * re-delivers it. Heal: detect pinned-but-absent on the 3 s cadence and kick
 * ML_CMD_FORCE_RECONNECT (re-register -> full FETCH_PEERS re-ingests the map;
 * by then the pin is registered, so admission LRU-evicts a non-pinned peer).
 * Escalating backoff 60 s -> 10 min cap: a reconnect is heavier than an
 * announce, and a misconfigured (never-on-tailnet) machine IP must not storm
 * control — it stays visible via the counter + log instead. (Statics live
 * with the other pin counters above, ahead of ml_wg_get_pin_diag.) */
static void pin_presence_heal(microlink_t * ml)
{
  if (!(xEventGroupGetBits(ml->events) & ML_EVT_COORD_REGISTERED)) {
    return; /* boot/reconnect grace: the full map may still be ingesting */
  }
  uint32_t absent_ip = 0;
  for (int i = 0; i < ML_EXTRA_PINS; i++) {
    uint32_t ip = s_extra_pins[i];
    if (ip != 0 && find_peer_by_ip(ml, ip) < 0) {
      absent_ip = ip;
      break;
    }
  }
  uint64_t now = ml_get_time_ms();
  if (absent_ip == 0) {
    s_pin.absent_backoff_ms = 0; /* healthy — reset the backoff ladder */
    s_pin.absent_next_ms = 0; /* and the gate, so a re-absence heals immediately */
    return;
  }
  if (s_pin.absent_next_ms != 0 && now < s_pin.absent_next_ms) {
    return;
  }
  s_pin.absent_backoff_ms =
    (s_pin.absent_backoff_ms == 0) ? 60000 : (s_pin.absent_backoff_ms >= 300000 ? 600000 : s_pin.absent_backoff_ms * 5);
  s_pin.absent_next_ms = now + s_pin.absent_backoff_ms;
  char ipstr[16];
  microlink_ip_to_str(absent_ip, ipstr);

  /* First choice: re-synthesize the peer from the NVS cache (key + disco key +
   * endpoints survive there). The coord-resync fallback below is empirically
   * insufficient: with OmitPeers the re-fetch does not re-deliver a peer the
   * server believes we hold (f498 reproducer, 2026-08-16: absent_resyncs
   * climbing while errno-118 route-fails persisted). A stale cached key is
   * self-correcting — the next coord update rekey-retires it. We run on the
   * wg_mgr task, so calling add_peer directly is single-writer-safe. */
  ml_peer_update_t cached;
  bool have_cached = ml_peer_nvs_lookup_update(absent_ip, &cached);
  if (have_cached) {
    bool skipped = false;
    uint64_t a0 = ml_get_time_ms();
    int aidx = add_peer(ml, &cached, &skipped);
    /* Attribute this out-of-ingest add to the pass gauges — a stall event
     * must never carry unattributed restore work (stall-decomposition rule). */
    uint32_t am = (uint32_t)s_pass_ingest_ms + (uint32_t)(ml_get_time_ms() - a0);
    s_pass_ingest_ms = (am > 0xFFFF) ? 0xFFFF : (uint16_t)am;
    if (aidx >= 0) {
      s_pass_peer_adds++;
      s_pin.absent_nvs_restores++;
      ESP_LOGW(
        TAG, "Pinned peer %s ABSENT — restored from NVS cache (#%u)", ipstr, (unsigned)s_pin.absent_nvs_restores);
      return;
    }
  }

  s_pin.absent_resyncs++;
  ESP_LOGW(
    TAG,
    "Pinned peer %s ABSENT (%s) — forcing FULL coord resync #%u (next retry in %us)",
    ipstr,
    have_cached ? "NVS cache entry found but add failed" : "no NVS cache entry",
    (unsigned)s_pin.absent_resyncs,
    (unsigned)(s_pin.absent_backoff_ms / 1000));
  ml_coord_request_full_peers(); /* the default OmitPeers=true reconnect never
                                  * re-delivers the missing peer (f498 evidence) */
  ml_coord_cmd_t cmd = ML_CMD_FORCE_RECONNECT;
  (void)xQueueSend(ml->coord_cmd_queue, &cmd, 0); /* full = one already pending */
}

static void neg_pin_tick(microlink_t * ml)
{
  uint16_t pin = ml->derp_region_override;
  if (pin == 0) {
    /* Edge 4: pin cleared while its own MBB is in flight — cancel it (the
     * generation bump aborts the executor back to IDLE, no ban). Autoneg
     * resumes ownership on its own cadence. */
    if (s_pin.last_target != 0 && ml->mbb_target_region == s_pin.last_target) {
      neg_cancel_mbb(ml);
    }
    s_pin.last_target = 0;
    s_pin.retry_at_ms = 0;
    s_pin.backoff_ms = 0;
    return;
  }
  /* Cross-task read of the DERP-task-owned home conn: volatile word reads. A
   * torn/stale read is conservative — worst case we wait one 3 s tick. */
  ml_derp_conn_t * home = &ml->derp[ml->derp_home_slot];
  bool home_alive = home->connected;
  if (pin != s_pin.last_target) {
    /* Operator re-pinned to a DIFFERENT region: the old target's backoff must
     * not delay the new command. */
    s_pin.retry_at_ms = 0;
    s_pin.backoff_ms = 0;
  }
  if (home_alive && home->region_id == pin) {
    s_pin.retry_at_ms = 0; /* pin satisfied — clear any backoff */
    s_pin.backoff_ms = 0;
    return;
  }
  if (!home_alive) {
    /* No live home = no gap to protect. The DERP I/O task's home-reconnect
     * path connects to ml_effective_home_region() (= the override) on its
     * own; issuing an MBB here would just race it. Nothing to do. */
    return;
  }
  uint64_t now = ml_get_time_ms();
  if (s_pin.retry_at_ms != 0 && now < s_pin.retry_at_ms) {
    return; /* backing off after a failed prove */
  }
  if (ml->mbb_target_region == pin) {
    return; /* already in flight toward the pin — let the executor work */
  }
  /* Issue the MBB command (same single-writer interface autoneg uses). The
   * §8 damping/ban guards are deliberately NOT consulted: an operator pin is
   * a command; the mbb_target dedupe above is the only rate limit needed. */
  s_neg_pending_source = MICROLINK_REGION_SRC_LOCKED;
  s_pin.retry_at_ms = 0; /* leaving backoff: the re-issued MBB is in flight, not waiting —
                          * keeps pin_backoff_pending telemetry truthful */
  ml->mbb_target_region = pin;
  ml->mbb_generation++;
  s_pin.last_target = pin;
  s_pin.mbb_requests++;
  ESP_LOGW(
    TAG,
    "PIN via MBB: home region %u -> %u (gapless; old home serves until the new conn proves)",
    (unsigned)home->region_id,
    (unsigned)pin);
}

/* Consume the MBB executor's outcome (posted by the DERP I/O task). Runs on
 * the wg_mgr 3 s self-heal cadence — the advert/announce stays single-writer
 * (this task), off the safety send path. */
static void neg_consume_mbb_outcome(microlink_t * ml)
{
  uint8_t oc = ml->mbb_outcome;
  if (oc == ML_MBB_OUTCOME_NONE) return;
  uint16_t region = ml->mbb_outcome_region;
  ml->mbb_outcome = ML_MBB_OUTCOME_NONE;
  neg_cancel_mbb(ml); /* command served either way; executor is back at IDLE */
  uint64_t now = ml_get_time_ms();

  if (oc == ML_MBB_OUTCOME_COMMITTED) {
    bool pin_commit = (ml->derp_region_override != 0 && region == ml->derp_region_override);
    if (pin_commit) {
      s_pin.mbb_commits++; /* Stage-1: the pin landed gaplessly */
      s_pin.retry_at_ms = 0;
      s_pin.backoff_ms = 0;
    }
    /* The commit ring feeds AUTONEG's switches/hour circuit breaker — operator
     * pin commits must not count against it, or a few pins in an hour suppress
     * legitimate autoneg switching for up to an hour after unlock. The advert
     * tail below is still wanted for pins. */
    if (!pin_commit) {
      neg_note_commit(now);
    }
    /* §6/§7 SWITCH_ADVERT tail: an MBB-committed region is treated exactly
     * like priority_peer_region — it owns the PreferredDERP advert and arms
     * the MapResponse authoritative guard so the server can't revert it. */
    ml->priority_peer_region = region;
    s_diag_rehome_applied++;
    neg_note_auto_apply(ml, region, s_neg_pending_source, now);
    if (s_neg_pending_source == MICROLINK_REGION_SRC_AUTO_FLEET) {
      s_neg_advice_applied_epoch = ml->advice_epoch;
      s_neg_last_advice_apply_ms = now;
    }
    /* Live PreferredDERP re-advert — the shipped lock plumbing propagates it;
     * peers migrate to the new region while the OLD conn is still up (§7
     * DRAIN_OLD holds it via the want-set until they do). */
    (void)microlink_request_announce(ml);
    ESP_LOGW(
      TAG,
      "MBB COMMIT: DERP home region now %u (%s); PreferredDERP re-advert queued, old region drains via want-set",
      (unsigned)region,
      microlink_region_source_str(s_neg_pending_source));
  } else if (oc == ML_MBB_OUTCOME_ROLLED_BACK) {
    if (ml->derp_region_override != 0 && region == ml->derp_region_override) {
      /* Stage-1 retry-forever: a pin is a command, not advice — no region ban,
       * no give-up. Back off 5 s -> 15 s -> 60 s (cap) and re-issue; the old
       * (working) home keeps serving throughout, so green is never at risk.
       * The unfulfilled pin is visible as pin_pending in /api/status. */
      s_pin.backoff_ms = (s_pin.backoff_ms == 0) ? 5000 : (s_pin.backoff_ms == 5000 ? 15000 : 60000);
      s_pin.retry_at_ms = now + s_pin.backoff_ms;
      s_pin.mbb_retries++;
      s_neg_candidate = 0;
      ESP_LOGW(
        TAG,
        "PIN MBB ROLLBACK: region %u failed proving — retrying in %us (no ban; old home keeps serving)",
        (unsigned)region,
        (unsigned)(s_pin.backoff_ms / 1000));
      return;
    }
    neg_ban_region(region, now); /* §8: 15-min cooldown before retrying an unprovable region */
    s_neg_candidate = 0; /* restart the stability window from scratch */
    ESP_LOGW(
      TAG,
      "MBB ROLLBACK: region %u failed proving — banned %d min, home untouched (bond never at risk)",
      (unsigned)region,
      (int)(ML_NEG_REGION_BAN_MS / 60000));
  } else {
    /* ABORTED (lock landed / preemption): no ban — nothing was proven bad. */
    s_neg_candidate = 0;
  }
}

/* Home our DERP connection on a pinned peer's region.
 * microlink's HOME DERP connection is where peers reach us, and a Tailscale
 * DERP server only delivers to peers connected to that same server — so if the
 * chip homes on a different region than a peer it must reach, its relayed
 * DISCO/WG-init never arrives and the link only forms after a `tailscale ping`
 * FROM that peer. Target selection is §4.2/§6 (neg_target_region above); the
 * apply path is lock/legacy/MBB (neg_apply_target). Called wherever a pinned
 * peer's derp_region is (re)learned, plus the 3 s self-heal cadence. */
static void maybe_rehome_to_priority(microlink_t * ml, const ml_peer_t * p)
{
  s_diag_rehome_calls++;
  if (p->derp_region == 0) {
    s_diag_rehome_ret_region0++;
    return;
  }
  if (!is_pinned_peer(ml, p->vpn_ip)) {
    s_diag_rehome_ret_notpinned++;
    return;
  }
  s_diag_rehome_body++;
  uint8_t src = MICROLINK_REGION_SRC_AUTO;
  uint16_t target = neg_target_region(ml, p, &src);
  if (target == 0) {
    return; /* no local choice — today's server-HomeDERP default stands (§6) */
  }
  neg_apply_target(ml, target, src);
}

static int find_peer_by_disco_key(microlink_t * ml, const uint8_t * disco_key)
{
  for (int i = 0; i < ml->peer_count; i++) {
    if (ml->peers[i].active && memcmp(ml->peers[i].disco_key, disco_key, 32) == 0) {
      return i;
    }
  }
  return -1;
}

/* Install ml->peers[idx] into wireguard-lwip so inbound handshake
 * initiations from this peer's static key get answered.
 *
 * Shared by the netmap ingest path (add_peer) and the boot-time NVS peer
 * preseed (ml_wg_mgr_task). The preseed exists because of the cold-bond
 * far-side gap (bench 2026-08-08/09): after a machine (machn) reboot, its
 * coordination netmap can be slow — or entirely blocked — to re-arrive, and
 * until each operator remote's key is installed here the WG layer SILENTLY
 * ignores that remote's handshake initiations. The remote then sits at
 * peer-present-but-no-keypair: sess_sendto ERR_CONN -> errno ENOTCONN,
 * sent=0, for 27 min on the bench; restarting the REMOTE did not help, only
 * a machn restart (fresh netmap) did. Installing the NVS-cached peers at
 * boot lets those inbound handshakes succeed immediately, netmap or not. */
static void wg_install_iface_peer(microlink_t * ml, int idx)
{
  ml_peer_t * p = &ml->peers[idx];
  if (!ml->wg_netif || p->wg_peer_index >= 0) {
    return; /* no WG interface yet, or already installed */
  }
  struct netif * netif = (struct netif *)ml->wg_netif;

  /* Convert peer public key to base64 */
  char peer_b64[64];
  key_to_base64(p->public_key, peer_b64, sizeof(peer_b64));

  struct wireguardif_peer wg_peer;
  wireguardif_peer_init(&wg_peer);

  wg_peer.public_key = peer_b64;
  wg_peer.preshared_key = NULL;

  /* Allowed IP: PEER's VPN IP
     * wireguard-lwip uses allowed_ip for TWO purposes:
     * 1. Outbound routing: peer_lookup_by_allowed_ip() matches DESTINATION
     *    IP to find which peer to route to (wireguardif.c:338)
     * 2. Inbound validation: checks decrypted packet SOURCE IP matches
     *    peer's allowed_source_ips (wireguardif.c:507)
     * Must be set to the PEER's VPN IP for both to work correctly. */
  uint8_t ip_a = (p->vpn_ip >> 24) & 0xFF;
  uint8_t ip_b = (p->vpn_ip >> 16) & 0xFF;
  uint8_t ip_c = (p->vpn_ip >> 8) & 0xFF;
  uint8_t ip_d = p->vpn_ip & 0xFF;
  IP4_ADDR(&wg_peer.allowed_ip.u_addr.ip4, ip_a, ip_b, ip_c, ip_d);
  IP4_ADDR(&wg_peer.allowed_mask.u_addr.ip4, 255, 255, 255, 255);

  /* Start every peer DERP-only — NEVER install a netmap-advertised endpoint
   * as the live WG endpoint.
   *
   * Root cause of the DERP-only-unreachable bug (2026-08-02): the
   * netmap/STUN endpoints a peer advertises are UNVALIDATED candidates. We
   * keep them in p->endpoints[] purely for DISCO probing. But
   * wireguardif_add_peer() copies wg_peer.endpoint_ip straight into
   * peer->ip (wireguardif.c:1084-1087), and wireguardif_peer_output()
   * (wireguardif.c:158) then routes ALL WireGuard traffic — including the
   * handshake RESPONSE — to peer->ip via direct UDP, bypassing DERP
   * entirely whenever peer->ip is non-any.
   *
   * Behind a hard / endpoint-dependent NAT that advertised endpoint is
   * unreachable in the peer->chip direction, so every reply the chip sends
   * blackholes and the WG session never forms — while relayed DISCO pongs
   * (which process_disco_ping sends *explicitly* over DERP) still return,
   * producing the pathognomonic "tailscale ping OK / TCP+HTTP data dead"
   * asymmetry (relay rx stuck at a few hundred bytes).
   *
   * Fix: leave the live endpoint blank so the peer is DERP-homed. The live
   * direct endpoint is installed only after PROOF of bidirectional
   * reachability — a txid-matched DISCO direct pong (process_disco_pong ->
   * wireguardif_update_endpoint + wireguardif_connect) or a genuinely
   * received direct WG packet (update_peer_addr roaming). This mirrors
   * tailscaled/magicsock: DERP-home first, upgrade to a direct path only
   * once it is validated both ways. DISCO probing of p->endpoints[]
   * continues to run, so genuinely reachable direct paths still upgrade
   * within one probe interval. */
  ip_addr_set_any(false, &wg_peer.endpoint_ip);
  wg_peer.endport_port = 0;

  wg_peer.keep_alive = 25;

  u8_t wg_peer_idx = WIREGUARDIF_INVALID_INDEX;
  err_t wg_err = wireguardif_add_peer(netif, &wg_peer, &wg_peer_idx);

  if (wg_err == ERR_OK && wg_peer_idx != WIREGUARDIF_INVALID_INDEX) {
    p->wg_peer_index = wg_peer_idx;

    /* Verify the WG internal peer key matches what we passed */
    struct wireguard_device * dev = (struct wireguard_device *)netif->state;
    if (dev && wg_peer_idx < WIREGUARD_MAX_PEERS) {
      struct wireguard_peer * wp = &dev->peers[wg_peer_idx];
      bool key_match = (memcmp(wp->public_key, p->public_key, 32) == 0);
      ESP_LOGI(
        TAG,
        "WG peer added: wg_idx=%d internal_key=%02x%02x%02x%02x %s",
        wg_peer_idx,
        wp->public_key[0],
        wp->public_key[1],
        wp->public_key[2],
        wp->public_key[3],
        key_match ? "KEY_OK" : "KEY_MISMATCH!");
    }

    /* DON'T initiate handshakes to all peers on add — Tailscale's lazy
         * peer config means our INIT to an idle peer gets dropped on their
         * end. EXCEPT for the priority peer (set via priority_peer_ip): for
         * that one we actively send WG INIT via DERP. The peer's
         * magicsock receiveIPv4() will see the DERP-delivered INIT, call
         * noteRecvActivity() → maybeReconfigWireguardLocked() to add us
         * to wireguard-go, then complete the handshake. This is how we
         * get a working WG session WITHOUT enabling DISCO (DISCO load
         * still wedges the chip on a busy tailnet even with allowlist
         * filtering of incoming probes — see v15.7.1 attempt). */
    if (ml->config.priority_peer_ip != 0 && p->vpn_ip == ml->config.priority_peer_ip) {
      wireguardif_connect_derp(netif, (u8_t)wg_peer_idx);
      /* Wake the remote's magicsock so it lazily adds us to
                 * wireguard-go. A bare WG-init relayed over DERP does NOT
                 * drive the peer's lazy reconfig — only an inbound DISCO
                 * ping does (that is why a normal peer otherwise has to
                 * `tailscale ping` us first). Fire one now, unconditionally
                 * (bypasses the enable_disco gate on the paths below); it is
                 * DERP-carried and embeds our node key, so a peer with a
                 * stale/rotated disco key can still map us. The sustained
                 * retry lives in disco_periodic_probes. */
      disco_send_ping_to_peer(ml, idx, true);
      /* Near-zero failover: mirror this peer's encrypted data over
                 * BOTH direct and DERP once a direct path forms. Set here and
                 * persisted in the WG peer struct (survives P7 re-ingests); it
                 * only takes effect while a direct endpoint exists, so it's a
                 * no-op until DISCO upgrades the path. */
      wireguardif_set_dual_path(netif, (u8_t)wg_peer_idx, true);
      ESP_LOGI(TAG, "WG: triggered DERP handshake to priority peer %s (dual-path)", p->hostname);
    } else {
      ESP_LOGI(TAG, "WG peer ready (passive), waiting for peer-initiated handshake");
    }
  } else {
    ESP_LOGW(TAG, "wireguardif_add_peer failed: %d", wg_err);
    p->wg_peer_index = -1;
  }
}

/* §7c learned-region stash: REMOVE→re-ADD of a pinned peer lands in a fresh
 * (or reused) slot with nothing to preserve, and machn's map omits the fleet
 * node's region — so the learned region died on every re-ingest cycle and
 * mirror diversity silently followed. Keyed by vpn_ip (pin identity is
 * IP-keyed; also survives key rotation), TTL-bounded so a fleet that MOVED
 * regions while absent cannot pin a stale one indefinitely. wg_mgr-task-owned. */
typedef struct
{
  uint32_t vpn_ip;
  uint16_t region;
  uint64_t stamp_ms;
} region_stash_t;

static region_stash_t s_region_stash[ML_REGION_STASH_SLOTS];
static uint32_t s_diag_region_stash_restores;
static uint32_t s_diag_readds_skipped;
static uint32_t s_diag_allowlist_rejects;
/* Indexed by first-failing §7a skip clause: 0=!existing 1=no-wg-slot 2=vpn_ip
 * 3=disco_key 4=hostname 5=region 6=endpoints. */
static uint32_t s_diag_skipfail[7];

void ml_wg_get_ingest_diag(uint32_t out[3])
{
  out[0] = s_diag_readds_skipped;
  out[1] = s_diag_region_stash_restores;
  out[2] = s_diag_allowlist_rejects;
}

void ml_wg_get_skipfail_diag(uint32_t out[7])
{
  for (int i = 0; i < 7; i++) out[i] = s_diag_skipfail[i];
}

static void region_stash_put(uint32_t vpn_ip, uint16_t region)
{
  int slot = 0;
  for (int i = 0; i < ML_REGION_STASH_SLOTS; i++) {
    if (s_region_stash[i].vpn_ip == vpn_ip) {
      slot = i;
      break;
    }
    if (s_region_stash[i].stamp_ms < s_region_stash[slot].stamp_ms) slot = i;
  }
  s_region_stash[slot].vpn_ip = vpn_ip;
  s_region_stash[slot].region = region;
  s_region_stash[slot].stamp_ms = ml_get_time_ms();
}

static uint16_t region_stash_lookup(uint32_t vpn_ip)
{
  uint64_t now = ml_get_time_ms();
  for (int i = 0; i < ML_REGION_STASH_SLOTS; i++) {
    if (s_region_stash[i].vpn_ip == vpn_ip && now - s_region_stash[i].stamp_ms < ML_REGION_STASH_TTL_MS) {
      return s_region_stash[i].region;
    }
  }
  return 0;
}

/* Single membership test for the peer candidate table — the learn-from-ping
 * check, the alt-candidate dedup and the §7a re-add compare must all agree on
 * what "already holds this endpoint" means (they had drifted on is_ipv6). */
static bool peer_has_endpoint(const ml_peer_t * p, uint32_t ip, uint16_t port, bool is_ipv6)
{
  for (int i = 0; i < p->endpoint_count && i < ML_MAX_ENDPOINTS; i++) {
    if (p->endpoints[i].ip == ip && p->endpoints[i].port == port && p->endpoints[i].is_ipv6 == is_ipv6) {
      return true;
    }
  }
  return false;
}

/* Boot NVS preseed stores only a truncated hostname (ml_peer_nvs
 * hostname_short[7]) — a stored non-empty PREFIX of the update's name is
 * display drift, not a rename (identity is already pinned by public key +
 * vpn_ip + disco key at this point). Without this, EVERY preseeded peer took
 * one full X25519 re-add per boot (~128 needless adds = the boot storm).
 * Deliberate looseness: a REAL rename to a longer name sharing the stored
 * prefix also matches — hostname is display metadata only, and the skip
 * path's RAM refresh still adopts the new name, so nothing user-visible or
 * identity-relevant is lost. */
static bool readd_hostname_unchanged(const ml_peer_t * p, const ml_peer_update_t * u)
{
  if (strncmp(u->hostname, p->hostname, sizeof(p->hostname) - 1) == 0) return true;
  size_t sl = strnlen(p->hostname, sizeof(p->hostname) - 1);
  return sl > 0 && strncmp(u->hostname, p->hostname, sl) == 0;
}

/* §7a: does this re-add carry any endpoint we don't already hold? Subset test,
 * order-insensitive: learn-from-ping appends locally-learned endpoints that a
 * coord re-add never carries, so exact-list equality was defeated FOREVER for
 * every peer with active disco — the pinned peers took the full re-add path on
 * each re-ingest, and under re-bond churn those X25519 storms stalled the WG
 * and DERP tasks together (run-36 disarm cascade). Only a genuinely NEW
 * endpoint is a material change. */
static bool readd_endpoints_unchanged(const ml_peer_t * p, const ml_peer_update_t * u)
{
  for (int i = 0; i < u->endpoint_count && i < ML_MAX_ENDPOINTS; i++) {
    if (!peer_has_endpoint(p, u->endpoints[i].ip, u->endpoints[i].port, u->endpoints[i].is_ipv6)) {
      return false;
    }
  }
  return true;
}

static int add_peer(microlink_t * ml, const ml_peer_update_t * update, bool * skipped)
{
  /* Peer allowlist filter: don't waste WG slots on non-allowed peers.
     * Still process updates for existing peers (they may become allowed later).
     * Counts as SKIPPED: near-zero work, so it must not consume an ingest
     * pacing slot or trigger a wg-rx drain (run-39: rejects saturated the
     * pacing cap uncounted, stretching re-ingests over dozens of passes).
     * Pins are exempt INSIDE ml_config_peer_is_allowed() — centralized there
     * so the disco/probe/preseed gates inherit it too (f498 root cause). */
  if (!ml_config_peer_is_allowed(ml->config_httpd, update->vpn_ip)) {
    s_diag_allowlist_rejects++;
    if (skipped) *skipped = true;
    return -1;
  }

  /* Check if peer already exists */
  bool existing = false;
  int idx = find_peer_by_key(ml, update->public_key);
  if (idx >= 0) {
    existing = true;
    ESP_LOGI(TAG, "Updating existing peer %s (idx=%d)", update->hostname, idx);
  } else {
    /* Effective cap: the runtime-configured max_peers (NVS/admin) when
         * set and below the compile-time ceiling, else ML_MAX_PEERS. Lets an
         * operator trim the active peer set at runtime — fewer peers probed
         * and box-opened = less embedded load — without a rebuild. The
         * priority peer is exempt (its eviction path below still runs to the
         * full ceiling), so trimming can never lock out the safety peer. */
    int eff_max = ML_MAX_PEERS;
    uint8_t cfg_mp = ml_config_get_max_peers(ml->config_httpd);
    if (cfg_mp > 0u && (int)cfg_mp < eff_max) {
      eff_max = (int)cfg_mp;
    }

    /* Key-rotated peer: the update's key is unknown but its VPN IP may
         * already be occupied by a STALE entry (e.g. an NVS-cached peer
         * preseeded at boot whose far end has since re-keyed). Two live
         * entries with one allowed_ip would make wireguard-lwip's
         * routing-by-IP ambiguous and find_peer_by_ip() would keep returning
         * the dead one — so retire the stale entry and reuse its slot. */
    idx = find_peer_by_ip(ml, update->vpn_ip);
    if (idx >= 0) {
      /* Hitless re-ingest: if the "stale" entry is a SAFETY peer whose session
       * is authenticating data RIGHT NOW, the old key is provably still in use
       * — this update is transient/bogus (netmap churn), not a real re-key.
       * Defer: skip the whole update. A genuine re-key stops authenticating
       * within seconds and the retry lands on the next coord update. */
      if (teardown_vetoed(ml, update->vpn_ip, ml->peers[idx].wg_peer_index)) {
        s_diag_rekey_retire_vetoes++;
        ESP_LOGW(
          TAG, "IGNORING re-key retire for %s: session still passing authenticated data (deferred)", update->hostname);
        if (skipped) *skipped = true; /* deferred, no add work — no pacing slot */
        return -1;
      }
      s_diag_rekey_retires++;
      ESP_LOGW(TAG, "Peer %s re-keyed — retiring stale entry (idx=%d)", update->hostname, idx);
      if (ml->peers[idx].wg_peer_index >= 0 && ml->wg_netif) {
        wireguardif_remove_peer((struct netif *)ml->wg_netif, (u8_t)ml->peers[idx].wg_peer_index);
      }
      /* §7c: retire is the second door a pinned peer's learned region exits
       * through (a fleet tailscaled restart rotates the key; retire is not
       * vetoed for pinned-but-not-safety peers). Stash it — the re-add with
       * the NEW key consumes it in this same call. */
      if (is_pinned_peer(ml, ml->peers[idx].vpn_ip) && ml->peers[idx].derp_region != 0) {
        region_stash_put(ml->peers[idx].vpn_ip, ml->peers[idx].derp_region);
      }
      ml->peers[idx].active = false;
    }

    /* Find free slot */
    idx = -1;
    for (int i = 0; i < eff_max; i++) {
      if (!ml->peers[i].active) {
        idx = i;
        break;
      }
    }

    /* Peer table full, and this peer isn't pinned yet — but the application
         * (machn) may still need it: an incoming peer whose device identity is on
         * the operator allowlist must be kept, or the machine never learns its WG
         * key and the remote can never bond. Pin it NOW (bounded set: operators
         * are ≤ DCS_MAX_OPERATORS) so is_pinned_peer() below is true and the
         * existing LRU-evict-for-pinned path makes room; pinning also persists it
         * for future netmap syncs. Stop-only accept-all remotes are NOT pinned
         * here and remain best-effort. Null cb (e.g. remotes) = current behavior. */
    if (
      idx < 0 && !is_pinned_peer(ml, update->vpn_ip) && ml->peer_wanted_cb != NULL &&
      ml->peer_wanted_cb(ml->peer_wanted_ctx, update->hostname, update->vpn_ip))
    {
      microlink_pin_peer_ip(ml, update->vpn_ip, true);
    }

    /* Peer table full — evict LRU non-pinned peer if the incoming peer is
         * pinned (priority/safety peer OR the management server). */
    if (idx < 0 && is_pinned_peer(ml, update->vpn_ip)) {
      uint64_t oldest_ms = UINT64_MAX;
      int evict_idx = -1;
      for (int i = 0; i < ML_MAX_PEERS; i++) {
        if (!ml->peers[i].active) continue;
        if (is_pinned_peer(ml, ml->peers[i].vpn_ip)) continue;
        /* Never LRU-evict a safety peer, pinned or not — evicting the peer
         * carrying the 5 Hz heartbeat is a guaranteed machine STOP. */
        if (is_safety_peer(ml, ml->peers[i].vpn_ip)) {
          s_diag_evict_safety_skips++;
          continue;
        }
        uint64_t last_activity = ml->peers[i].last_send_ms;
        if (ml->peers[i].last_pong_recv_ms > last_activity) last_activity = ml->peers[i].last_pong_recv_ms;
        if (last_activity < oldest_ms) {
          oldest_ms = last_activity;
          evict_idx = i;
        }
      }
      if (evict_idx >= 0) {
        char evict_ip[16];
        microlink_ip_to_str(ml->peers[evict_idx].vpn_ip, evict_ip);
        ESP_LOGW(
          TAG,
          "Evicting LRU peer %s (%s) for priority peer %s",
          ml->peers[evict_idx].hostname,
          evict_ip,
          update->hostname);
        if (ml->peers[evict_idx].wg_peer_index >= 0 && ml->wg_netif) {
          wireguardif_remove_peer((struct netif *)ml->wg_netif, ml->peers[evict_idx].wg_peer_index);
        }
        ml->peers[evict_idx].active = false;
        idx = evict_idx;
      }
    }

    if (idx < 0) {
      /* On a 130+-node tailnet this fires per rejected patch entry — a steady
       * log storm (147 lines/s measured at a DUT core-stall). Count always,
       * log at most once per 10 s with the count folded in. */
      s_diag_peer_table_full++;
      if (skipped) *skipped = true; /* zero-work refusal — must not burn a pacing slot (review 🟡) */
      uint64_t now_ms = esp_timer_get_time() / 1000ULL;
      if (now_ms - s_peer_table_full_log_ms >= 10000ULL) {
        s_peer_table_full_log_ms = now_ms;
        ESP_LOGW(
          TAG,
          "Peer table full (%d slots), cannot add %s (%lu refusals total, log rate-limited)",
          ML_MAX_PEERS,
          update->hostname,
          (unsigned long)s_diag_peer_table_full);
      }
      return -1;
    }
    if (idx >= ml->peer_count) {
      ml->peer_count = idx + 1;
    }
  }

  ml_peer_t * p = &ml->peers[idx];

  /* §7a skip-unchanged re-add: full re-ingests re-ADD every peer each
   * re-register; when nothing material changed, the only consequential
   * effect below is ml_peer_nvs_save() dirtying the peer cache — whose
   * debounced FLASH flush suspends both cores (the run-34 stall clusters).
   * Skip everything except the two load-bearing RAM-only side effects:
   * LRU protection (rebuilt each boot) and the relay-retry re-arm. Any
   * material change — dropped WG slot, IP/disco-key/hostname/region/
   * endpoint delta — takes the full path. Hostname compared in stored-
   * truncation space so an over-long name cannot defeat the skip forever.
   * skipfail = FIRST failing clause, counted per clause (run-38: the
   * pins' adds=4 persisted after the endpoint subset fix — attribute the
   * defeat with data, not hypotheses). */
  int skipfail = -1;
  if (!existing)
    skipfail = 0;
  else if (p->wg_peer_index < 0)
    skipfail = 1;
  else if (update->vpn_ip != p->vpn_ip)
    skipfail = 2;
  else if (memcmp(update->disco_key, p->disco_key, 32) != 0)
    skipfail = 3;
  else if (!readd_hostname_unchanged(p, update))
    skipfail = 4;
  else if (update->derp_region != 0 && update->derp_region != p->derp_region)
    skipfail = 5;
  else if (!readd_endpoints_unchanged(p, update))
    skipfail = 6;
  if (skipfail >= 0 && skipfail <= 6) s_diag_skipfail[skipfail]++;

  if (skipfail < 0) {
    if (
      is_pinned_peer(ml, p->vpn_ip) ||
      (ml->peer_wanted_cb != NULL && ml->peer_wanted_cb(ml->peer_wanted_ctx, p->hostname, p->vpn_ip)))
    {
      ml_peer_nvs_set_protected(p->vpn_ip); /* protected set is RAM-only */
    }
    if (
      update->endpoint_count > 0 && !p->has_direct_path &&
      (is_pinned_peer(ml, p->vpn_ip) || is_health_tracked(p->vpn_ip)))
    {
      p->relay_retry_next_ms = 1; /* identical endpoints still re-arm the sweep */
    }
    if (strncmp(update->hostname, p->hostname, sizeof(p->hostname) - 1) != 0) {
      /* Truncated-preseed prefix matched: recover the full display name.
       * RAM-only — the next NVS save re-truncates regardless. */
      strlcpy(p->hostname, update->hostname, sizeof(p->hostname));
    }
    s_diag_readds_skipped++;
    if (skipped) *skipped = true;
    return idx;
  }

  p->vpn_ip = update->vpn_ip;
  memcpy(p->public_key, update->public_key, 32);
  memcpy(p->disco_key, update->disco_key, 32);
  strlcpy(p->hostname, update->hostname, sizeof(p->hostname));
  /* Preserve a previously-learned DERP region. Full peer re-syncs frequently
     * re-add a peer with derp_region=0 (the region is carried separately, via
     * PeersChangedPatch), and unconditionally overwriting wiped the pinned
     * peer's known region back to 0 — so maybe_rehome() below early-returned and
     * the chip never stayed homed on the server's region. Behind a symmetric NAT
     * (USB tether) DERP relay is the only path, so this left the unit
     * permanently unreachable. Only overwrite when the update actually carries a
     * region. */
  if (update->derp_region != 0) {
    p->derp_region = update->derp_region;
  } else if (!existing) {
    /* Fresh (or reused) slot: nothing to preserve — a reused slot's leftover
     * region from a PREVIOUS occupant must not leak in (slot contamination
     * feeds maybe_rehome + the aux want-set). Consult the pinned-peer stash
     * instead: a re-added pin recovers its learned region across the
     * REMOVE→ADD cycle that re-ingests otherwise lose (task #42). */
    p->derp_region = region_stash_lookup(update->vpn_ip);
    if (p->derp_region != 0) s_diag_region_stash_restores++;
  }
  p->active = true;
  maybe_rehome_to_priority(ml, p);

  /* Copy endpoints — but PRESERVE previously-learned ones when the update
     * carries none. Full peer re-syncs (coord reconnect / long-poll re-sync)
     * can deliver a peer entry with an empty Endpoints array, and blindly
     * copying endpoint_count=0 wiped the stored candidates, leaving the
     * peer DERP-only until the next endpoint patch (observed on the bench:
     * a 46h-uptime unit with an empty candidate list for a peer whose
     * netmap endpoints other units held fine). Same rationale as the
     * derp_region preservation above. */
  if (update->endpoint_count > 0) {
    p->endpoint_count = update->endpoint_count;
    for (int i = 0; i < update->endpoint_count && i < ML_MAX_ENDPOINTS; i++) {
      p->endpoints[i].ip = update->endpoints[i].ip;
      p->endpoints[i].port = update->endpoints[i].port;
      p->endpoints[i].is_ipv6 = update->endpoints[i].is_ipv6;
    }
    /* Fresh endpoints arrived for an EXISTING relay-bound safety peer (e.g. the
     * coord re-fetch triggered by the symmetric-NAT relay-stuck recovery): re-arm
     * the relay-retry sweep to fire on the NEXT tick so we ping the NEW endpoint
     * immediately instead of waiting out the exponential backoff — re-hole-punch
     * fast, shrinking the relay window. nonzero-and-in-the-past => fires next tick. */
    if (existing && !p->has_direct_path && (is_pinned_peer(ml, p->vpn_ip) || is_health_tracked(p->vpn_ip))) {
      p->relay_retry_next_ms = 1;
    }
  } else if (!existing) {
    p->endpoint_count = 0; /* fresh/reused slot: never inherit a previous
                            * occupant's endpoints (slot contamination) */
  }

  /* Initialize DISCO/direct-path state — ONLY for a genuinely new peer.
     * A full "Peers" list is re-ingested (as ML_PEER_ADD per peer) on every
     * coord reconnect / long-poll re-sync / rebind. Resetting an EXISTING
     * peer here dropped its established direct path (has_direct_path=false,
     * best_ip=0, wg_peer_index=-1) and, for the priority peer, forced a
     * connect_derp + full re-discovery on every such event — a needless
     * safety-link gap. Preserve the live path for existing peers; the
     * endpoint delta-patch path (ML_PEER_UPDATE_ENDPOINT) handles real
     * endpoint changes. */
  if (!existing) {
    p->last_ping_sent_ms = 0;
    p->last_pong_recv_ms = 0;
    p->trust_until_ms = 0;
    p->last_send_ms = 0;
    p->last_upgrade_ms = 0;
    p->has_direct_path = false;
    p->best_ip = 0;
    p->best_port = 0;
    p->wg_peer_index = -1;
    /* Direct-path flap-backoff + DERP throttle state (net/derp-stability): reset
     * on slot REUSE too, else an evicted peer's stale direct_backoff_until would
     * spuriously suppress this fresh peer's direct-upgrade probing for up to 60 s. */
    p->direct_promoted_ms = 0;
    p->direct_flap_count = 0;
    p->direct_backoff_until = 0;
    p->last_derp_reconnect_ms = 0;
    p->relay_retry_next_ms = 0;
    p->relay_retry_count = 0;
    /* Coord re-fetch backoff too: an evicted peer parked at the 30 min cap must
     * not hand that wait to the fresh peer landing in its slot (@claude, #134). */
    p->relay_refetch_interval_ms = 0;
    p->relay_refetch_next_ms = 0;
    /* CMM chain-breaker throttle: an evicted slot's stale stamp would eat the
     * fresh peer's first CallMeMaybe for up to ML_DISCO_CMM_MIN_INTERVAL_MS. */
    p->last_cmm_sent_ms = 0;
    /* WG re-establishment state (ml_wg_regain_policy.h): a predecessor's connect
     * stamp would pace the fresh safety peer's first connect() by up to 5 s, and
     * its one-shot flag would deny a fresh bulk peer its single initiation. */
    p->last_safety_connect_ms = 0;
    p->tried_initial_handshake = false;
  }

  char ip_str[16];
  microlink_ip_to_str(update->vpn_ip, ip_str);
  ESP_LOGI(
    TAG,
    "Peer added: %s (%s) idx=%d endpoints=%d derp=%d key=%02x%02x%02x%02x%02x%02x%02x%02x",
    p->hostname,
    ip_str,
    idx,
    p->endpoint_count,
    p->derp_region,
    p->public_key[0],
    p->public_key[1],
    p->public_key[2],
    p->public_key[3],
    p->public_key[4],
    p->public_key[5],
    p->public_key[6],
    p->public_key[7]);

  /* Add to wireguard-lwip — only for a new peer, or an existing one whose
     * previous WG add failed (wg_peer_index < 0). An existing peer with a
     * live WG slot is left in place so its session/endpoint survives this
     * re-ingest (P7 — see the DISCO-state note above). */
  if (!existing || p->wg_peer_index < 0) {
    wg_install_iface_peer(ml, idx);
  }

  /* Persist to NVS for fast boot next time. Bond-critical peers — the
     * priority/fleet pins AND any peer the app wants kept (machn's operator
     * allowlist via peer_wanted_cb; all bounded sets) — are marked protected
     * so the peer cache's LRU eviction can never drop the very keys the
     * boot-time preseed needs (cold-bond far-side gap, 2026-08-08). Note the
     * pin path above only fires when the RAM table is FULL; the cb is asked
     * again here so operator keys are protected on small tailnets too. */
  if (
    is_pinned_peer(ml, p->vpn_ip) ||
    (ml->peer_wanted_cb != NULL && ml->peer_wanted_cb(ml->peer_wanted_ctx, p->hostname, p->vpn_ip)))
  {
    ml_peer_nvs_set_protected(p->vpn_ip);
  }
  ml_peer_nvs_save(p);

  /* Send CallMeMaybe to trigger peer-initiated handshake (NAT traversal). */
  disco_send_call_me_maybe(ml, idx);

  /* Immediately probe known endpoints (throttled to avoid flooding with 100s of peers).
     * Only force-ping if fewer than 5 peers added in the last second;
     * the periodic probe (every 15s) will handle the rest. */
  {
    static uint64_t last_burst_ms = 0;
    static int burst_count = 0;
    uint64_t add_now = ml_get_time_ms();
    if (add_now - last_burst_ms > 1000) {
      burst_count = 0;
      last_burst_ms = add_now;
    }
    if (burst_count < 5) {
      disco_send_ping_to_peer(ml, idx, true);
      burst_count++;
    }
  }

  /* Notify app via callback */
  if (ml->peer_cb) {
    microlink_peer_info_t info = {
      .vpn_ip = p->vpn_ip,
      .online = true,
      .direct_path = false,
    };
    strlcpy(info.hostname, p->hostname, sizeof(info.hostname));
    memcpy(info.public_key, p->public_key, 32);
    ml->peer_cb(ml, &info, ml->peer_cb_data);
  }

  return idx;
}

static void remove_peer(microlink_t * ml, const ml_peer_update_t * update)
{
  int idx = find_peer_by_key(ml, update->public_key);
  if (idx < 0) return;

  /* Hitless re-ingest: a coord REMOVE for a SAFETY peer whose session is
   * authenticating data RIGHT NOW is presumptively a server glitch (netmap
   * trim/re-sync churn) — applying it fails the 5 Hz heartbeat ENOTCONN and
   * stops the machine. Defer: keep the live session; a genuinely-removed
   * peer's session goes stale within seconds and a later REMOVE (or the
   * peer's own disappearance) applies. Fail toward keeping a working safety
   * bond, never toward a tidy peer table. */
  if (teardown_vetoed(ml, ml->peers[idx].vpn_ip, ml->peers[idx].wg_peer_index)) {
    s_diag_remove_vetoes++;
    ESP_LOGW(
      TAG,
      "IGNORING coord REMOVE for %s: session still passing authenticated data (deferred)",
      ml->peers[idx].hostname);
    return;
  }
  s_diag_peer_removes++;

  /* Remove from wireguard-lwip */
  if (ml->wg_netif && ml->peers[idx].wg_peer_index >= 0) {
    struct netif * netif = (struct netif *)ml->wg_netif;
    wireguardif_remove_peer(netif, (u8_t)ml->peers[idx].wg_peer_index);
  }

  char ip_str[16];
  microlink_ip_to_str(ml->peers[idx].vpn_ip, ip_str);
  ESP_LOGI(TAG, "Peer removed: %s (%s)", ml->peers[idx].hostname, ip_str);

  /* §7c: a pinned peer's learned region survives the REMOVE→re-ADD cycle
   * full re-ingests produce (the re-ADD often carries region 0). */
  if (is_pinned_peer(ml, ml->peers[idx].vpn_ip) && ml->peers[idx].derp_region != 0) {
    region_stash_put(ml->peers[idx].vpn_ip, ml->peers[idx].derp_region);
  }

  ml->peers[idx].active = false;

  /* Compact peer_count */
  while (ml->peer_count > 0 && !ml->peers[ml->peer_count - 1].active) {
    ml->peer_count--;
  }
}

static void process_peer_updates(microlink_t * ml)
{
  ml_peer_update_t * update;
  int adds_this_pass = 0;
  bool paced_out = false;
  while (!paced_out && (xQueueReceive(ml->peer_update_queue, &update, 0) == pdTRUE)) {
    if (!update) continue;
    switch (update->action) {
      case ML_PEER_ADD: {
        bool skipped = false;
        add_peer(ml, update, &skipped);
        /* Each REAL add costs an X25519 (~30 ms) — pace those, and interleave
             * a wg-rx drain after each so a heartbeat is never starved behind a
             * netmap-resync burst. A skipped unchanged re-add is ~µs: no pacing
             * slot and no drain — ML_WG_HS_REQUEUE_MAX sizing assumes at most
             * ML_PEER_ADDS_PER_PASS drains per pass, and a long all-unchanged
             * re-ingest must not pop a budget-deferred handshake to its requeue
             * cap within a single pass. */
        if (!skipped) {
          wg_mgr_drain_wg_rx(ml);
          adds_this_pass++;
          s_pass_peer_adds++;
          if (adds_this_pass >= ML_PEER_ADDS_PER_PASS) {
            paced_out = true;
          }
        }
        break;
      }
      case ML_PEER_REMOVE:
        remove_peer(ml, update);
        break;
      case ML_PEER_UPDATE_ENDPOINT:
        /* Update endpoint/DERP for existing peer (delta patch) */
        {
          int idx = find_peer_by_key(ml, update->public_key);
          if (idx >= 0) {
            ml_peer_t * p = &ml->peers[idx];
            if (update->endpoint_count > 0) {
              p->endpoint_count = update->endpoint_count;
              for (int i = 0; i < update->endpoint_count && i < ML_MAX_ENDPOINTS; i++) {
                p->endpoints[i].ip = update->endpoints[i].ip;
                p->endpoints[i].port = update->endpoints[i].port;
                p->endpoints[i].is_ipv6 = update->endpoints[i].is_ipv6;
              }
            }
            if (update->derp_region > 0) {
              p->derp_region = update->derp_region;
              maybe_rehome_to_priority(ml, p);
            }
            /* Patches are genuine deltas: persist them. With §7a, unchanged
             * full re-adds no longer save, so this is now the ONLY route by
             * which patch-learned endpoints/regions reach the boot preseed. */
            if (update->endpoint_count > 0 || update->derp_region > 0) {
              ml_peer_nvs_save(p);
            }
            ESP_LOGI(TAG, "Peer patched: %s (eps=%d derp=%d)", p->hostname, p->endpoint_count, p->derp_region);
          }
        }
        break;
    }
    free(update);
  }
}

/* ============================================================================
 * DISCO Protocol
 * ========================================================================== */

static void disco_build_ping(microlink_t * ml, int peer_idx, uint8_t * out, size_t * out_len)
{
  ml_peer_t * p = &ml->peers[peer_idx];

  /* Plaintext: [type(1)][version(1)][txid(12)][nodekey(32)] = 46 bytes */
  uint8_t plaintext[46];
  plaintext[0] = DISCO_MSG_PING;
  plaintext[1] = 0; /* version */

  /* Generate random transaction ID */
  uint8_t txid[DISCO_TXID_LEN];
  esp_fill_random(txid, DISCO_TXID_LEN);
  memcpy(plaintext + 2, txid, DISCO_TXID_LEN);
  memcpy(plaintext + 14, ml->wg_public_key, 32);

  /* Generate random nonce */
  uint8_t nonce[DISCO_NONCE_LEN];
  esp_fill_random(nonce, DISCO_NONCE_LEN);

  /* Encrypt with NaCl box: our disco private key -> peer's disco public key */
  uint8_t ciphertext[46 + NACL_BOX_MACBYTES];
  nacl_box(ciphertext, plaintext, sizeof(plaintext), nonce, p->disco_key, ml->disco_private_key);

  /* Build packet: magic(6) + our_disco_pubkey(32) + nonce(24) + ciphertext(62) = 124 bytes */
  size_t pos = 0;
  memcpy(out + pos, DISCO_MAGIC, 6);
  pos += 6;
  memcpy(out + pos, ml->disco_public_key, 32);
  pos += 32;
  memcpy(out + pos, nonce, DISCO_NONCE_LEN);
  pos += DISCO_NONCE_LEN;
  memcpy(out + pos, ciphertext, sizeof(ciphertext));
  pos += sizeof(ciphertext);
  *out_len = pos;

  /* Track pending probe. General peers may only use the head of the table;
   * the ML_DISCO_PROBE_RESERVE_SLOTS tail is safety-peer-only, so tailnet
   * churn can never leave a safety ping unregistered (unmatched pong = no
   * endpoint learn = the run-46 wedge). */
  bool probe_safety = is_safety_peer(ml, p->vpn_ip);
  int scan_limit = probe_safety ? MAX_PENDING_PROBES : (MAX_PENDING_PROBES - ML_DISCO_PROBE_RESERVE_SLOTS);
  bool registered = false;
  for (int i = 0; i < scan_limit; i++) {
    if (!pending_probes[i].active) {
      memcpy(pending_probes[i].txid, txid, DISCO_TXID_LEN);
      pending_probes[i].peer_index = peer_idx;
      pending_probes[i].sent_ms = ml_get_time_ms();
      pending_probes[i].derp_match_ms = 0;
      pending_probes[i].safety = probe_safety;
      pending_probes[i].active = true;
      registered = true;
      /* Track the table's occupancy high water (probe_tbl_hw). Registration is
       * the only place occupancy grows, so sampling here catches every peak; a
       * drift-free full scan (64 flag reads) beats a live counter that would
       * need decrements at every retire/expire site. Slots 0..i-1 were all
       * occupied (first-free allocation), slots above i are scanned. */
      {
        uint32_t occupied = (uint32_t)i + 1u;
        for (int k = i + 1; k < MAX_PENDING_PROBES; k++) {
          if (pending_probes[k].active) occupied++;
        }
        if (occupied > s_diag_probe_tbl_hw) s_diag_probe_tbl_hw = occupied;
      }
      ESP_LOGI(
        TAG,
        "Probe registered slot=%d peer=%s txid=%02x%02x%02x%02x",
        i,
        p->hostname,
        txid[0],
        txid[1],
        txid[2],
        txid[3]);
      break;
    }
  }
  if (!registered) {
    /* Record the saturation at the size of the REGION that overflowed — a
     * general-peer refusal with the safety reserve empty must not peg the
     * high-water at 64 and masquerade as true exhaustion (review 🟡). */
    if ((uint32_t)scan_limit > s_diag_probe_tbl_hw) s_diag_probe_tbl_hw = (uint32_t)scan_limit;
    ESP_LOGW(
      TAG,
      "DISCO probe table %s region full (%d slots), pong will be unmatched",
      probe_safety ? "FULL (incl safety reserve)" : "general",
      scan_limit);
  }
}

static void disco_build_pong(
  microlink_t * ml,
  int peer_idx,
  const uint8_t * txid,
  uint32_t src_ip,
  uint16_t src_port,
  uint8_t * out,
  size_t * out_len)
{
  ml_peer_t * p = &ml->peers[peer_idx];

  /* Plaintext: [type(1)][version(1)][txid(12)][src_addr(18)] = 32 bytes */
  /* src_addr: IPv6-mapped IPv4 (16 bytes) + port (2 bytes big-endian) */
  uint8_t plaintext[32];
  plaintext[0] = DISCO_MSG_PONG;
  plaintext[1] = 0;
  memcpy(plaintext + 2, txid, DISCO_TXID_LEN);

  /* IPv6-mapped IPv4: ::ffff:A.B.C.D */
  memset(plaintext + 14, 0, 10);
  plaintext[24] = 0xff;
  plaintext[25] = 0xff;
  plaintext[26] = (src_ip >> 24) & 0xFF;
  plaintext[27] = (src_ip >> 16) & 0xFF;
  plaintext[28] = (src_ip >> 8) & 0xFF;
  plaintext[29] = src_ip & 0xFF;
  plaintext[30] = (src_port >> 8) & 0xFF;
  plaintext[31] = src_port & 0xFF;

  /* Generate random nonce */
  uint8_t nonce[DISCO_NONCE_LEN];
  esp_fill_random(nonce, DISCO_NONCE_LEN);

  /* Encrypt */
  uint8_t ciphertext[32 + NACL_BOX_MACBYTES];
  nacl_box(ciphertext, plaintext, sizeof(plaintext), nonce, p->disco_key, ml->disco_private_key);

  /* Build packet */
  size_t pos = 0;
  memcpy(out + pos, DISCO_MAGIC, 6);
  pos += 6;
  memcpy(out + pos, ml->disco_public_key, 32);
  pos += 32;
  memcpy(out + pos, nonce, DISCO_NONCE_LEN);
  pos += DISCO_NONCE_LEN;
  memcpy(out + pos, ciphertext, sizeof(ciphertext));
  pos += sizeof(ciphertext);
  *out_len = pos;
}

/* When set, the next disco_send_ping_to_peer skips the 2 s pending-probe
 * dedup: the rx-silence path pings at ~1 Hz DURING an outage, where the dedup
 * would suppress exactly the punch that ends it. wg-task-only (single writer). */
static bool s_disco_ping_skip_dedup;

static void disco_send_ping_to_peer(microlink_t * ml, int peer_idx, bool force)
{
  ml_peer_t * p = &ml->peers[peer_idx];
  uint64_t now = ml_get_time_ms();

  /* Rate limit: don't ping more often than DISCO_PING_INTERVAL_MS (skip if forced) */
  if (!force && now - p->last_ping_sent_ms < ML_DISCO_PING_INTERVAL_MS) {
    return;
  }

  /* Probe dedup: multiple forced call-sites (disco_wake_peer, upgrade, demotion,
   * heartbeat) each register a fresh txid within the 5 s probe lifetime, piling
   * up outstanding probes. If this peer already has an ACTIVE probe younger than
   * 2 s, a fresh one is pure redundancy — skip it. The 2 s floor is well under
   * the 3 s liveness/heartbeat cadence (which also spaces last_ping_sent_ms by
   * >= 3 s), so a genuine liveness ping is never suppressed. */
  for (int pi = 0; !s_disco_ping_skip_dedup && pi < MAX_PENDING_PROBES; pi++) {
    if (
      pending_probes[pi].active && pending_probes[pi].peer_index == peer_idx && now - pending_probes[pi].sent_ms < 2000)
    {
      return;
    }
  }

  uint8_t pkt[256];
  size_t pkt_len = 0;
  disco_build_ping(ml, peer_idx, pkt, &pkt_len);

  if (pkt_len == 0) return;

  bool direct_sent = false;
  bool best_sent = false;

  /* If we have a known working direct path, send there FIRST.
     * This is critical for heartbeat pings to renew trust_until_ms.
     * A DERP pong would arrive with via_derp=true and NOT renew trust.
     *
     * Deliberately NOT gated on has_direct_path: after a demotion best_ip
     * still holds the last endpoint that PROVED bidirectionally reachable,
     * and it may no longer appear in endpoints[] (netmap patches replace the
     * candidate list). Keep probing it — a pong from it is exactly how the
     * direct path re-establishes. One bounded extra UDP send per ping. */
  if (p->best_ip != 0 && p->best_port != 0) {
    disco_udp_sendto(ml, pkt, pkt_len, p->best_ip, p->best_port);
    direct_sent = p->has_direct_path; /* demoted: still fall through to DERP */
    best_sent = true;
  }

  /* Also try direct UDP to all known endpoints from MapResponse */
  {
    bool has_udp = disco_has_udp_path(ml);
    if (has_udp) {
      for (int i = 0; i < p->endpoint_count; i++) {
        if (!p->endpoints[i].is_ipv6 && p->endpoints[i].ip != 0) {
          /* Skip if same as best_ip — but ONLY when the best-path branch above
           * actually sent there. After a demotion has_direct_path is false, so
           * that branch is skipped, yet best_ip/best_port still hold the
           * previously-proven endpoint. The unconditional skip here excluded
           * exactly that endpoint — for a NAT'd remote it is typically the ONLY
           * reachable candidate (the others need hairpin), so every re-probe
           * went DERP-only and the peer stayed relay-bound until reboot (which
           * clears best_ip). Root cause of the 2026-08 "stuck on DERP" bug. */
          if (best_sent && p->endpoints[i].ip == p->best_ip && p->endpoints[i].port == p->best_port) continue;
          int ret = disco_udp_sendto(ml, pkt, pkt_len, p->endpoints[i].ip, p->endpoints[i].port);
          if (!direct_sent) { /* Log only first direct send per peer */
            ESP_LOGI(
              TAG,
              "  direct probe -> %d.%d.%d.%d:%d (%d eps, ret=%d)",
              (int)((p->endpoints[i].ip >> 24) & 0xFF),
              (int)((p->endpoints[i].ip >> 16) & 0xFF),
              (int)((p->endpoints[i].ip >> 8) & 0xFF),
              (int)(p->endpoints[i].ip & 0xFF),
              (int)p->endpoints[i].port,
              p->endpoint_count,
              ret);
          }
          direct_sent = true;
        }
      }
    }
    /* Handshake-candidate leg (safety peers): the source of the most recent
     * DIRECT disco packet from this peer, as remembered by wireguardif for the
     * initiation second leg. Pinging it too keeps the far side's lazy
     * wireguard-go peer configured (only an inbound disco PING does that — a
     * bare WG initiation never re-adds a trimmed peer) and yields the pong the
     * normal direct regain needs, even when the candidate table lacks it. */
    if (has_udp && ml->wg_netif && p->wg_peer_index >= 0 && is_safety_peer(ml, p->vpn_ip)) {
      uint32_t cand_ip = 0;
      u16_t cand_port = 0;
      if (
        wireguardif_get_hs_candidate((struct netif *)ml->wg_netif, (u8_t)p->wg_peer_index, &cand_ip, &cand_port) ==
          ERR_OK &&
        cand_ip != 0 && !(best_sent && cand_ip == p->best_ip && cand_port == p->best_port) &&
        !peer_has_endpoint(p, cand_ip, cand_port, false))
      {
        (void)disco_udp_sendto(ml, pkt, pkt_len, cand_ip, cand_port);
        s_diag_hs_cand_pings++;
        direct_sent = true;
      }
    }
    if (!has_udp) {
      ESP_LOGW(TAG, "  no UDP path for %s (sock4=%d)", p->hostname, ml->disco_sock4);
    } else if (!direct_sent && p->endpoint_count > 0) {
      ESP_LOGW(TAG, "  %s: %d eps but none usable (all IPv6?)", p->hostname, p->endpoint_count);
    }
  }

  /* Send via DERP as fallback (or always for initial probes).
     * Skip DERP for heartbeat pings when direct path is active to avoid
     * DERP pong stealing the probe match from the direct pong. */
  if (!p->has_direct_path || !direct_sent) {
    ml_derp_queue_send(ml, p->public_key, pkt, pkt_len);
    ESP_LOGI(TAG, "DISCO PING -> %s via DERP", p->hostname);
  } else {
    ESP_LOGI(
      TAG,
      "DISCO PING -> %s via direct %d.%d.%d.%d:%d",
      p->hostname,
      (int)((p->best_ip >> 24) & 0xFF),
      (int)((p->best_ip >> 16) & 0xFF),
      (int)((p->best_ip >> 8) & 0xFF),
      (int)(p->best_ip & 0xFF),
      (int)p->best_port);
  }

  p->last_ping_sent_ms = now;
}
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
